LeoMendesEsEtml/2510_RegulationChauffage/doc/6.Graphique, Schéma/3.Doxygen/rtf/adc__ads124s08_8py.rtf

begin bodyRÃ©fÃ©rence du fichier C:/Users/thebi/Documents/2510_RegulationChauffage/doc/9.SoftWare/Doxygen/src/app/adc_ads124s08.py
AAAAAAAAAEAAAAAAAAAE
Driver pour l'ADC ADS124S08 avec communication SPI.
Classes
class app.adc_ads124s08.Ads124s08Driver pour l'ADC ADS124S08 avec interface SPI.
Espaces de nommage
namespace app
namespace app.adc_ads124s08
Fonctions
app.adc_ads124s08.encode_gain (pga_gain)
Encode le gain PGA en code binaire pour le registre.

app.adc_ads124s08.encode_idac_uA (idac_uA)
Encode la magnitude IDAC en code binaire pour le registre.

app.adc_ads124s08.sign_extend_24 (b0, b1, b2)
Ã‰tend le signe d'un code ADC 24 bits vers 32 bits.

Variables
int app.adc_ads124s08.REG_ID = 0x00
int app.adc_ads124s08.REG_STATUS = 0x01
int app.adc_ads124s08.REG_INPMUX = 0x02
int app.adc_ads124s08.REG_PGA = 0x03
int app.adc_ads124s08.REG_DATARATE = 0x04
int app.adc_ads124s08.REG_REF = 0x05
int app.adc_ads124s08.REG_IDACMUX = 0x07
int app.adc_ads124s08.REG_SYS = 0x09
int app.adc_ads124s08.REG_IDACMAG = 0x06
int app.adc_ads124s08.CMD_RESET = 0x06
int app.adc_ads124s08.CMD_START = 0x08
int app.adc_ads124s08.CMD_STOP = 0x0A
int app.adc_ads124s08.CMD_RDATA = 0x12
tuple app.adc_ads124s08.FS = (1 << 23) - 1
dict app.adc_ads124s08.CHANNELS

Description dÃ©taillÃ©e
Driver pour l'ADC ADS124S08 avec communication SPI.
Ce module fournit une interface complÃ¨te pour la communication avec l'ADC ADS124S08 via SPI en mode 1.0. Supporte la mesure de rÃ©sistance et tempÃ©rature avec configuration automatique des registres. SÃ Reset â†’ Configuration â†’ Mesure bloquante avec DRDY.
Auteur
LÃ©o Mendes @project 2510_RegulationsChauffage @Mandant Oblo_solution
Date
2025-09-18
Version
1.0.0
Copyright
Copyright (c) 2025
