LeoMendesEsEtml/2510_RegulationChauffage/doc/6.Graphique, Schéma/3.Doxygen/rtf/annotated.rtf

begin bodyListe des classes
Liste des classes, structures, unions et interfaces avec une brÃ¨ve description :
app.hw_mux_adg731.Adg731MuxSpi (Pilote SPI pour multiplexeurs ADG731 ) pagenum
app.adc_ads124s08.Ads124s08 (Driver pour l'ADC ADS124S08 avec interface SPI ) pagenum
app.api_client.ApiClient (Client pour interroger les APIs oblosolutions.ch ) pagenum
app.api_client.ApiError (Exception pour les erreurs d'API ) pagenum
app.front_led_management.LedErrorIndicator (Gestionnaire de LED avec patterns d'erreur ) pagenum
app.resistance_simulation.ResistanceSimulationError (Exception pour les erreurs de simulation de rÃ©sistance ) pagenum
app.resistance_simulation.ResistanceSimulator (ContrÃ´leur pour la simulation de rÃ©sistance via MUX ) pagenum
app.hw_tmux1204.Tmux1204 (Pilote pour le multiplexeur TMUX1204 ) pagenum
