LeoMendesEsEtml/2510_RegulationChauffage/doc/6.Graphique, Schéma/3.Doxygen/rtf/classapp_1_1adc__ads124s08_1_1_ads124s08.rtf

begin bodyRÃ©fÃ©rence de la classe app.adc_ads124s08.Ads124s08
AAAAAAAABSAAAAAAAABS
Driver pour l'ADC ADS124S08 avec interface SPI.
Graphe de collaboration de app.adc_ads124s08.Ads124s08:
IMAGE

Fonctions membres publiques
__init__ (self)
Constructeur de la classe Ads124s08.

read_id (self)
Lit le registre d'identification de l'ADC.

close (self)
Ferme les interfaces SPI et GPIO proprement.

wait_drdy_falling_edge (self, timeout_s)
Attend un front descendant sur DRDY (HIGH -> LOW) avec timeout.

set_single_shot_lowlatency (self, dr_nibble)
Configure le mode single-shot low-latency de l'ADC.

configure_channel (self, channel_index, pga_gain, idac_uA)
Configure un canal ADC avec ses paramÃ¨tres de mesure.

start (self)
DÃ©marre une conversion ADC.

stop (self)
ArrÃªte une conversion ADC en cours.

read_code24 (self)
Lit un code de donnÃ©es 24 bits depuis l'ADC.

measure_resistance (self, rref_ohm, pga_gain, timeout_s)
Mesure la rÃ©sistance d'une sonde via l'ADC.

measure_temperature (self, sensor_name, rref_ohm, pga_gain, timeout_s)
Mesure la tempÃ©rature d'un capteur via l'ADC.

read_gain (self)
Lit le registre de gain PGA pour diagnostic.

read_ref (self)
Lit le registre de configuration de la rÃ©fÃ©rence.

read_inpmux (self)
Lit le registre de configuration du multiplexeur d'entrÃ©e.

Attributs publics
spi = spidev.SpiDev()
gpio_drdy = GPIO(GPIO_CHIP_PATH, ADC_DRDY, "in")
Fonctions membres protÃ©gÃ©es
_rreg (self, addr, nbytes)
Lit un ou plusieurs registres de l'ADC via SPI.

_wreg (self, addr, data_bytes)
Ã‰crit dans un ou plusieurs registres de l'ADC via SPI.

_sclk_nudge (self)
Envoie un coup de pouce sur SCLK pour synchroniser DRDY.

_ensure_drdy_high (self, timeout_ms)
Assure que le signal DRDY est Ã l'Ã©tat HIGH.

Description dÃ©taillÃ©e
Driver pour l'ADC ADS124S08 avec interface SPI.
Cette classe encapsule toutes les fonctionnalitÃ©s nÃ©cessaires pour communiquer avec l'ADC ADS124S08 via SPI en mode 1.0. Supporte la configuration automatique, la mesure de rÃ©sistance et la conversion en tempÃ©rature.
Note
L'ADC doit Ãªtre connectÃ© via SPI1 et le signal DRDY sur GPIO.
Voir Ã©galement
configure_channel, measure_resistance, measure_temperature

AAAAAAAABTAAAAAAAABTDocumentation des constructeurs et destructeur
app.adc_ads124s08.Ads124s08.__init__ ( self)
AAAAAAAABUAAAAAAAABU
Constructeur de la classe Ads124s08.
Initialise la communication SPI, configure le GPIO DRDY, effectue un reset de l'ADC et vÃ©rifie la communication en lisant le registre d'identification.
Exceptions
Peut | lever des exceptions SPI ou GPIO en cas d'Ã©chec.
Postcondition L'ADC est prÃªt pour la configuration et les mesures.

AAAAAAAABVAAAAAAAABVDocumentation des fonctions membres
app.adc_ads124s08.Ads124s08._ensure_drdy_high ( self, timeout_ms)[protected]
AAAAAAAABWAAAAAAAABW
Assure que le signal DRDY est Ã l'Ã©tat HIGH.
Attend que DRDY passe Ã HIGH avec possibilitÃ© de coup de pouce sur SCLK si nÃ©cessaire. Timeout configurable.
ParamÃ¨tres
timeout_ms | Timeout en millisecondes pour l'attente.
Renvoie True si DRDY est HIGH, False en cas de timeout.
Note
MÃ©thode critique pour la synchronisation des conversions.
Voir Ã©galement
wait_drdy_falling_edge
Voici le graphe d'appel pour cette fonction :
IMAGE
app.adc_ads124s08.Ads124s08._rreg ( self, addr, nbytes)[protected]
AAAAAAAABXAAAAAAAABX
Lit un ou plusieurs registres de l'ADC via SPI.
Utilise la commande RREG de l'ADS124S08 pour lire des registres consÃ©cutifs starting Ã l'adresse donnÃ©e.
ParamÃ¨tres
addr | Adresse du premier registre Ã lire (0x00-0x1F).
nbytes | Nombre d'octets Ã lire.
Renvoie Liste des valeurs lues depuis les registres.
Note
MÃ©thode privÃ©e pour les opÃ©rations internes du driver.
Voir Ã©galement
_wreg
Voici le graphe des appelants de cette fonction :
IMAGE
app.adc_ads124s08.Ads124s08._sclk_nudge ( self)[protected]
AAAAAAAABYAAAAAAAABY
Envoie un coup de pouce sur SCLK pour synchroniser DRDY.
Effectue une lecture factice du registre STATUS pour gÃ©nÃ©rer des transitions sur SCLK et forcer DRDY Ã l'Ã©tat HIGH.
Renvoie
Rien.
Note
UtilisÃ© quand DRDY reste bloquÃ© Ã LOW de maniÃ¨re inattendue.
Voir Ã©galement
_ensure_drdy_high
Voici le graphe des appelants de cette fonction :
IMAGE
app.adc_ads124s08.Ads124s08._wreg ( self, addr, data_bytes)[protected]
AAAAAAAABZAAAAAAAABZ
Ã‰crit dans un ou plusieurs registres de l'ADC via SPI.
Utilise la commande WREG de l'ADS124S08 pour Ã©crire des donnÃ©es dans des registres consÃ©cutifs.
ParamÃ¨tres
addr | Adresse du premier registre Ã Ã©crire (0x00-0x1F).
data_bytes | Liste des octets Ã Ã©crire dans les registres.
Renvoie Rien.
Note
MÃ©thode privÃ©e pour les opÃ©rations internes du driver.
Voir Ã©galement
_rreg
Voici le graphe d'appel pour cette fonction :
IMAGE
Voici le graphe des appelants de cette fonction :
IMAGE
app.adc_ads124s08.Ads124s08.close ( self)
AAAAAAAACAAAAAAAAACA
Ferme les interfaces SPI et GPIO proprement.
LibÃ¨re les ressources systÃ¨me utilisÃ©es par le driver. MÃ©thode Ã appeler avant la destruction de l'objet.
Renvoie
Rien.
Note
Ignore les erreurs de fermeture pour Ã©viter les exceptions.
Voir Ã©galement
init
Voici le graphe d'appel pour cette fonction :
IMAGE
Voici le graphe des appelants de cette fonction :
IMAGE
app.adc_ads124s08.Ads124s08.configure_channel ( self, channel_index, pga_gain, idac_uA)
AAAAAAAACBAAAAAAAACB
Configure un canal ADC avec ses paramÃ¨tres de mesure.
Configure complÃ¨tement un canal ADC avec le gain PGA, le courant IDAC et le routage des entrÃ©es analogiques. Effectue une configuration sÃ©quentielle de tous les registres.
ParamÃ¨tres
channel_index | Index du canal physique (1-4).
pga_gain | Gain de l'amplificateur programmable (1-128).
idac_uA | Courant IDAC en microampÃ¨res (10-2000).
Renvoie Rien.
Exceptions
ValueError | si le canal ou les paramÃ¨tres sont invalides.
Voir Ã©galement encode_gain, encode_idac_uA
Voici le graphe d'appel pour cette fonction :
IMAGE
app.adc_ads124s08.Ads124s08.measure_resistance ( self, rref_ohm, pga_gain, timeout_s)
AAAAAAAACCAAAAAAAACC
Mesure la rÃ©sistance d'une sonde via l'ADC.
Effectue une mesure complÃ¨te: dÃ©marrage de conversion, attente DRDY, lecture du code et calcul de la rÃ©sistance selon la formule ratiomÃ©trique.
ParamÃ¨tres
rref_ohm | RÃ©sistance de rÃ©fÃ©rence en ohms.
pga_gain | Gain PGA utilisÃ© pour la mesure.
timeout_s | Timeout en secondes pour la conversion.
Renvoie RÃ©sistance mesurÃ©e en ohms ou None en cas d'erreur.
Note
Utilise la formule: R = |code|/FS * (Rref / gain).
Voir Ã©galement
measure_temperature, configure_channel
Voici le graphe d'appel pour cette fonction :
IMAGE
Voici le graphe des appelants de cette fonction :
IMAGE
app.adc_ads124s08.Ads124s08.measure_temperature ( self, sensor_name, rref_ohm, pga_gain, timeout_s)
AAAAAAAACDAAAAAAAACD
Mesure la tempÃ©rature d'un capteur via l'ADC.
Effectue une mesure de rÃ©sistance puis utilise les tables de conversion de capteurs pour obtenir la tempÃ©rature correspondante en degrÃ©s Celsius.
ParamÃ¨tres
sensor_name | Nom du capteur (doit exister dans SENSOR_TABLES).
rref_ohm | RÃ©sistance de rÃ©fÃ©rence en ohms.
pga_gain | Gain PGA utilisÃ© pour la mesure.
timeout_s | Timeout en secondes pour la conversion.
Renvoie TempÃ©rature mesurÃ©e en Â°C ou None si erreur.
Exceptions
Retourne | None si capteur inconnu ou hors plage.
Voir Ã©galement measure_resistance, resistance_to_temperature_dynamic
Voici le graphe d'appel pour cette fonction :
IMAGE
app.adc_ads124s08.Ads124s08.read_code24 ( self)
AAAAAAAACEAAAAAAAACE
Lit un code de donnÃ©es 24 bits depuis l'ADC.
Utilise la commande RDATA pour lire les 3 octets de donnÃ©es de conversion et les convertit en entier signÃ©.
Renvoie
Valeur signÃ©e 24 bits ou None en cas d'erreur SPI.
Note
Doit Ãªtre appelÃ© aprÃ¨s dÃ©tection du front descendant DRDY.
Voir Ã©galement
sign_extend_24, measure_resistance
Voici le graphe d'appel pour cette fonction :
IMAGE
Voici le graphe des appelants de cette fonction :
IMAGE
app.adc_ads124s08.Ads124s08.read_gain ( self)
AAAAAAAACFAAAAAAAACF
Lit le registre de gain PGA pour diagnostic.
Effectue une lecture du registre PGA et affiche sa valeur pour vÃ©rification de la configuration du gain.
Renvoie
Valeur brute du registre PGA (0x00-0xFF).
Note
UtilisÃ© principalement pour le debug et la vÃ©rification.
Voir Ã©galement
configure_channel
Voici le graphe d'appel pour cette fonction :
IMAGE
app.adc_ads124s08.Ads124s08.read_id ( self)
AAAAAAAACGAAAAAAAACG
Lit le registre d'identification de l'ADC.
Effectue une lecture du registre ID (0x00) pour vÃ©rifier la communication SPI et identifier le type d'ADC connectÃ©.
Renvoie
Valeur du registre ID (0x00-0xFF) ou None en cas d'erreur.
Note
UtilisÃ© principalement pour la vÃ©rification de communication.
Voir Ã©galement
init
app.adc_ads124s08.Ads124s08.read_inpmux ( self)
AAAAAAAACHAAAAAAAACH
Lit le registre de configuration du multiplexeur d'entrÃ©e.
Effectue une lecture du registre INPMUX et affiche sa valeur pour vÃ©rification du routage des entrÃ©es analogiques.
Renvoie
Valeur brute du registre INPMUX (0x00-0xFF).
Note
UtilisÃ© principalement pour le debug et la vÃ©rification.
Voir Ã©galement
configure_channel
app.adc_ads124s08.Ads124s08.read_ref ( self)
AAAAAAAACIAAAAAAAACI
Lit le registre de configuration de la rÃ©fÃ©rence.
Effectue une lecture du registre REF et affiche sa valeur pour vÃ©rification de la configuration de la rÃ©fÃ©rence.
Renvoie
Valeur brute du registre REF (0x00-0xFF).
Note
UtilisÃ© principalement pour le debug et la vÃ©rification.
Voir Ã©galement
configure_channel
Voici le graphe d'appel pour cette fonction :
IMAGE
app.adc_ads124s08.Ads124s08.set_single_shot_lowlatency ( self, dr_nibble)
AAAAAAAACJAAAAAAAACJ
Configure le mode single-shot low-latency de l'ADC.
Configure le registre DATARATE pour utiliser le mode single-shot avec filtre low-latency et data rate spÃ©cifiÃ©.
ParamÃ¨tres
dr_nibble | Code de data rate (4 bits, 0x00-0x0F).
Renvoie Rien.
Note
Mode optimisÃ© pour des mesures rapides et ponctuelles.
Voir Ã©galement
configure_channel
Voici le graphe des appelants de cette fonction :
IMAGE
app.adc_ads124s08.Ads124s08.start ( self)
AAAAAAAACKAAAAAAAACK
DÃ©marre une conversion ADC.
Assure que DRDY est Ã HIGH puis envoie la commande START pour initier une nouvelle conversion sur le canal configurÃ©.
Renvoie
Rien.
Note
DRDY doit Ãªtre HIGH avant le START pour une conversion valide.
Voir Ã©galement
stop, wait_drdy_falling_edge
Voici le graphe des appelants de cette fonction :
IMAGE
app.adc_ads124s08.Ads124s08.stop ( self)
AAAAAAAACLAAAAAAAACL
ArrÃªte une conversion ADC en cours.
Envoie la commande STOP pour interrompre toute conversion en cours et remettre l'ADC en Ã©tat idle.
Renvoie
Rien.
Note
UtilisÃ© aprÃ¨s lecture des donnÃ©es ou en cas d'erreur.
Voir Ã©galement
start, read_code24
Voici le graphe des appelants de cette fonction :
IMAGE
app.adc_ads124s08.Ads124s08.wait_drdy_falling_edge ( self, timeout_s)
AAAAAAAACMAAAAAAAACM
Attend un front descendant sur DRDY (HIGH -> LOW) avec timeout.
Surveille le signal DRDY pour dÃ©tecter une transition de HIGH vers LOW, indiquant qu'une nouvelle conversion est disponible.
ParamÃ¨tres
timeout_s | Timeout en secondes pour l'attente du front.
Renvoie True si front descendant dÃ©tectÃ©, False en cas de timeout.
Note
MÃ©thode cruciale pour la synchronisation des mesures.
Voir Ã©galement
measure_resistance
Voici le graphe d'appel pour cette fonction :
IMAGE
Voici le graphe des appelants de cette fonction :
IMAGE

AAAAAAAACNAAAAAAAACNDocumentation des donnÃ©es membres
app.adc_ads124s08.Ads124s08.gpio_drdy = GPIO(GPIO_CHIP_PATH, ADC_DRDY, "in")
AAAAAAAACOAAAAAAAACOapp.adc_ads124s08.Ads124s08.spi = spidev.SpiDev()
AAAAAAAACPAAAAAAAACP
La documentation de cette classe a Ã©tÃ© gÃ©nÃ©rÃ©e Ã partir du fichier suivant :
C:/Users/thebi/Documents/2510_RegulationChauffage/doc/9.SoftWare/Doxygen/src/app/adc_ads124s08.py
