LeoMendesEsEtml/2510_RegulationChauffage/doc/6.Graphique, Schéma/3.Doxygen/rtf/classapp_1_1front__led__management_1_1_led_error_indicator.rtf

begin bodyRÃ©fÃ©rence de la classe app.front_led_management.LedErrorIndicator
AAAAAAAADSAAAAAAAADS
Gestionnaire de LED avec patterns d'erreur.
Graphe de collaboration de app.front_led_management.LedErrorIndicator:
IMAGE

Attributs publics statiques
float BASE_BLINK_TIME = 0.2
float CYCLE_TIME = 10.0

Description dÃ©taillÃ©e
Gestionnaire de LED avec patterns d'erreur.
Classe pour contrÃ´ler une LED frontale avec diffÃ©rents patterns de clignotement selon les Ã©tats du systÃ¨me. Supporte les modes normal, standby, sÃ©quence en cours et divers patterns d'erreur avec clignotements codifiÃ©s.

AAAAAAAADTAAAAAAAADTDocumentation des donnÃ©es membres
float app.front_led_management.LedErrorIndicator.BASE_BLINK_TIME = 0.2[static]
AAAAAAAADUAAAAAAAADUfloat app.front_led_management.LedErrorIndicator.CYCLE_TIME = 10.0[static]
AAAAAAAADVAAAAAAAADV
La documentation de cette classe a Ã©tÃ© gÃ©nÃ©rÃ©e Ã partir du fichier suivant :
C:/Users/thebi/Documents/2510_RegulationChauffage/doc/9.SoftWare/Doxygen/src/app/front_led_management.py
