LeoMendesEsEtml/2510_RegulationChauffage/doc/6.Graphique, Schéma/3.Doxygen/rtf/classapp_1_1hw__mux__adg731_1_1_adg731_mux_spi.rtf

begin bodyRÃ©fÃ©rence de la classe app.hw_mux_adg731.Adg731MuxSpi
AAAAAAAADZAAAAAAAADZ
Pilote SPI pour multiplexeurs ADG731.
Graphe de collaboration de app.hw_mux_adg731.Adg731MuxSpi:
IMAGE

Fonctions membres publiques
__init__ (self, speed_hz=100000)
Initialise le pilote pour les multiplexeurs ADG731.

close (self)
Ferme toutes les interfaces SPI.

set_channel (self, board_index, address)
Active un canal spÃ©cifique sur une carte donnÃ©e.

set_output_channel (self, channel_index)
Utilitaire simple pour sÃ©lectionner un canal de sortie.

Attributs publics
speed = speed_hz
list handles = []
Attributs publics statiques
list DEV = ["/dev/spidev0.0", "/dev/spidev0.1", "/dev/spidev0.2", "/dev/spidev0.3"]

Description dÃ©taillÃ©e
Pilote SPI pour multiplexeurs ADG731.
Classe pour contrÃ´ler jusqu'Ã 4 multiplexeurs ADG731 via l'interface SPI0. Chaque multiplexeur peut gÃ©rer 32 canaux. Configure automatiquement les paramÃ¨tres SPI optimaux et gÃ¨re la communication avec les circuits.

AAAAAAAAEAAAAAAAAAEADocumentation des constructeurs et destructeur
app.hw_mux_adg731.Adg731MuxSpi.__init__ ( self, speed_hz = 100000)
AAAAAAAAEBAAAAAAAAEB
Initialise le pilote pour les multiplexeurs ADG731.
Configure l'interface SPI pour chaque canal disponible, dÃ©finit les paramÃ¨tres de communication et initialise les handles pour jusqu'Ã 4 cartes multiplexeurs.
ParamÃ¨tres
speed_hz | Vitesse SPI en Hz (par dÃ©faut 100kHz).

AAAAAAAAECAAAAAAAAECDocumentation des fonctions membres
app.hw_mux_adg731.Adg731MuxSpi.close ( self)
AAAAAAAAEDAAAAAAAAED
Ferme toutes les interfaces SPI.
Parcourt tous les handles SPI ouverts et les ferme proprement. GÃ¨re les erreurs de fermeture pour Ã©viter les exceptions lors du nettoyage.
app.hw_mux_adg731.Adg731MuxSpi.set_channel ( self, board_index, address)
AAAAAAAAEEAAAAAAAAEE
Active un canal spÃ©cifique sur une carte donnÃ©e.
Envoie la commande de sÃ©lection de canal vers la carte multiplexeur spÃ©cifiÃ©e. GÃ©nÃ¨re l'octet de contrÃ´le et l'envoie via SPI.
ParamÃ¨tres
board_index | Index de la carte (0-3).
address | Adresse du canal Ã activer (0-31).
Renvoie Octet de contrÃ´le envoyÃ©, ou None si erreur.
Exceptions
ValueError | Si l'index de carte est hors plage.
Voici le graphe d'appel pour cette fonction :
IMAGE
Voici le graphe des appelants de cette fonction :
IMAGE
app.hw_mux_adg731.Adg731MuxSpi.set_output_channel ( self, channel_index)
AAAAAAAAEFAAAAAAAAEF
Utilitaire simple pour sÃ©lectionner un canal de sortie.
Fonction de commoditÃ© qui utilise automatiquement la carte 0 et mappe directement l'index de canal sur l'adresse du multiplexeur.
ParamÃ¨tres
channel_index | Index du canal de sortie (0-31).
Renvoie Octet de contrÃ´le envoyÃ©, ou None si erreur.
Exceptions
ValueError | Si l'index de canal est hors plage.
Voici le graphe d'appel pour cette fonction :
IMAGE

AAAAAAAAEGAAAAAAAAEGDocumentation des donnÃ©es membres
list app.hw_mux_adg731.Adg731MuxSpi.DEV = ["/dev/spidev0.0", "/dev/spidev0.1", "/dev/spidev0.2", "/dev/spidev0.3"][static]
AAAAAAAAEHAAAAAAAAEHlist app.hw_mux_adg731.Adg731MuxSpi.handles = []
AAAAAAAAEIAAAAAAAAEIapp.hw_mux_adg731.Adg731MuxSpi.speed = speed_hz
AAAAAAAAEJAAAAAAAAEJ
La documentation de cette classe a Ã©tÃ© gÃ©nÃ©rÃ©e Ã partir du fichier suivant :
C:/Users/thebi/Documents/2510_RegulationChauffage/doc/9.SoftWare/Doxygen/src/app/hw_mux_adg731.py
