LeoMendesEsEtml/2510_RegulationChauffage/doc/6.Graphique, Schéma/3.Doxygen/rtf/classapp_1_1resistance__simulation_1_1_resistance_simulation_error.rtf

begin bodyRÃ©fÃ©rence de la classe app.resistance_simulation.ResistanceSimulationError
AAAAAAAAHOAAAAAAAAHO
Exception pour les erreurs de simulation de rÃ©sistance.
Graphe d'hÃ©ritage de app.resistance_simulation.ResistanceSimulationError:
IMAGE

Graphe de collaboration de app.resistance_simulation.ResistanceSimulationError:
IMAGE

Description dÃ©taillÃ©e
Exception pour les erreurs de simulation de rÃ©sistance.
Exception spÃ©cialisÃ©e levÃ©e lors d'erreurs dans le processus de simulation de rÃ©sistance via le multiplexeur.

La documentation de cette classe a Ã©tÃ© gÃ©nÃ©rÃ©e Ã partir du fichier suivant :
C:/Users/thebi/Documents/2510_RegulationChauffage/doc/9.SoftWare/Doxygen/src/app/resistance_simulation.py
