LeoMendesEsEtml/2510_RegulationChauffage/doc/6.Graphique, Schéma/3.Doxygen/rtf/classapp_1_1resistance__simulation_1_1_resistance_simulator.rtf

begin bodyRÃ©fÃ©rence de la classe app.resistance_simulation.ResistanceSimulator
AAAAAAAAHPAAAAAAAAHP
ContrÃ´leur pour la simulation de rÃ©sistance via MUX.
Graphe de collaboration de app.resistance_simulation.ResistanceSimulator:
IMAGE

Fonctions membres publiques
__init__ (self, int speed_hz=100000)
Initialise le simulateur de rÃ©sistance.

close (self)
Ferme les connexions du simulateur.

float calculate_parallel_resistance (self, List[float] resistances)
Calcule la rÃ©sistance Ã©quivalente de rÃ©sistances en parallÃ¨le.

bool apply_resistance_simulation (self, float target_resistance, int measurement_channel, str sensor_type="Ni1000 TK5000")
Applique une rÃ©sistance simulÃ©e via le MUX sur le canal de mesure.

Dict[str, any] get_current_simulation (self)
Retourne l'Ã©tat actuel de la simulation.

bool validate_resistance_applied (self, float expected_resistance, float tolerance=0.10)
Valide que la rÃ©sistance appliquÃ©e correspond Ã l'attendu.

reset_simulation (self)
Remet la simulation Ã zÃ©ro (dÃ©sactive tous les canaux).

Attributs publics
mux = None
speed_hz = speed_hz
current_resistance = None
list active_channels = []

Description dÃ©taillÃ©e
ContrÃ´leur pour la simulation de rÃ©sistance via MUX.
Classe principale qui encapsule toute la logique de simulation de rÃ©sistance en utilisant le multiplexeur ADG731 et les mappings de rÃ©sistances calibrÃ©es.

AAAAAAAAHQAAAAAAAAHQDocumentation des constructeurs et destructeur
app.resistance_simulation.ResistanceSimulator.__init__ ( self, int speed_hz = 100000)
AAAAAAAAHRAAAAAAAAHR
Initialise le simulateur de rÃ©sistance.
Constructeur qui configure le multiplexeur ADG731 avec la vitesse SPI spÃ©cifiÃ©e et initialise les variables d'Ã©tat du simulateur.
ParamÃ¨tres
speed_hz | Vitesse de communication SPI en Hz (dÃ©faut: 100kHz).
Exceptions ResistanceSimulationError | si l'initialisation du MUX Ã©choue.

AAAAAAAAHSAAAAAAAAHSDocumentation des fonctions membres
bool app.resistance_simulation.ResistanceSimulator.apply_resistance_simulation ( self, float target_resistance, int measurement_channel, str sensor_type = "Ni1000 TK5000")
AAAAAAAAHTAAAAAAAAHT
Applique une rÃ©sistance simulÃ©e via le MUX sur le canal de mesure.
Fonction principale qui recherche le canal MUX optimal pour simuler la rÃ©sistance cible, configure le multiplexeur et mÃ©morise l'Ã©tat de la simulation.
ParamÃ¨tres
target_resistance | RÃ©sistance Ã simuler [Ohms].
measurement_channel | Canal sur lequel la mesure a Ã©tÃ© faite (info).
sensor_type | Type de sonde pour sÃ©lectionner la carte MUX.
Renvoie True si succÃ¨s, False en cas d'erreur.
float app.resistance_simulation.ResistanceSimulator.calculate_parallel_resistance ( self, List[float] resistances)
AAAAAAAAHUAAAAAAAAHU
Calcule la rÃ©sistance Ã©quivalente de rÃ©sistances en parallÃ¨le.
Applique la formule 1/Req = 1/R1 + 1/R2 + ... + 1/Rn pour calculer la rÃ©sistance Ã©quivalente d'un ensemble de rÃ©sistances connectÃ©es en parallÃ¨le.
ParamÃ¨tres
resistances | Liste des valeurs de rÃ©sistance en parallÃ¨le [Ohms].
Renvoie RÃ©sistance Ã©quivalente calculÃ©e [Ohms]. Retourne l'infini si la liste est vide.
app.resistance_simulation.ResistanceSimulator.close ( self)
AAAAAAAAHVAAAAAAAAHV
Ferme les connexions du simulateur.
MÃ©thode de nettoyage qui ferme proprement la connexion SPI avec le multiplexeur et libÃ¨re les ressources.
Voici le graphe d'appel pour cette fonction :
IMAGE
Voici le graphe des appelants de cette fonction :
IMAGE
Dict[str, any] app.resistance_simulation.ResistanceSimulator.get_current_simulation ( self)
AAAAAAAAHWAAAAAAAAHW
Retourne l'Ã©tat actuel de la simulation.
Fonction d'interrogation qui fournit un dictionnaire contenant toutes les informations sur l'Ã©tat actuel de la simulation de rÃ©sistance.
Renvoie
Dictionnaire contenant les informations actuelles:
▪ esistance: valeur appliquÃ©e [Ohms] ou None
▪ ctive_channels: liste des canaux MUX actifs
▪ ux_available: disponibilitÃ© du multiplexeur
app.resistance_simulation.ResistanceSimulator.reset_simulation ( self)
AAAAAAAAHXAAAAAAAAHX
Remet la simulation Ã zÃ©ro (dÃ©sactive tous les canaux).
ProcÃ©dure de nettoyage qui dÃ©sactive tous les canaux de tous les multiplexeurs et remet l'Ã©tat de simulation Ã sa configuration initiale.
bool app.resistance_simulation.ResistanceSimulator.validate_resistance_applied ( self, float expected_resistance, float tolerance = 0.10)
AAAAAAAAHYAAAAAAAAHY
Valide que la rÃ©sistance appliquÃ©e correspond Ã l'attendu.
Fonction de validation qui compare la rÃ©sistance actuellement appliquÃ©e avec la valeur attendue en tenant compte d'une tolÃ©rance relative spÃ©cifiÃ©e.
ParamÃ¨tres
expected_resistance | RÃ©sistance attendue pour la validation [Ohms].
tolerance | TolÃ©rance relative acceptÃ©e (dÃ©faut: 10%).
Renvoie True si la rÃ©sistance est dans la tolÃ©rance.

AAAAAAAAHZAAAAAAAAHZDocumentation des donnÃ©es membres
list app.resistance_simulation.ResistanceSimulator.active_channels = []
AAAAAAAAIAAAAAAAAAIAapp.resistance_simulation.ResistanceSimulator.current_resistance = None
AAAAAAAAIBAAAAAAAAIBapp.resistance_simulation.ResistanceSimulator.mux = None
AAAAAAAAICAAAAAAAAICapp.resistance_simulation.ResistanceSimulator.speed_hz = speed_hz
AAAAAAAAIDAAAAAAAAID
La documentation de cette classe a Ã©tÃ© gÃ©nÃ©rÃ©e Ã partir du fichier suivant :
C:/Users/thebi/Documents/2510_RegulationChauffage/doc/9.SoftWare/Doxygen/src/app/resistance_simulation.py
