LeoMendesEsEtml/2510_RegulationChauffage/doc/6.Graphique, Schéma/3.Doxygen/rtf/cm5__config_8py.rtf

begin bodyRÃ©fÃ©rence du fichier C:/Users/thebi/Documents/2510_RegulationChauffage/doc/9.SoftWare/Doxygen/src/config_module/cm5_config.py
AAAAAAAAAUAAAAAAAAAU
Configuration matÃ©rielle pour plateforme CM5.
Espaces de nommage
namespace config_module
namespace config_module.cm5_config
Fonctions
config_module.cm5_config.build_hw ()
Initialise et configure tout le matÃ©riel CM5.

Variables
list config_module.cm5_config.ADC_CHANNELS = [1, 2, 3, 4]

Description dÃ©taillÃ©e
Configuration matÃ©rielle pour plateforme CM5.
Ce module fournit la configuration des canaux ADC et la fonction d'initialisation complÃ¨te du matÃ©riel (LED, TMUX, ADC). Centralise la crÃ©ation des instances matÃ©rielles avec cÃ¢blage fixe CM5.
Auteur
LÃ©o Mendes @project 2510_RegulationsChauffage @Mandant Oblo_solution
Date
2025-09-18
Version
1.0.0
Copyright
Copyright (c) 2025
