LeoMendesEsEtml/2510_RegulationChauffage/doc/6.Graphique, Schéma/3.Doxygen/rtf/config__loader_8py.rtf

begin bodyRÃ©fÃ©rence du fichier C:/Users/thebi/Documents/2510_RegulationChauffage/doc/9.SoftWare/Doxygen/src/app/config_loader.py
AAAAAAAAAGAAAAAAAAAG
Chargeur de configuration JSON pour le systÃ¨me de mesure.
Espaces de nommage
namespace app
namespace app.config_loader
Fonctions
app.config_loader.load_config (path)

Description dÃ©taillÃ©e
Chargeur de configuration JSON pour le systÃ¨me de mesure.
Ce module fournit une fonction simple pour charger et parser un fichier de configuration JSON contenant les paramÃ¨tres des capteurs, timeouts et autres paramÃ¨tres systÃ¨me.
Auteur
LÃ©o Mendes @project 2510_RegulationsChauffage @Mandant Oblo_solution
Date
2025-09-18
Version
1.0.0
Copyright
Copyright (c) 2025
