LeoMendesEsEtml/2510_RegulationChauffage/doc/6.Graphique, Schéma/3.Doxygen/rtf/dir_194a6b39714955f6d6b57228b865c8d6.rtf

begin bodyRÃ©pertoire de rÃ©fÃ©rence de C:/Users/thebi/Documents/2510_RegulationChauffage/doc/9.SoftWare/Doxygen/src/app
AAAAAAAAKPAAAAAAAAKPGraphe des dÃ©pendances de rÃ©pertoires pour app:
IMAGE
Fichiers
fichier __init__.py
fichier adc_ads124s08.py
Driver pour l'ADC ADS124S08 avec communication SPI.
fichier api_client.py
Client API pour les services oblosolutions.ch.
fichier config_loader.py
Chargeur de configuration JSON pour le systÃ¨me de mesure.
fichier front_led_management.py
Gestionnaire de LED frontale avec patterns d'erreur.
fichier hw_mux_adg731.py
Pilote pour multiplexeur ADG731 via interface SPI.
fichier hw_tmux1204.py
Pilote pour multiplexeur TMUX1204 de sÃ©lection de rÃ©sistance de rÃ©fÃ©rence.
fichier main.py
SystÃ¨me de mesure et simulation de tempÃ©rature.
fichier mesure_24v_dry_contact.py
Module de test des entrÃ©es/sorties 24V pour contacts secs.
fichier pins_cm5.py
Mapping GPIO et SPI fixÃ©s pour la plateforme CM5.
fichier resistance_mapping.py
Mapping des rÃ©sistances TMUX par type de sonde de tempÃ©rature.
fichier resistance_simulation.py
Module pour commander le MUX de simulation de rÃ©sistance.
fichier sensor_profiles.py
Profils capteurs extraits de 'Calcul ADC.xlsx' (Feuil1).
fichier temperature_conversion.py
Module de conversion rÃ©sistance/tempÃ©rature via interpolation linÃ©aire.
fichier temperature_simulation.py
Module de calcul de tempÃ©rature simulÃ©e selon formule prÃ©dictive.
fichier test_lm70_compatible.py
fichier test_spi_adc.py
