LeoMendesEsEtml/2510_RegulationChauffage/doc/6.Graphique, Schéma/3.Doxygen/rtf/dir_eeb81aa684f40f7b9c7a7aac642db388.rtf

begin bodyRÃ©pertoire de rÃ©fÃ©rence de C:/Users/thebi/Documents/2510_RegulationChauffage/doc/9.SoftWare/Doxygen/src/config_module
AAAAAAAAKQAAAAAAAAKQGraphe des dÃ©pendances de rÃ©pertoires pour config_module:
IMAGE
Fichiers
fichier __init__.py
fichier cm5_config.py
Configuration matÃ©rielle pour plateforme CM5.
