LeoMendesEsEtml/2510_RegulationChauffage/doc/6.Graphique, Schéma/3.Doxygen/rtf/files.rtf

begin bodyListe des fichiers
Liste de tous les fichiers avec une brÃ¨ve description :
C:/Users/thebi/Documents/2510_RegulationChauffage/doc/9.SoftWare/Doxygen/src/app/__init__.py pagenum
C:/Users/thebi/Documents/2510_RegulationChauffage/doc/9.SoftWare/Doxygen/src/app/adc_ads124s08.py (Driver pour l'ADC ADS124S08 avec communication SPI ) pagenum
C:/Users/thebi/Documents/2510_RegulationChauffage/doc/9.SoftWare/Doxygen/src/app/api_client.py (Client API pour les services oblosolutions.ch ) pagenum
C:/Users/thebi/Documents/2510_RegulationChauffage/doc/9.SoftWare/Doxygen/src/app/config_loader.py (Chargeur de configuration JSON pour le systÃ¨me de mesure ) pagenum
C:/Users/thebi/Documents/2510_RegulationChauffage/doc/9.SoftWare/Doxygen/src/app/front_led_management.py (Gestionnaire de LED frontale avec patterns d'erreur ) pagenum
C:/Users/thebi/Documents/2510_RegulationChauffage/doc/9.SoftWare/Doxygen/src/app/hw_mux_adg731.py (Pilote pour multiplexeur ADG731 via interface SPI ) pagenum
C:/Users/thebi/Documents/2510_RegulationChauffage/doc/9.SoftWare/Doxygen/src/app/hw_tmux1204.py (Pilote pour multiplexeur TMUX1204 de sÃ©lection de rÃ©sistance de rÃ©fÃ©rence ) pagenum
C:/Users/thebi/Documents/2510_RegulationChauffage/doc/9.SoftWare/Doxygen/src/app/main.py (SystÃ¨me de mesure et simulation de tempÃ©rature ) pagenum
C:/Users/thebi/Documents/2510_RegulationChauffage/doc/9.SoftWare/Doxygen/src/app/mesure_24v_dry_contact.py (Module de test des entrÃ©es/sorties 24V pour contacts secs ) pagenum
C:/Users/thebi/Documents/2510_RegulationChauffage/doc/9.SoftWare/Doxygen/src/app/pins_cm5.py (Mapping GPIO et SPI fixÃ©s pour la plateforme CM5 ) pagenum
C:/Users/thebi/Documents/2510_RegulationChauffage/doc/9.SoftWare/Doxygen/src/app/resistance_mapping.py (Mapping des rÃ©sistances TMUX par type de sonde de tempÃ©rature ) pagenum
C:/Users/thebi/Documents/2510_RegulationChauffage/doc/9.SoftWare/Doxygen/src/app/resistance_simulation.py (Module pour commander le MUX de simulation de rÃ©sistance ) pagenum
C:/Users/thebi/Documents/2510_RegulationChauffage/doc/9.SoftWare/Doxygen/src/app/sensor_profiles.py (Profils capteurs extraits de 'Calcul ADC.xlsx' (Feuil1) ) pagenum
C:/Users/thebi/Documents/2510_RegulationChauffage/doc/9.SoftWare/Doxygen/src/app/temperature_conversion.py (Module de conversion rÃ©sistance/tempÃ©rature via interpolation linÃ©aire ) pagenum
C:/Users/thebi/Documents/2510_RegulationChauffage/doc/9.SoftWare/Doxygen/src/app/temperature_simulation.py (Module de calcul de tempÃ©rature simulÃ©e selon formule prÃ©dictive ) pagenum
C:/Users/thebi/Documents/2510_RegulationChauffage/doc/9.SoftWare/Doxygen/src/app/test_lm70_compatible.py pagenum
C:/Users/thebi/Documents/2510_RegulationChauffage/doc/9.SoftWare/Doxygen/src/app/test_spi_adc.py pagenum
C:/Users/thebi/Documents/2510_RegulationChauffage/doc/9.SoftWare/Doxygen/src/config_module/__init__.py pagenum
C:/Users/thebi/Documents/2510_RegulationChauffage/doc/9.SoftWare/Doxygen/src/config_module/cm5_config.py (Configuration matÃ©rielle pour plateforme CM5 ) pagenum
C:/Users/thebi/Documents/2510_RegulationChauffage/doc/9.SoftWare/Doxygen/src/webui/__init__.py pagenum
C:/Users/thebi/Documents/2510_RegulationChauffage/doc/9.SoftWare/Doxygen/src/webui/webui_server.py (Serveur web pour interface utilisateur de configuration ) pagenum
