LeoMendesEsEtml/2510_RegulationChauffage/doc/6.Graphique, Schéma/3.Doxygen/rtf/front__led__management_8py.rtf

begin bodyRÃ©fÃ©rence du fichier C:/Users/thebi/Documents/2510_RegulationChauffage/doc/9.SoftWare/Doxygen/src/app/front_led_management.py
AAAAAAAAAHAAAAAAAAAH
Gestionnaire de LED frontale avec patterns d'erreur.
Classes
class app.front_led_management.LedErrorIndicatorGestionnaire de LED avec patterns d'erreur.
Espaces de nommage
namespace app
namespace app.front_led_management
Fonctions
app.front_led_management.create_led_indicator (gpio_chip_path, led_pin)
Factory function pour crÃ©er une instance LedErrorIndicator.

Description dÃ©taillÃ©e
Gestionnaire de LED frontale avec patterns d'erreur.
Ce module fournit une classe pour gÃ©rer les clignotements et Ã©tats de la LED frontale avec diffÃ©rents patterns d'erreur. Supporte les modes continus, les clignotements d'erreur et la gestion thread-safe des patterns LED.
Auteur
LÃ©o Mendes @project 2510_RegulationsChauffage @Mandant Oblo_solution
Date
2025-09-18
Version
1.0.0
Copyright
Copyright (c) 2025
