LeoMendesEsEtml/2510_RegulationChauffage/doc/6.Graphique, Schéma/3.Doxygen/rtf/hierarchy.rtf

begin bodyHiÃ©rarchie des classes
Cette liste d'hÃ©ritage est classÃ©e approximativement par ordre alphabÃ©tique :
app.hw_mux_adg731.Adg731MuxSpi pagenum
app.adc_ads124s08.Ads124s08 pagenum
app.api_client.ApiClient pagenum
Exception
app.api_client.ApiError pagenum
app.resistance_simulation.ResistanceSimulationError pagenum

app.front_led_management.LedErrorIndicator pagenum
app.resistance_simulation.ResistanceSimulator pagenum
app.hw_tmux1204.Tmux1204 pagenum
