LeoMendesEsEtml/2510_RegulationChauffage/doc/6.Graphique, Schéma/3.Doxygen/rtf/hw__mux__adg731_8py.rtf

begin bodyRÃ©fÃ©rence du fichier C:/Users/thebi/Documents/2510_RegulationChauffage/doc/9.SoftWare/Doxygen/src/app/hw_mux_adg731.py
AAAAAAAAAIAAAAAAAAAI
Pilote pour multiplexeur ADG731 via interface SPI.
Classes
class app.hw_mux_adg731.Adg731MuxSpiPilote SPI pour multiplexeurs ADG731.
Espaces de nommage
namespace app
namespace app.hw_mux_adg731
Fonctions
app.hw_mux_adg731.adg731_ctrl_byte (address, enable=True)
GÃ©nÃ¨re le byte de contrÃ´le pour l'ADG731.

Description dÃ©taillÃ©e
Pilote pour multiplexeur ADG731 via interface SPI.
Ce module fournit un pilote pour contrÃ´ler les multiplexeurs ADG731 via l'interface SPI0. Supporte jusqu'Ã 4 cartes avec 32 canaux chacune. GÃ¨re la configuration SPI et l'envoi des commandes de contrÃ´le pour la sÃ©lection des canaux.
Auteur
LÃ©o Mendes @project 2510_RegulationsChauffage @Mandant Oblo_solution
Date
2025-09-18
Version
1.0.0
Copyright
Copyright (c) 2025
