LeoMendesEsEtml/2510_RegulationChauffage/doc/6.Graphique, Schéma/3.Doxygen/rtf/main_8py.rtf

begin bodyRÃ©fÃ©rence du fichier C:/Users/thebi/Documents/2510_RegulationChauffage/doc/9.SoftWare/Doxygen/src/app/main.py
AAAAAAAAAKAAAAAAAAAK
SystÃ¨me de mesure et simulation de tempÃ©rature.
Espaces de nommage
namespace app
namespace app.main
Fonctions
app.main.start_webui_server ()
Lance le serveur web local dans un thread sÃ©parÃ©.

app.main.save_last_state (channel=None, resistance_ohm=None, temperature_c=None, temperature_sim_c=None, error=None)
Sauvegarde l'Ã©tat courant et historique par canal dans un fichier JSON.

app.main.signal_handler (sig, frame)
Gestionnaire POSIX pour les signaux (Ctrl+C).

app.main.input_monitor ()
Thread d'Ã©coute des commandes utilisateur depuis stdin.

app.main.show_error_and_continue (error_pattern, sleep_time=2)
Affiche un motif LED d'erreur pendant un temps donnÃ© puis remet l'indicateur en mode 'sequence_running'.

app.main.run_measurement_sequence (cfg, mac_address, adc, tmux)
ExÃ©cute une sÃ©quence complÃ¨te de mesures pour tous les canaux activÃ©s selon la configuration fournie.

app.main.reload_timing_config ()
Recharge les paramÃ¨tres de temporisation depuis le fichier de configuration.

app.main.main ()
Point d'entrÃ©e principal du programme.

Variables
app.main.CURRENT_DIR = os.path.dirname(os.path.abspath(__file__))
app.main.SRC_DIR = os.path.dirname(CURRENT_DIR)
bool app.main.sequencer_running = False
app.main.stop_event = threading.Event()
app.main.force_sequence = threading.Event()
app.main.led_indicator = None

Description dÃ©taillÃ©e
SystÃ¨me de mesure et simulation de tempÃ©rature.
Ce module exÃ©cute des cycles de mesure ADC, convertit les valeurs en rÃ©sistances puis en tempÃ©ratures, rÃ©cupÃ¨re des paramÃ¨tres via une API distante, calcule une tempÃ©rature simulÃ©e, convertit cette tempÃ©rature en rÃ©sistance cible et applique la simulation via un multiplexeur matÃ©riel. Le module gÃ¨re Ã©galement un petit serveur web optionnel et un indicateur LED.
Auteur
LÃ©o Mendes @project 2510_RegulationsChauffage @Mandant Oblo_solution
Date
2025-09-18
Version
1.0.0
Copyright
Copyright (c) 2025
