LeoMendesEsEtml/2510_RegulationChauffage/doc/6.Graphique, Schéma/3.Doxygen/rtf/mesure__24v__dry__contact_8py.rtf

begin bodyRÃ©fÃ©rence du fichier C:/Users/thebi/Documents/2510_RegulationChauffage/doc/9.SoftWare/Doxygen/src/app/mesure_24v_dry_contact.py
AAAAAAAAALAAAAAAAAAL
Module de test des entrÃ©es/sorties 24V pour contacts secs.
Espaces de nommage
namespace app
namespace app.mesure_24v_dry_contact
Fonctions
app.mesure_24v_dry_contact.test_24v_dry_contact ()
Test des contacts secs I/O 24V.

app.mesure_24v_dry_contact.get_dry_contact_status ()
Retourne l'Ã©tat actuel des contacts secs.

Variables
int app.mesure_24v_dry_contact.CM_24V_OUT_1 = 13
int app.mesure_24v_dry_contact.CM_24V_SENSE_1 = 14
int app.mesure_24v_dry_contact.CM_24V_OUT_2 = 15
int app.mesure_24v_dry_contact.CM_24V_SENSE_2 = 16
int app.mesure_24v_dry_contact.io_24v_ch1_ok = 0
int app.mesure_24v_dry_contact.io_24v_ch2_ok = 0

Description dÃ©taillÃ©e
Module de test des entrÃ©es/sorties 24V pour contacts secs.
Ce module fournit des fonctions pour tester et valider les contacts secs via les interfaces I/O 24V. Permet de dÃ©tecter l'Ã©tat des contacts (ouvert/fermÃ©) sur deux canaux indÃ©pendants avec gestion des GPIO et temporisations appropriÃ©es.
Auteur
LÃ©o Mendes @project 2510_RegulationsChauffage @Mandant Oblo_solution
Date
2025-09-18
Version
1.0.0
Copyright
Copyright (c) 2025
