LeoMendesEsEtml/2510_RegulationChauffage/doc/6.Graphique, Schéma/3.Doxygen/rtf/namespaceapp.rtf

begin bodyRÃ©fÃ©rence de l'espace de nommage app
AAAAAAAAAWAAAAAAAAAWEspaces de nommage
namespace adc_ads124s08
namespace api_client
namespace config_loader
namespace front_led_management
namespace hw_mux_adg731
namespace hw_tmux1204
namespace main
namespace mesure_24v_dry_contact
namespace pins_cm5
namespace resistance_mapping
namespace resistance_simulation
namespace sensor_profiles
namespace temperature_conversion
namespace temperature_simulation
namespace test_lm70_compatible
namespace test_spi_adc
