LeoMendesEsEtml/2510_RegulationChauffage/doc/6.Graphique, Schéma/3.Doxygen/rtf/namespaceapp_1_1front__led__management.rtf

begin bodyRÃ©fÃ©rence de l'espace de nommage app.front_led_management
AAAAAAAADPAAAAAAAADPClasses
class LedErrorIndicatorGestionnaire de LED avec patterns d'erreur.
Fonctions
create_led_indicator (gpio_chip_path, led_pin)
Factory function pour crÃ©er une instance LedErrorIndicator.

AAAAAAAADQAAAAAAAADQDocumentation des fonctions
app.front_led_management.create_led_indicator ( gpio_chip_path, led_pin)
AAAAAAAADRAAAAAAAADR
Factory function pour crÃ©er une instance LedErrorIndicator.
Fonction utilitaire qui encapsule la crÃ©ation et l'initialisation d'un gestionnaire LED. GÃ¨re les erreurs d'initialisation et configure automatiquement le pattern normal par dÃ©faut.
ParamÃ¨tres
gpio_chip_path | Chemin vers le pÃ©riphÃ©rique GPIO.
led_pin | NumÃ©ro de pin de la LED.
Renvoie Instance de LedErrorIndicator si succÃ¨s, None sinon.
