LeoMendesEsEtml/2510_RegulationChauffage/doc/6.Graphique, Schéma/3.Doxygen/rtf/namespaceapp_1_1main.rtf

begin bodyRÃ©fÃ©rence de l'espace de nommage app.main
AAAAAAAAEVAAAAAAAAEVFonctions
start_webui_server ()
Lance le serveur web local dans un thread sÃ©parÃ©.

save_last_state (channel=None, resistance_ohm=None, temperature_c=None, temperature_sim_c=None, error=None)
Sauvegarde l'Ã©tat courant et historique par canal dans un fichier JSON.

signal_handler (sig, frame)
Gestionnaire POSIX pour les signaux (Ctrl+C).

input_monitor ()
Thread d'Ã©coute des commandes utilisateur depuis stdin.

show_error_and_continue (error_pattern, sleep_time=2)
Affiche un motif LED d'erreur pendant un temps donnÃ© puis remet l'indicateur en mode 'sequence_running'.

run_measurement_sequence (cfg, mac_address, adc, tmux)
ExÃ©cute une sÃ©quence complÃ¨te de mesures pour tous les canaux activÃ©s selon la configuration fournie.

reload_timing_config ()
Recharge les paramÃ¨tres de temporisation depuis le fichier de configuration.

main ()
Point d'entrÃ©e principal du programme.

Variables
CURRENT_DIR = os.path.dirname(os.path.abspath(__file__))
SRC_DIR = os.path.dirname(CURRENT_DIR)
bool sequencer_running = False
stop_event = threading.Event()
force_sequence = threading.Event()
led_indicator = None

AAAAAAAAEWAAAAAAAAEWDocumentation des fonctions
app.main.input_monitor ()
AAAAAAAAEXAAAAAAAAEX
Thread d'Ã©coute des commandes utilisateur depuis stdin.
Permet de forcer une sÃ©quence (touche EntrÃ©e ou 's') ou de demander l'arrÃªt ('q'). Les exceptions d'E/S sont gÃ©rÃ©es pour permettre la terminaison propre du thread.
Renvoie
None
Voici le graphe d'appel pour cette fonction :
IMAGE
app.main.main ()
AAAAAAAAEYAAAAAAAAEY
Point d'entrÃ©e principal du programme.
Parse les arguments de la ligne de commande, initialise le matÃ©riel (GPIO, ADC, MUX), le gestionnaire LED, et exÃ©cute le sÃ©quenceur en mode automatique ou manuel selon la configuration.
Renvoie
None
Voici le graphe d'appel pour cette fonction :
IMAGE
Voici le graphe des appelants de cette fonction :
IMAGE
app.main.reload_timing_config ()
AAAAAAAAEZAAAAAAAAEZ
Recharge les paramÃ¨tres de temporisation depuis le fichier de configuration.
Lit uniquement les paramÃ¨tres de temporisation pour mise Ã jour dynamique sans perturber le reste du systÃ¨me. UtilisÃ© pour permettre la modification des intervalles de sÃ©quence et du mode automatique via l'interface web.
Renvoie
Tuple (auto_sequence, sequence_interval_minutes, success) oÃ¹ success indique si le rechargement a rÃ©ussi.
Voici le graphe des appelants de cette fonction :
IMAGE
app.main.run_measurement_sequence ( cfg, mac_address, adc, tmux)
AAAAAAAAFAAAAAAAAAFA
ExÃ©cute une sÃ©quence complÃ¨te de mesures pour tous les canaux activÃ©s selon la configuration fournie.
Pour chaque canal actif : sÃ©lection du rref, configuration ADC, lecture des valeurs, conversion en tempÃ©rature, envoi API, calcul de la tempÃ©rature simulÃ©e et application via le simulateur de rÃ©sistance. Les motifs LED sont ajustÃ©s en fonction des erreurs.
ParamÃ¨tres
cfg | Dictionnaire de configuration chargÃ© depuis JSON.
mac_address | Adresse MAC ou identifiant pour les appels API.
adc | Instance de l'ADC (Ads124s08).
tmux | Instance du multiplexeur (Tmux1204).
Renvoie bool True si la sÃ©quence est globalement considÃ©rÃ©e comme rÃ©ussie, False sinon.
Voici le graphe d'appel pour cette fonction :
IMAGE
Voici le graphe des appelants de cette fonction :
IMAGE
app.main.save_last_state ( channel = None, resistance_ohm = None, temperature_c = None, temperature_sim_c = None, error = None)
AAAAAAAAFBAAAAAAAAFB
Sauvegarde l'Ã©tat courant et historique par canal dans un fichier JSON.
CrÃ©e le dossier state si nÃ©cessaire, lit le fichier last_state.json existant, met Ã jour les informations du canal fourni et Ã©crit le document au format JSON. Les erreurs internes sont capturÃ©es et affichÃ©es sur la sortie standard.
ParamÃ¨tres
channel | NumÃ©ro du canal (ou None).
resistance_ohm | RÃ©sistance mesurÃ©e (ou None).
temperature_c | TempÃ©rature mesurÃ©e [Â°C] (ou None).
temperature_sim_c | TempÃ©rature simulÃ©e [Â°C] (ou None).
error | Message d'erreur s'il y en a un (ou None).
Renvoie None
Voici le graphe des appelants de cette fonction :
IMAGE
app.main.show_error_and_continue ( error_pattern, sleep_time = 2)
AAAAAAAAFCAAAAAAAAFC
Affiche un motif LED d'erreur pendant un temps donnÃ© puis remet l'indicateur en mode 'sequence_running'.

ParamÃ¨tres
error_pattern | Nom du motif LED Ã afficher.
sleep_time | DurÃ©e d'affichage en secondes (par dÃ©faut 2s).
Renvoie None
Voici le graphe des appelants de cette fonction :
IMAGE
app.main.signal_handler ( sig, frame)
AAAAAAAAFDAAAAAAAAFD
Gestionnaire POSIX pour les signaux (Ctrl+C).
Met le drapeau sequencer_running Ã False et dÃ©clenche l'Ã©vÃ©nement stop_event pour demander un arrÃªt propre.
ParamÃ¨tres
sig | Signal reÃ§u (int).
frame | Contexte d'exÃ©cution (non utilisÃ©).
Renvoie None
Voici le graphe des appelants de cette fonction :
IMAGE
app.main.start_webui_server ()
AAAAAAAAFEAAAAAAAAFE
Lance le serveur web local dans un thread sÃ©parÃ©.
Import dynamique du module webui.webui_server et dÃ©marrage de l'application Flask/WSGI. Les exceptions sont interceptÃ©es et converties en messages sur la sortie standard pour ne pas interrompre le thread principal.
Renvoie
None

AAAAAAAAFFAAAAAAAAFFDocumentation des variables
app.main.CURRENT_DIR = os.path.dirname(os.path.abspath(__file__))
AAAAAAAAFGAAAAAAAAFGapp.main.force_sequence = threading.Event()
AAAAAAAAFHAAAAAAAAFHapp.main.led_indicator = None
AAAAAAAAFIAAAAAAAAFIbool app.main.sequencer_running = False
AAAAAAAAFJAAAAAAAAFJapp.main.SRC_DIR = os.path.dirname(CURRENT_DIR)
AAAAAAAAFKAAAAAAAAFKapp.main.stop_event = threading.Event()
AAAAAAAAFLAAAAAAAAFL
