LeoMendesEsEtml/2510_RegulationChauffage/doc/6.Graphique, Schéma/3.Doxygen/rtf/namespaceapp_1_1resistance__mapping.rtf

begin bodyRÃ©fÃ©rence de l'espace de nommage app.resistance_mapping
AAAAAAAAHBAAAAAAAAHBFonctions
dict get_channel_mux_map (str sensor_type)
Retourne le mapping CHANNEL_MUX pour un type de sonde donnÃ©.

tuple find_closest_channel (float target_resistance, str sensor_type)
Trouve le canal MUX le plus proche pour une rÃ©sistance cible.

Variables
dict CHANNEL_MUX

AAAAAAAAHCAAAAAAAAHCDocumentation des fonctions
tuple app.resistance_mapping.find_closest_channel (float target_resistance, str sensor_type)
AAAAAAAAHDAAAAAAAAHD
Trouve le canal MUX le plus proche pour une rÃ©sistance cible.
Algorithme de recherche du canal TMUX offrant la rÃ©sistance la plus proche de la valeur cible. Calcule l'erreur absolue et relative pour le meilleur canal trouvÃ©.
ParamÃ¨tres
target_resistance | Valeur de rÃ©sistance cible recherchÃ©e [Ohms].
sensor_type | Type de sonde Ã utiliser pour la recherche.
Renvoie Tuple (canal, resistance_reelle, erreur_pourcent). Retourne (None, None, None) si aucun canal trouvÃ©.
Exceptions
KeyError | si le type de sonde n'existe pas.
Voici le graphe d'appel pour cette fonction :
IMAGE
dict app.resistance_mapping.get_channel_mux_map (str sensor_type)
AAAAAAAAHEAAAAAAAAHE
Retourne le mapping CHANNEL_MUX pour un type de sonde donnÃ©.
Fonction d'accÃ¨s qui extrait le dictionnaire de correspondance canal/rÃ©sistance pour un type de sonde spÃ©cifique. Valide l'existence du type avant de retourner les donnÃ©es.
ParamÃ¨tres
sensor_type | Type de sonde demandÃ© (doit exister dans CHANNEL_MUX).
Renvoie Dictionnaire {canal: resistance} pour le type de sonde.
Exceptions
KeyError | si le type de sonde n'est pas supportÃ©.
Voici le graphe des appelants de cette fonction :
IMAGE

AAAAAAAAHFAAAAAAAAHFDocumentation des variables
dict app.resistance_mapping.CHANNEL_MUX
AAAAAAAAHGAAAAAAAAHG
