LeoMendesEsEtml/2510_RegulationChauffage/doc/6.Graphique, Schéma/3.Doxygen/rtf/namespaceapp_1_1resistance__simulation.rtf

begin bodyRÃ©fÃ©rence de l'espace de nommage app.resistance_simulation
AAAAAAAAHHAAAAAAAAHHClasses
class ResistanceSimulationErrorException pour les erreurs de simulation de rÃ©sistance.
class ResistanceSimulatorContrÃ´leur pour la simulation de rÃ©sistance via MUX.
Fonctions
bool apply_resistance_simulation (float resistance_ohm)
Fonction utilitaire pour appliquer une rÃ©sistance simulÃ©e.

Variables
sim = ResistanceSimulator()
bool success = sim.apply_resistance_simulation(1000.0)
valid = sim.validate_resistance_applied(667.0, tolerance=0.15)

AAAAAAAAHIAAAAAAAAHIDocumentation des fonctions
bool app.resistance_simulation.apply_resistance_simulation (float resistance_ohm)
AAAAAAAAHJAAAAAAAAHJ
Fonction utilitaire pour appliquer une rÃ©sistance simulÃ©e.
Fonction de commoditÃ© qui encapsule la crÃ©ation d'un simulateur, l'application d'une rÃ©sistance et le nettoyage automatique. Utilise le pattern RAII pour la gestion des ressources.
ParamÃ¨tres
resistance_ohm | RÃ©sistance Ã appliquer [Ohms].
Renvoie True si l'application a rÃ©ussi, False sinon.

AAAAAAAAHKAAAAAAAAHKDocumentation des variables
app.resistance_simulation.sim = ResistanceSimulator()
AAAAAAAAHLAAAAAAAAHLbool app.resistance_simulation.success = sim.apply_resistance_simulation(1000.0)
AAAAAAAAHMAAAAAAAAHMapp.resistance_simulation.valid = sim.validate_resistance_applied(667.0, tolerance=0.15)
AAAAAAAAHNAAAAAAAAHN
