LeoMendesEsEtml/2510_RegulationChauffage/doc/6.Graphique, Schéma/3.Doxygen/rtf/namespaceapp_1_1sensor__profiles.rtf

begin bodyRÃ©fÃ©rence de l'espace de nommage app.sensor_profiles
AAAAAAAAIEAAAAAAAAIEFonctions
get_profile (sensor_name)
RÃ©cupÃ¨re le profil de configuration ADC pour un capteur donnÃ©.

Variables
dict SENSOR_PROFILES

AAAAAAAAIFAAAAAAAAIFDocumentation des fonctions
app.sensor_profiles.get_profile ( sensor_name)
AAAAAAAAIGAAAAAAAAIG
RÃ©cupÃ¨re le profil de configuration ADC pour un capteur donnÃ©.
Fonction d'accÃ¨s qui retourne le dictionnaire de configuration contenant les paramÃ¨tres optimisÃ©s (Rref, IDAC, PGA) pour un type de capteur spÃ©cifique.
ParamÃ¨tres
sensor_name | Nom du type de capteur recherchÃ©.
Renvoie Dictionnaire contenant les paramÃ¨tres de configuration:
▪ ref_ohm: rÃ©sistance de rÃ©fÃ©rence [Ohms]
▪ dac_uA: courant d'excitation [microampÃ¨res]
▪ ga_gain: gain programmable [1-128]
Exceptions
KeyError | si le type de capteur n'est pas reconnu.

AAAAAAAAIHAAAAAAAAIHDocumentation des variables
dict app.sensor_profiles.SENSOR_PROFILES
AAAAAAAAIIAAAAAAAAII
