LeoMendesEsEtml/2510_RegulationChauffage/doc/6.Graphique, Schéma/3.Doxygen/rtf/namespaceapp_1_1temperature__conversion.rtf

begin bodyRÃ©fÃ©rence de l'espace de nommage app.temperature_conversion
AAAAAAAAIJAAAAAAAAIJFonctions
resistance_to_temperature (resistance, table)
Convertit une rÃ©sistance mesurÃ©e en tempÃ©rature via interpolation linÃ©aire.

resistance_to_temperature_dynamic (resistance, sensor)
Convertit une rÃ©sistance mesurÃ©e en tempÃ©rature pour un capteur donnÃ©.

temperature_to_resistance_dynamic (temperature, sensor)
Convertit une tempÃ©rature en rÃ©sistance pour un capteur donnÃ© (conversion inverse).

convert_temperature_to_resistance (temperature, probe_type)
Fonction de conversion principale pour la simulation de rÃ©sistance.

get_supported_probe_types ()
Retourne la liste des types de sondes supportÃ©s.

validate_temperature_range (temperature, probe_type)
Valide si une tempÃ©rature est dans la plage supportÃ©e par une sonde.

AAAAAAAAIKAAAAAAAAIKDocumentation des fonctions
app.temperature_conversion.convert_temperature_to_resistance ( temperature, probe_type)
AAAAAAAAILAAAAAAAAIL
Fonction de conversion principale pour la simulation de rÃ©sistance.
Fonction de haut niveau qui supporte diffÃ©rents types de sondes avec leurs caractÃ©ristiques spÃ©cifiques. Inclut la normalisation des noms de sondes et la gestion des variantes de nomenclature.
ParamÃ¨tres
temperature | TempÃ©rature simulÃ©e [Â°C].
probe_type | Type de sonde (formats multiples supportÃ©s).
Renvoie RÃ©sistance simulÃ©e [Ohms] ou None si Ã©chec.
Voici le graphe d'appel pour cette fonction :
IMAGE
app.temperature_conversion.get_supported_probe_types ()
AAAAAAAAIMAAAAAAAAIM
Retourne la liste des types de sondes supportÃ©s.
Fonction utilitaire qui extrait la liste complÃ¨te des noms de capteurs disponibles dans les tables de conversion.
Renvoie
Liste des noms de capteurs disponibles pour conversion.
app.temperature_conversion.resistance_to_temperature ( resistance, table)
AAAAAAAAINAAAAAAAAIN
Convertit une rÃ©sistance mesurÃ©e en tempÃ©rature via interpolation linÃ©aire.
Algorithme d'interpolation linÃ©aire qui recherche l'intervalle contenant la rÃ©sistance mesurÃ©e et calcule la tempÃ©rature correspondante. GÃ¨re les cas limites hors plage de mesure.
ParamÃ¨tres
resistance | RÃ©sistance mesurÃ©e [Ohms].
table | Liste de tuples (rÃ©sistance, tempÃ©rature) pour interpolation.
Renvoie TempÃ©rature interpolÃ©e [Â°C], ou valeurs limites si hors plage.
app.temperature_conversion.resistance_to_temperature_dynamic ( resistance, sensor)
AAAAAAAAIOAAAAAAAAIO
Convertit une rÃ©sistance mesurÃ©e en tempÃ©rature pour un capteur donnÃ©.
Fonction dynamique qui sÃ©lectionne automatiquement la table de conversion appropriÃ©e selon le type de capteur spÃ©cifiÃ©. Effectue la validation du capteur avant conversion.
ParamÃ¨tres
resistance | RÃ©sistance mesurÃ©e [Ohms].
sensor | Nom du type de capteur Ã utiliser.
Renvoie TempÃ©rature interpolÃ©e [Â°C] ou None si hors limites.
Exceptions
ValueError | si le capteur n'est pas reconnu.
app.temperature_conversion.temperature_to_resistance_dynamic ( temperature, sensor)
AAAAAAAAIPAAAAAAAAIP
Convertit une tempÃ©rature en rÃ©sistance pour un capteur donnÃ© (conversion inverse).
Fonction de conversion inverse utilisÃ©e pour la simulation de rÃ©sistance. Effectue l'interpolation linÃ©aire sur l'axe tempÃ©rature pour obtenir la rÃ©sistance correspondante selon le type de capteur.
ParamÃ¨tres
temperature | TempÃ©rature d'entrÃ©e [Â°C].
sensor | Nom du type de capteur Ã utiliser.
Renvoie RÃ©sistance interpolÃ©e [Ohms] ou None si hors limites.
Exceptions
ValueError | si le capteur n'est pas reconnu.
Voici le graphe des appelants de cette fonction :
IMAGE
app.temperature_conversion.validate_temperature_range ( temperature, probe_type)
AAAAAAAAIQAAAAAAAAIQ
Valide si une tempÃ©rature est dans la plage supportÃ©e par une sonde.
Fonction de validation qui vÃ©rifie si une tempÃ©rature donnÃ©e est compatible avec la plage de fonctionnement d'un type de capteur spÃ©cifique selon sa table de calibration.
ParamÃ¨tres
temperature | TempÃ©rature Ã valider [Â°C].
probe_type | Type de sonde Ã vÃ©rifier.
Renvoie True si la tempÃ©rature est dans la plage supportÃ©e.
