LeoMendesEsEtml/2510_RegulationChauffage/doc/6.Graphique, Schéma/3.Doxygen/rtf/namespaceconfig__module_1_1cm5__config.rtf

begin bodyRÃ©fÃ©rence de l'espace de nommage config_module.cm5_config
AAAAAAAAJSAAAAAAAAJSFonctions
build_hw ()
Initialise et configure tout le matÃ©riel CM5.

Variables
list ADC_CHANNELS = [1, 2, 3, 4]

AAAAAAAAJTAAAAAAAAJTDocumentation des fonctions
config_module.cm5_config.build_hw ()
AAAAAAAAJUAAAAAAAAJU
Initialise et configure tout le matÃ©riel CM5.
CrÃ©e les instances des composants matÃ©riels avec configuration fixe LED frontale, multiplexeur TMUX et ADC. Configure la LED en sortie et l'allume immÃ©diatement pour indication systÃ¨me.
Renvoie
Dictionnaire contenant toutes les instances matÃ©rielles:
▪ led": Instance GPIO pour LED frontale
▪ tmux": Instance Tmux1204 pour sÃ©lection canaux
▪ adc": Instance Ads124s08 pour conversion analogique
Avertissement
LED allumÃ©e automatiquement pour indiquer systÃ¨me actif.

AAAAAAAAJVAAAAAAAAJVDocumentation des variables
list config_module.cm5_config.ADC_CHANNELS = [1, 2, 3, 4]
AAAAAAAAJWAAAAAAAAJW
