LeoMendesEsEtml/2510_RegulationChauffage/doc/6.Graphique, Schéma/3.Doxygen/rtf/namespaces.rtf

begin bodyListe des espaces de nommage
Liste de tous les espaces de nommage avec une brÃ¨ve description:
app pagenum
app.adc_ads124s08 pagenum
app.api_client pagenum
app.config_loader pagenum
app.front_led_management pagenum
app.hw_mux_adg731 pagenum
app.hw_tmux1204 pagenum
app.main pagenum
app.mesure_24v_dry_contact pagenum
app.pins_cm5 pagenum
app.resistance_mapping pagenum
app.resistance_simulation pagenum
app.sensor_profiles pagenum
app.temperature_conversion pagenum
app.temperature_simulation pagenum
app.test_lm70_compatible pagenum
app.test_spi_adc pagenum
config_module pagenum
config_module.cm5_config pagenum
webui pagenum
webui.webui_server pagenum
