LeoMendesEsEtml/2510_RegulationChauffage/doc/6.Graphique, Schéma/3.Doxygen/rtf/pins__cm5_8py.rtf

begin bodyRÃ©fÃ©rence du fichier C:/Users/thebi/Documents/2510_RegulationChauffage/doc/9.SoftWare/Doxygen/src/app/pins_cm5.py
AAAAAAAAAMAAAAAAAAAM
Mapping GPIO et SPI fixÃ©s pour la plateforme CM5.
Espaces de nommage
namespace app
namespace app.pins_cm5
Variables
str app.pins_cm5.GPIO_CHIP_PATH = "/dev/gpiochip0"
int app.pins_cm5.MUX_CS_4 = 2
int app.pins_cm5.MUX_CS_3 = 3
int app.pins_cm5.MUX_CS_2 = 7
int app.pins_cm5.MUX_CS_1 = 8
int app.pins_cm5.MUX_MOSI_DUMMY = 10
int app.pins_cm5.MUX_SCLK_DUMMY = 11
int app.pins_cm5.CM_24V_OUT_1 = 13
int app.pins_cm5.CM_24V_SENSE_1 = 14
int app.pins_cm5.CM_24V_OUT_2 = 15
int app.pins_cm5.CM_24V_SENSE_2 = 16
int app.pins_cm5.CMD_RELAY = 17
int app.pins_cm5.CS_ADC_DUMMY = 18
int app.pins_cm5.SPI_MISO_ADC_DMY = 19
int app.pins_cm5.SPI_MOSI_ADC_DMY = 20
int app.pins_cm5.SPI_SCLK_ADC_DMY = 21
int app.pins_cm5.ADC_DRDY = 22
int app.pins_cm5.ADC_START_SYNC = 23
int app.pins_cm5.ADC_A0 = 24
int app.pins_cm5.ADC_A1 = 25
int app.pins_cm5.FRONT_LED = 27
int app.pins_cm5.SPI0_BUS = 0
int app.pins_cm5.SPI1_BUS = 1
int app.pins_cm5.SPI0_DEV0 = 0
int app.pins_cm5.SPI0_DEV1 = 1
int app.pins_cm5.SPI1_DEV0 = 0
int app.pins_cm5.SPI_MUX_SPEED_HZ = 100000
int app.pins_cm5.SPI_ADC_SPEED_HZ = 100000

Description dÃ©taillÃ©e
Mapping GPIO et SPI fixÃ©s pour la plateforme CM5.
Ce module dÃ©finit tous les assignements de broches GPIO et les paramÃ¨tres SPI fixes pour la carte CM5. Ces constantes ne doivent pas Ãªtre modifiÃ©es via la configuration utilisateur car elles correspondent au routage matÃ©riel de la carte.
Auteur
LÃ©o Mendes @project 2510_RegulationsChauffage @Mandant Oblo_solution
Date
2025-09-18
Version
1.0.0
Copyright
Copyright (c) 2025
