LeoMendesEsEtml/2510_RegulationChauffage/doc/6.Graphique, Schéma/3.Doxygen/rtf/refman.rtf

2510_RegulationChauffage

AUTHOR
Version

Table des matières

Table of contents

Index des espaces de nommage
Liste des espaces de nommage
Liste de tous les espaces de nommage avec une brève description:
app pagenum
app.adc_ads124s08 pagenum
app.api_client pagenum
app.config_loader pagenum
app.front_led_management pagenum
app.hw_mux_adg731 pagenum
app.hw_tmux1204 pagenum
app.main pagenum
app.mesure_24v_dry_contact pagenum
app.pins_cm5 pagenum
app.resistance_mapping pagenum
app.resistance_simulation pagenum
app.sensor_profiles pagenum
app.temperature_conversion pagenum
app.temperature_simulation pagenum
app.test_lm70_compatible pagenum
app.test_spi_adc pagenum
config_module pagenum
config_module.cm5_config pagenum
webui pagenum
webui.webui_server pagenum

Index hiérarchique
Hiérarchie des classes
Cette liste d'héritage est classée approximativement par ordre alphabétique :
app.hw_mux_adg731.Adg731MuxSpi pagenum
app.adc_ads124s08.Ads124s08 pagenum
app.api_client.ApiClient pagenum
Exception
app.api_client.ApiError pagenum
app.resistance_simulation.ResistanceSimulationError pagenum

app.front_led_management.LedErrorIndicator pagenum
app.resistance_simulation.ResistanceSimulator pagenum
app.hw_tmux1204.Tmux1204 pagenum

Index des classes
Liste des classes
Liste des classes, structures, unions et interfaces avec une brève description :
app.hw_mux_adg731.Adg731MuxSpi (Pilote SPI pour multiplexeurs ADG731 ) pagenum
app.adc_ads124s08.Ads124s08 (Driver pour l'ADC ADS124S08 avec interface SPI ) pagenum
app.api_client.ApiClient (Client pour interroger les APIs oblosolutions.ch ) pagenum
app.api_client.ApiError (Exception pour les erreurs d'API ) pagenum
app.front_led_management.LedErrorIndicator (Gestionnaire de LED avec patterns d'erreur ) pagenum
app.resistance_simulation.ResistanceSimulationError (Exception pour les erreurs de simulation de résistance ) pagenum
app.resistance_simulation.ResistanceSimulator (Contrôleur pour la simulation de résistance via MUX ) pagenum
app.hw_tmux1204.Tmux1204 (Pilote pour le multiplexeur TMUX1204 ) pagenum

Index des fichiers
Liste des fichiers
Liste de tous les fichiers avec une brève description :
C:/Users/thebi/Documents/2510_RegulationChauffage/doc/9.SoftWare/Doxygen/src/app/__init__.py pagenum
C:/Users/thebi/Documents/2510_RegulationChauffage/doc/9.SoftWare/Doxygen/src/app/adc_ads124s08.py (Driver pour l'ADC ADS124S08 avec communication SPI ) pagenum
C:/Users/thebi/Documents/2510_RegulationChauffage/doc/9.SoftWare/Doxygen/src/app/api_client.py (Client API pour les services oblosolutions.ch ) pagenum
C:/Users/thebi/Documents/2510_RegulationChauffage/doc/9.SoftWare/Doxygen/src/app/config_loader.py (Chargeur de configuration JSON pour le système de mesure ) pagenum
C:/Users/thebi/Documents/2510_RegulationChauffage/doc/9.SoftWare/Doxygen/src/app/front_led_management.py (Gestionnaire de LED frontale avec patterns d'erreur ) pagenum
C:/Users/thebi/Documents/2510_RegulationChauffage/doc/9.SoftWare/Doxygen/src/app/hw_mux_adg731.py (Pilote pour multiplexeur ADG731 via interface SPI ) pagenum
C:/Users/thebi/Documents/2510_RegulationChauffage/doc/9.SoftWare/Doxygen/src/app/hw_tmux1204.py (Pilote pour multiplexeur TMUX1204 de sélection de résistance de référence ) pagenum
C:/Users/thebi/Documents/2510_RegulationChauffage/doc/9.SoftWare/Doxygen/src/app/main.py (Système de mesure et simulation de température ) pagenum
C:/Users/thebi/Documents/2510_RegulationChauffage/doc/9.SoftWare/Doxygen/src/app/mesure_24v_dry_contact.py (Module de test des entrées/sorties 24V pour contacts secs ) pagenum
C:/Users/thebi/Documents/2510_RegulationChauffage/doc/9.SoftWare/Doxygen/src/app/pins_cm5.py (Mapping GPIO et SPI fixés pour la plateforme CM5 ) pagenum
C:/Users/thebi/Documents/2510_RegulationChauffage/doc/9.SoftWare/Doxygen/src/app/resistance_mapping.py (Mapping des résistances TMUX par type de sonde de température ) pagenum
C:/Users/thebi/Documents/2510_RegulationChauffage/doc/9.SoftWare/Doxygen/src/app/resistance_simulation.py (Module pour commander le MUX de simulation de résistance ) pagenum
C:/Users/thebi/Documents/2510_RegulationChauffage/doc/9.SoftWare/Doxygen/src/app/sensor_profiles.py (Profils capteurs extraits de 'Calcul ADC.xlsx' (Feuil1) ) pagenum
C:/Users/thebi/Documents/2510_RegulationChauffage/doc/9.SoftWare/Doxygen/src/app/temperature_conversion.py (Module de conversion résistance/température via interpolation linéaire ) pagenum
C:/Users/thebi/Documents/2510_RegulationChauffage/doc/9.SoftWare/Doxygen/src/app/temperature_simulation.py (Module de calcul de température simulée selon formule prédictive ) pagenum
C:/Users/thebi/Documents/2510_RegulationChauffage/doc/9.SoftWare/Doxygen/src/app/test_lm70_compatible.py pagenum
C:/Users/thebi/Documents/2510_RegulationChauffage/doc/9.SoftWare/Doxygen/src/app/test_spi_adc.py pagenum
C:/Users/thebi/Documents/2510_RegulationChauffage/doc/9.SoftWare/Doxygen/src/config_module/__init__.py pagenum
C:/Users/thebi/Documents/2510_RegulationChauffage/doc/9.SoftWare/Doxygen/src/config_module/cm5_config.py (Configuration matérielle pour plateforme CM5 ) pagenum
C:/Users/thebi/Documents/2510_RegulationChauffage/doc/9.SoftWare/Doxygen/src/webui/__init__.py pagenum
C:/Users/thebi/Documents/2510_RegulationChauffage/doc/9.SoftWare/Doxygen/src/webui/webui_server.py (Serveur web pour interface utilisateur de configuration ) pagenum

Documentation des espaces de nommage
Référence de l'espace de nommage app
AAAAAAAAAWAAAAAAAAAWEspaces de nommage
namespace adc_ads124s08
namespace api_client
namespace config_loader
namespace front_led_management
namespace hw_mux_adg731
namespace hw_tmux1204
namespace main
namespace mesure_24v_dry_contact
namespace pins_cm5
namespace resistance_mapping
namespace resistance_simulation
namespace sensor_profiles
namespace temperature_conversion
namespace temperature_simulation
namespace test_lm70_compatible
namespace test_spi_adc

Référence de l'espace de nommage app.adc_ads124s08
AAAAAAAAAXAAAAAAAAAXClasses
class Ads124s08Driver pour l'ADC ADS124S08 avec interface SPI.
Fonctions
encode_gain (pga_gain)
Encode le gain PGA en code binaire pour le registre.

encode_idac_uA (idac_uA)
Encode la magnitude IDAC en code binaire pour le registre.

sign_extend_24 (b0, b1, b2)
Étend le signe d'un code ADC 24 bits vers 32 bits.

Variables
int REG_ID = 0x00
int REG_STATUS = 0x01
int REG_INPMUX = 0x02
int REG_PGA = 0x03
int REG_DATARATE = 0x04
int REG_REF = 0x05
int REG_IDACMUX = 0x07
int REG_SYS = 0x09
int REG_IDACMAG = 0x06
int CMD_RESET = 0x06
int CMD_START = 0x08
int CMD_STOP = 0x0A
int CMD_RDATA = 0x12
tuple FS = (1 << 23) - 1
dict CHANNELS

AAAAAAAAAYAAAAAAAAAYDocumentation des fonctions
app.adc_ads124s08.encode_gain ( pga_gain)
AAAAAAAAAZAAAAAAAAAZ
Encode le gain PGA en code binaire pour le registre.
Convertit une valeur de gain décimale en code binaire 3 bits pour la configuration du registre PGA de l'ADS124S08.
Paramètres
pga_gain | Valeur du gain PGA (1, 2, 4, 8, 16, 32, 64, 128).
Renvoie Code binaire 3 bits correspondant au gain.
Exceptions
ValueError | si le gain fourni n'est pas supporté.
Voir également configure_channel
Voici le graphe des appelants de cette fonction :
IMAGE
app.adc_ads124s08.encode_idac_uA ( idac_uA)
AAAAAAAABAAAAAAAAABA
Encode la magnitude IDAC en code binaire pour le registre.
Convertit une valeur de courant IDAC en microampères en code binaire 4 bits pour la configuration du registre IDACMAG.
Paramètres
idac_uA | Courant IDAC en microampères (10, 50, 100, 250, 500, 1000, 1500, 2000).
Renvoie Code binaire 4 bits correspondant au courant.
Exceptions
ValueError | si le courant fourni n'est pas supporté.
Voir également configure_channel
Voici le graphe des appelants de cette fonction :
IMAGE
app.adc_ads124s08.sign_extend_24 ( b0, b1, b2)
AAAAAAAABBAAAAAAAABB
Étend le signe d'un code ADC 24 bits vers 32 bits.
Convertit un code ADC 24 bits signé en entier Python 32 bits en préservant le signe selon la représentation en complément à 2.
Paramètres
b0 | Octet de poids fort (MSB) du code 24 bits.
b1 | Octet du milieu du code 24 bits.
b2 | Octet de poids faible (LSB) du code 24 bits.
Renvoie Valeur entière signée 32 bits correspondante.
Note
Nécessaire car Python gère automatiquement les entiers de taille variable.
Voir également
read_code24
Voici le graphe des appelants de cette fonction :
IMAGE

AAAAAAAABCAAAAAAAABCDocumentation des variables
dict app.adc_ads124s08.CHANNELS
AAAAAAAABDAAAAAAAABDValeur initiale :
1 = {
2 # Canal 1: entrée positive AIN1, négative AIN2
3 1: {"ainp_idx": 1, "ainn_idx": 2},
4 # Canal 2: entrée positive AIN4, négative AIN5
5 2: {"ainp_idx": 4, "ainn_idx": 5},
6 # Canal 3: entrée positive AIN7, négative AIN8
7 3: {"ainp_idx": 7, "ainn_idx": 8},
8 # Canal 4: entrée positive AIN10, négative AIN11
9 4: {"ainp_idx": 10, "ainn_idx": 11}
10 }
int app.adc_ads124s08.CMD_RDATA = 0x12
AAAAAAAABEAAAAAAAABEint app.adc_ads124s08.CMD_RESET = 0x06
AAAAAAAABFAAAAAAAABFint app.adc_ads124s08.CMD_START = 0x08
AAAAAAAABGAAAAAAAABGint app.adc_ads124s08.CMD_STOP = 0x0A
AAAAAAAABHAAAAAAAABHtuple app.adc_ads124s08.FS = (1 << 23) - 1
AAAAAAAABIAAAAAAAABIint app.adc_ads124s08.REG_DATARATE = 0x04
AAAAAAAABJAAAAAAAABJint app.adc_ads124s08.REG_ID = 0x00
AAAAAAAABKAAAAAAAABKint app.adc_ads124s08.REG_IDACMAG = 0x06
AAAAAAAABLAAAAAAAABLint app.adc_ads124s08.REG_IDACMUX = 0x07
AAAAAAAABMAAAAAAAABMint app.adc_ads124s08.REG_INPMUX = 0x02
AAAAAAAABNAAAAAAAABNint app.adc_ads124s08.REG_PGA = 0x03
AAAAAAAABOAAAAAAAABOint app.adc_ads124s08.REG_REF = 0x05
AAAAAAAABPAAAAAAAABPint app.adc_ads124s08.REG_STATUS = 0x01
AAAAAAAABQAAAAAAAABQint app.adc_ads124s08.REG_SYS = 0x09
AAAAAAAABRAAAAAAAABR

Référence de l'espace de nommage app.api_client
AAAAAAAACQAAAAAAAACQClasses
class ApiClientClient pour interroger les APIs oblosolutions.ch.
class ApiErrorException pour les erreurs d'API.
Fonctions
Dict[str, Any] get_simulation_data (str mac_address)
Récupère les données de simulation depuis les APIs.

bool send_temperature_measurement (str mac_address, float temperature, int channel=None)
Envoie une mesure de température vers l'API.

Variables
int REQUEST_TIMEOUT = 10
int MAX_RETRIES = 3
int RETRY_DELAY = 1
str test_mac = "0030DEABCDEF"
Dict[str, Any] data = get_simulation_data(test_mac)

AAAAAAAACRAAAAAAAACRDocumentation des fonctions
Dict[str, Any] app.api_client.get_simulation_data (str mac_address)
AAAAAAAACSAAAAAAAACS
Récupère les données de simulation depuis les APIs.
Combine les appels vers td25_param et td25_forecast pour récupérer tous les paramètres nécessaires à la simulation de température. Utilise le client ApiClient pour gérer les retries et les erreurs automatiquement.
Paramètres
mac_address | Adresse MAC du dispositif.
Renvoie Dictionnaire avec toutes les données nécessaires pour la simulation.
Exceptions
ApiError | Si aucune donnée valide n'est obtenue.
bool app.api_client.send_temperature_measurement (str mac_address, float temperature, int channel = None)
AAAAAAAACTAAAAAAAACT
Envoie une mesure de température vers l'API.
Fonction utilitaire qui crée un client ApiClient et utilise la méthode post_measured_temperature pour envoyer la température mesurée. Gère les exceptions et retourne un booléen simple.
Paramètres
mac_address | Adresse MAC du dispositif.
temperature | Température mesurée en °C.
channel | Canal de mesure (optionnel).
Renvoie True si succès, False sinon.

AAAAAAAACUAAAAAAAACUDocumentation des variables
Dict[str, Any] app.api_client.data = get_simulation_data(test_mac)
AAAAAAAACVAAAAAAAACVint app.api_client.MAX_RETRIES = 3
AAAAAAAACWAAAAAAAACWint app.api_client.REQUEST_TIMEOUT = 10
AAAAAAAACXAAAAAAAACXint app.api_client.RETRY_DELAY = 1
AAAAAAAACYAAAAAAAACYstr app.api_client.test_mac = "0030DEABCDEF"
AAAAAAAACZAAAAAAAACZ

Référence de l'espace de nommage app.config_loader
AAAAAAAADMAAAAAAAADMFonctions
load_config (path)

AAAAAAAADNAAAAAAAADNDocumentation des fonctions
app.config_loader.load_config ( path)
AAAAAAAADOAAAAAAAADO

Référence de l'espace de nommage app.front_led_management
AAAAAAAADPAAAAAAAADPClasses
class LedErrorIndicatorGestionnaire de LED avec patterns d'erreur.
Fonctions
create_led_indicator (gpio_chip_path, led_pin)
Factory function pour créer une instance LedErrorIndicator.

AAAAAAAADQAAAAAAAADQDocumentation des fonctions
app.front_led_management.create_led_indicator ( gpio_chip_path, led_pin)
AAAAAAAADRAAAAAAAADR
Factory function pour créer une instance LedErrorIndicator.
Fonction utilitaire qui encapsule la création et l'initialisation d'un gestionnaire LED. Gère les erreurs d'initialisation et configure automatiquement le pattern normal par défaut.
Paramètres
gpio_chip_path | Chemin vers le périphérique GPIO.
led_pin | Numéro de pin de la LED.
Renvoie Instance de LedErrorIndicator si succès, None sinon.

Référence de l'espace de nommage app.hw_mux_adg731
AAAAAAAADWAAAAAAAADWClasses
class Adg731MuxSpiPilote SPI pour multiplexeurs ADG731.
Fonctions
adg731_ctrl_byte (address, enable=True)
Génère le byte de contrôle pour l'ADG731.

AAAAAAAADXAAAAAAAADXDocumentation des fonctions
app.hw_mux_adg731.adg731_ctrl_byte ( address, enable = True)
AAAAAAAADYAAAAAAAADY
Génère le byte de contrôle pour l'ADG731.
Construit l'octet de commande selon le protocole ADG731 avec le bit d'activation (EN) en MSB et l'adresse sur 5 bits. L'activation se fait avec EN=0 (logique inversée).
Paramètres
address | Adresse du canal (0-31).
enable | État d'activation du canal (True=activé).
Renvoie Octet de contrôle formaté selon le protocole ADG731.
Exceptions
ValueError | Si l'adresse est hors de la plage valide.
Voici le graphe des appelants de cette fonction :
IMAGE

Référence de l'espace de nommage app.hw_tmux1204
AAAAAAAAEKAAAAAAAAEKClasses
class Tmux1204Pilote pour le multiplexeur TMUX1204.

Référence de l'espace de nommage app.main
AAAAAAAAEVAAAAAAAAEVFonctions
start_webui_server ()
Lance le serveur web local dans un thread séparé.

save_last_state (channel=None, resistance_ohm=None, temperature_c=None, temperature_sim_c=None, error=None)
Sauvegarde l'état courant et historique par canal dans un fichier JSON.

signal_handler (sig, frame)
Gestionnaire POSIX pour les signaux (Ctrl+C).

input_monitor ()
Thread d'écoute des commandes utilisateur depuis stdin.

show_error_and_continue (error_pattern, sleep_time=2)
Affiche un motif LED d'erreur pendant un temps donné puis remet l'indicateur en mode 'sequence_running'.

run_measurement_sequence (cfg, mac_address, adc, tmux)
Exécute une séquence complète de mesures pour tous les canaux activés selon la configuration fournie.

reload_timing_config ()
Recharge les paramètres de temporisation depuis le fichier de configuration.

main ()
Point d'entrée principal du programme.

Variables
CURRENT_DIR = os.path.dirname(os.path.abspath(__file__))
SRC_DIR = os.path.dirname(CURRENT_DIR)
bool sequencer_running = False
stop_event = threading.Event()
force_sequence = threading.Event()
led_indicator = None

AAAAAAAAEWAAAAAAAAEWDocumentation des fonctions
app.main.input_monitor ()
AAAAAAAAEXAAAAAAAAEX
Thread d'écoute des commandes utilisateur depuis stdin.
Permet de forcer une séquence (touche Entrée ou 's') ou de demander l'arrêt ('q'). Les exceptions d'E/S sont gérées pour permettre la terminaison propre du thread.
Renvoie
None
Voici le graphe d'appel pour cette fonction :
IMAGE
app.main.main ()
AAAAAAAAEYAAAAAAAAEY
Point d'entrée principal du programme.
Parse les arguments de la ligne de commande, initialise le matériel (GPIO, ADC, MUX), le gestionnaire LED, et exécute le séquenceur en mode automatique ou manuel selon la configuration.
Renvoie
None
Voici le graphe d'appel pour cette fonction :
IMAGE
Voici le graphe des appelants de cette fonction :
IMAGE
app.main.reload_timing_config ()
AAAAAAAAEZAAAAAAAAEZ
Recharge les paramètres de temporisation depuis le fichier de configuration.
Lit uniquement les paramètres de temporisation pour mise à jour dynamique sans perturber le reste du système. Utilisé pour permettre la modification des intervalles de séquence et du mode automatique via l'interface web.
Renvoie
Tuple (auto_sequence, sequence_interval_minutes, success) où success indique si le rechargement a réussi.
Voici le graphe des appelants de cette fonction :
IMAGE
app.main.run_measurement_sequence ( cfg, mac_address, adc, tmux)
AAAAAAAAFAAAAAAAAAFA
Exécute une séquence complète de mesures pour tous les canaux activés selon la configuration fournie.
Pour chaque canal actif : sélection du rref, configuration ADC, lecture des valeurs, conversion en température, envoi API, calcul de la température simulée et application via le simulateur de résistance. Les motifs LED sont ajustés en fonction des erreurs.
Paramètres
cfg | Dictionnaire de configuration chargé depuis JSON.
mac_address | Adresse MAC ou identifiant pour les appels API.
adc | Instance de l'ADC (Ads124s08).
tmux | Instance du multiplexeur (Tmux1204).
Renvoie bool True si la séquence est globalement considérée comme réussie, False sinon.
Voici le graphe d'appel pour cette fonction :
IMAGE
Voici le graphe des appelants de cette fonction :
IMAGE
app.main.save_last_state ( channel = None, resistance_ohm = None, temperature_c = None, temperature_sim_c = None, error = None)
AAAAAAAAFBAAAAAAAAFB
Sauvegarde l'état courant et historique par canal dans un fichier JSON.
Crée le dossier state si nécessaire, lit le fichier last_state.json existant, met à jour les informations du canal fourni et écrit le document au format JSON. Les erreurs internes sont capturées et affichées sur la sortie standard.
Paramètres
channel | Numéro du canal (ou None).
resistance_ohm | Résistance mesurée (ou None).
temperature_c | Température mesurée [°C] (ou None).
temperature_sim_c | Température simulée [°C] (ou None).
error | Message d'erreur s'il y en a un (ou None).
Renvoie None
Voici le graphe des appelants de cette fonction :
IMAGE
app.main.show_error_and_continue ( error_pattern, sleep_time = 2)
AAAAAAAAFCAAAAAAAAFC
Affiche un motif LED d'erreur pendant un temps donné puis remet l'indicateur en mode 'sequence_running'.

Paramètres
error_pattern | Nom du motif LED à afficher.
sleep_time | Durée d'affichage en secondes (par défaut 2s).
Renvoie None
Voici le graphe des appelants de cette fonction :
IMAGE
app.main.signal_handler ( sig, frame)
AAAAAAAAFDAAAAAAAAFD
Gestionnaire POSIX pour les signaux (Ctrl+C).
Met le drapeau sequencer_running à False et déclenche l'événement stop_event pour demander un arrêt propre.
Paramètres
sig | Signal reçu (int).
frame | Contexte d'exécution (non utilisé).
Renvoie None
Voici le graphe des appelants de cette fonction :
IMAGE
app.main.start_webui_server ()
AAAAAAAAFEAAAAAAAAFE
Lance le serveur web local dans un thread séparé.
Import dynamique du module webui.webui_server et démarrage de l'application Flask/WSGI. Les exceptions sont interceptées et converties en messages sur la sortie standard pour ne pas interrompre le thread principal.
Renvoie
None

AAAAAAAAFFAAAAAAAAFFDocumentation des variables
app.main.CURRENT_DIR = os.path.dirname(os.path.abspath(__file__))
AAAAAAAAFGAAAAAAAAFGapp.main.force_sequence = threading.Event()
AAAAAAAAFHAAAAAAAAFHapp.main.led_indicator = None
AAAAAAAAFIAAAAAAAAFIbool app.main.sequencer_running = False
AAAAAAAAFJAAAAAAAAFJapp.main.SRC_DIR = os.path.dirname(CURRENT_DIR)
AAAAAAAAFKAAAAAAAAFKapp.main.stop_event = threading.Event()
AAAAAAAAFLAAAAAAAAFL

Référence de l'espace de nommage app.mesure_24v_dry_contact
AAAAAAAAFMAAAAAAAAFMFonctions
test_24v_dry_contact ()
Test des contacts secs I/O 24V.

get_dry_contact_status ()
Retourne l'état actuel des contacts secs.

Variables
int CM_24V_OUT_1 = 13
int CM_24V_SENSE_1 = 14
int CM_24V_OUT_2 = 15
int CM_24V_SENSE_2 = 16
int io_24v_ch1_ok = 0
int io_24v_ch2_ok = 0

AAAAAAAAFNAAAAAAAAFNDocumentation des fonctions
app.mesure_24v_dry_contact.get_dry_contact_status ()
AAAAAAAAFOAAAAAAAAFO
Retourne l'état actuel des contacts secs.
Fonction utilitaire qui retourne les derniers états mesurés des contacts secs sans effectuer de nouveau test. Utilise les variables globales mises à jour par test_24v_dry_contact().
Renvoie
Dictionnaire contenant l'état des deux canaux. Format {"ch1": 0|1, "ch2": 0|1} Valeurs 0=ouvert, 1=fermé.
app.mesure_24v_dry_contact.test_24v_dry_contact ()
AAAAAAAAFPAAAAAAAAFP
Test des contacts secs I/O 24V.
Effectue un test complet des deux canaux de contacts secs 24V. Active séquentiellement chaque sortie et lit l'état du capteur correspondant pour déterminer si le contact est fermé ou ouvert. Met à jour les variables globales d'état et affiche les résultats.
Renvoie
Tuple contenant l'état des deux canaux (ch1_state, ch2_state). Valeurs 0=ouvert, 1=fermé.
Note
Utilise des temporisations pour la stabilisation des signaux.

AAAAAAAAFQAAAAAAAAFQDocumentation des variables
int app.mesure_24v_dry_contact.CM_24V_OUT_1 = 13
AAAAAAAAFRAAAAAAAAFRint app.mesure_24v_dry_contact.CM_24V_OUT_2 = 15
AAAAAAAAFSAAAAAAAAFSint app.mesure_24v_dry_contact.CM_24V_SENSE_1 = 14
AAAAAAAAFTAAAAAAAAFTint app.mesure_24v_dry_contact.CM_24V_SENSE_2 = 16
AAAAAAAAFUAAAAAAAAFUint app.mesure_24v_dry_contact.io_24v_ch1_ok = 0
AAAAAAAAFVAAAAAAAAFVint app.mesure_24v_dry_contact.io_24v_ch2_ok = 0
AAAAAAAAFWAAAAAAAAFW

Référence de l'espace de nommage app.pins_cm5
AAAAAAAAFXAAAAAAAAFXVariables
str GPIO_CHIP_PATH = "/dev/gpiochip0"
int MUX_CS_4 = 2
int MUX_CS_3 = 3
int MUX_CS_2 = 7
int MUX_CS_1 = 8
int MUX_MOSI_DUMMY = 10
int MUX_SCLK_DUMMY = 11
int CM_24V_OUT_1 = 13
int CM_24V_SENSE_1 = 14
int CM_24V_OUT_2 = 15
int CM_24V_SENSE_2 = 16
int CMD_RELAY = 17
int CS_ADC_DUMMY = 18
int SPI_MISO_ADC_DMY = 19
int SPI_MOSI_ADC_DMY = 20
int SPI_SCLK_ADC_DMY = 21
int ADC_DRDY = 22
int ADC_START_SYNC = 23
int ADC_A0 = 24
int ADC_A1 = 25
int FRONT_LED = 27
int SPI0_BUS = 0
int SPI1_BUS = 1
int SPI0_DEV0 = 0
int SPI0_DEV1 = 1
int SPI1_DEV0 = 0
int SPI_MUX_SPEED_HZ = 100000
int SPI_ADC_SPEED_HZ = 100000

AAAAAAAAFYAAAAAAAAFYDocumentation des variables
int app.pins_cm5.ADC_A0 = 24
AAAAAAAAFZAAAAAAAAFZint app.pins_cm5.ADC_A1 = 25
AAAAAAAAGAAAAAAAAAGAint app.pins_cm5.ADC_DRDY = 22
AAAAAAAAGBAAAAAAAAGBint app.pins_cm5.ADC_START_SYNC = 23
AAAAAAAAGCAAAAAAAAGCint app.pins_cm5.CM_24V_OUT_1 = 13
AAAAAAAAGDAAAAAAAAGDint app.pins_cm5.CM_24V_OUT_2 = 15
AAAAAAAAGEAAAAAAAAGEint app.pins_cm5.CM_24V_SENSE_1 = 14
AAAAAAAAGFAAAAAAAAGFint app.pins_cm5.CM_24V_SENSE_2 = 16
AAAAAAAAGGAAAAAAAAGGint app.pins_cm5.CMD_RELAY = 17
AAAAAAAAGHAAAAAAAAGHint app.pins_cm5.CS_ADC_DUMMY = 18
AAAAAAAAGIAAAAAAAAGIint app.pins_cm5.FRONT_LED = 27
AAAAAAAAGJAAAAAAAAGJstr app.pins_cm5.GPIO_CHIP_PATH = "/dev/gpiochip0"
AAAAAAAAGKAAAAAAAAGKint app.pins_cm5.MUX_CS_1 = 8
AAAAAAAAGLAAAAAAAAGLint app.pins_cm5.MUX_CS_2 = 7
AAAAAAAAGMAAAAAAAAGMint app.pins_cm5.MUX_CS_3 = 3
AAAAAAAAGNAAAAAAAAGNint app.pins_cm5.MUX_CS_4 = 2
AAAAAAAAGOAAAAAAAAGOint app.pins_cm5.MUX_MOSI_DUMMY = 10
AAAAAAAAGPAAAAAAAAGPint app.pins_cm5.MUX_SCLK_DUMMY = 11
AAAAAAAAGQAAAAAAAAGQint app.pins_cm5.SPI0_BUS = 0
AAAAAAAAGRAAAAAAAAGRint app.pins_cm5.SPI0_DEV0 = 0
AAAAAAAAGSAAAAAAAAGSint app.pins_cm5.SPI0_DEV1 = 1
AAAAAAAAGTAAAAAAAAGTint app.pins_cm5.SPI1_BUS = 1
AAAAAAAAGUAAAAAAAAGUint app.pins_cm5.SPI1_DEV0 = 0
AAAAAAAAGVAAAAAAAAGVint app.pins_cm5.SPI_ADC_SPEED_HZ = 100000
AAAAAAAAGWAAAAAAAAGWint app.pins_cm5.SPI_MISO_ADC_DMY = 19
AAAAAAAAGXAAAAAAAAGXint app.pins_cm5.SPI_MOSI_ADC_DMY = 20
AAAAAAAAGYAAAAAAAAGYint app.pins_cm5.SPI_MUX_SPEED_HZ = 100000
AAAAAAAAGZAAAAAAAAGZint app.pins_cm5.SPI_SCLK_ADC_DMY = 21
AAAAAAAAHAAAAAAAAAHA

Référence de l'espace de nommage app.resistance_mapping
AAAAAAAAHBAAAAAAAAHBFonctions
dict get_channel_mux_map (str sensor_type)
Retourne le mapping CHANNEL_MUX pour un type de sonde donné.

tuple find_closest_channel (float target_resistance, str sensor_type)
Trouve le canal MUX le plus proche pour une résistance cible.

Variables
dict CHANNEL_MUX

AAAAAAAAHCAAAAAAAAHCDocumentation des fonctions
tuple app.resistance_mapping.find_closest_channel (float target_resistance, str sensor_type)
AAAAAAAAHDAAAAAAAAHD
Trouve le canal MUX le plus proche pour une résistance cible.
Algorithme de recherche du canal TMUX offrant la résistance la plus proche de la valeur cible. Calcule l'erreur absolue et relative pour le meilleur canal trouvé.
Paramètres
target_resistance | Valeur de résistance cible recherchée [Ohms].
sensor_type | Type de sonde à utiliser pour la recherche.
Renvoie Tuple (canal, resistance_reelle, erreur_pourcent). Retourne (None, None, None) si aucun canal trouvé.
Exceptions
KeyError | si le type de sonde n'existe pas.
Voici le graphe d'appel pour cette fonction :
IMAGE
dict app.resistance_mapping.get_channel_mux_map (str sensor_type)
AAAAAAAAHEAAAAAAAAHE
Retourne le mapping CHANNEL_MUX pour un type de sonde donné.
Fonction d'accès qui extrait le dictionnaire de correspondance canal/résistance pour un type de sonde spécifique. Valide l'existence du type avant de retourner les données.
Paramètres
sensor_type | Type de sonde demandé (doit exister dans CHANNEL_MUX).
Renvoie Dictionnaire {canal: resistance} pour le type de sonde.
Exceptions
KeyError | si le type de sonde n'est pas supporté.
Voici le graphe des appelants de cette fonction :
IMAGE

AAAAAAAAHFAAAAAAAAHFDocumentation des variables
dict app.resistance_mapping.CHANNEL_MUX
AAAAAAAAHGAAAAAAAAHG

Référence de l'espace de nommage app.resistance_simulation
AAAAAAAAHHAAAAAAAAHHClasses
class ResistanceSimulationErrorException pour les erreurs de simulation de résistance.
class ResistanceSimulatorContrôleur pour la simulation de résistance via MUX.
Fonctions
bool apply_resistance_simulation (float resistance_ohm)
Fonction utilitaire pour appliquer une résistance simulée.

Variables
sim = ResistanceSimulator()
bool success = sim.apply_resistance_simulation(1000.0)
valid = sim.validate_resistance_applied(667.0, tolerance=0.15)

AAAAAAAAHIAAAAAAAAHIDocumentation des fonctions
bool app.resistance_simulation.apply_resistance_simulation (float resistance_ohm)
AAAAAAAAHJAAAAAAAAHJ
Fonction utilitaire pour appliquer une résistance simulée.
Fonction de commodité qui encapsule la création d'un simulateur, l'application d'une résistance et le nettoyage automatique. Utilise le pattern RAII pour la gestion des ressources.
Paramètres
resistance_ohm | Résistance à appliquer [Ohms].
Renvoie True si l'application a réussi, False sinon.

AAAAAAAAHKAAAAAAAAHKDocumentation des variables
app.resistance_simulation.sim = ResistanceSimulator()
AAAAAAAAHLAAAAAAAAHLbool app.resistance_simulation.success = sim.apply_resistance_simulation(1000.0)
AAAAAAAAHMAAAAAAAAHMapp.resistance_simulation.valid = sim.validate_resistance_applied(667.0, tolerance=0.15)
AAAAAAAAHNAAAAAAAAHN

Référence de l'espace de nommage app.sensor_profiles
AAAAAAAAIEAAAAAAAAIEFonctions
get_profile (sensor_name)
Récupère le profil de configuration ADC pour un capteur donné.

Variables
dict SENSOR_PROFILES

AAAAAAAAIFAAAAAAAAIFDocumentation des fonctions
app.sensor_profiles.get_profile ( sensor_name)
AAAAAAAAIGAAAAAAAAIG
Récupère le profil de configuration ADC pour un capteur donné.
Fonction d'accès qui retourne le dictionnaire de configuration contenant les paramètres optimisés (Rref, IDAC, PGA) pour un type de capteur spécifique.
Paramètres
sensor_name | Nom du type de capteur recherché.
Renvoie Dictionnaire contenant les paramètres de configuration:
▪ ref_ohm: résistance de référence [Ohms]
▪ dac_uA: courant d'excitation [microampères]
▪ ga_gain: gain programmable [1-128]
Exceptions
KeyError | si le type de capteur n'est pas reconnu.

AAAAAAAAIHAAAAAAAAIHDocumentation des variables
dict app.sensor_profiles.SENSOR_PROFILES
AAAAAAAAIIAAAAAAAAII

Référence de l'espace de nommage app.temperature_conversion
AAAAAAAAIJAAAAAAAAIJFonctions
resistance_to_temperature (resistance, table)
Convertit une résistance mesurée en température via interpolation linéaire.

resistance_to_temperature_dynamic (resistance, sensor)
Convertit une résistance mesurée en température pour un capteur donné.

temperature_to_resistance_dynamic (temperature, sensor)
Convertit une température en résistance pour un capteur donné (conversion inverse).

convert_temperature_to_resistance (temperature, probe_type)
Fonction de conversion principale pour la simulation de résistance.

get_supported_probe_types ()
Retourne la liste des types de sondes supportés.

validate_temperature_range (temperature, probe_type)
Valide si une température est dans la plage supportée par une sonde.

AAAAAAAAIKAAAAAAAAIKDocumentation des fonctions
app.temperature_conversion.convert_temperature_to_resistance ( temperature, probe_type)
AAAAAAAAILAAAAAAAAIL
Fonction de conversion principale pour la simulation de résistance.
Fonction de haut niveau qui supporte différents types de sondes avec leurs caractéristiques spécifiques. Inclut la normalisation des noms de sondes et la gestion des variantes de nomenclature.
Paramètres
temperature | Température simulée [°C].
probe_type | Type de sonde (formats multiples supportés).
Renvoie Résistance simulée [Ohms] ou None si échec.
Voici le graphe d'appel pour cette fonction :
IMAGE
app.temperature_conversion.get_supported_probe_types ()
AAAAAAAAIMAAAAAAAAIM
Retourne la liste des types de sondes supportés.
Fonction utilitaire qui extrait la liste complète des noms de capteurs disponibles dans les tables de conversion.
Renvoie
Liste des noms de capteurs disponibles pour conversion.
app.temperature_conversion.resistance_to_temperature ( resistance, table)
AAAAAAAAINAAAAAAAAIN
Convertit une résistance mesurée en température via interpolation linéaire.
Algorithme d'interpolation linéaire qui recherche l'intervalle contenant la résistance mesurée et calcule la température correspondante. Gère les cas limites hors plage de mesure.
Paramètres
resistance | Résistance mesurée [Ohms].
table | Liste de tuples (résistance, température) pour interpolation.
Renvoie Température interpolée [°C], ou valeurs limites si hors plage.
app.temperature_conversion.resistance_to_temperature_dynamic ( resistance, sensor)
AAAAAAAAIOAAAAAAAAIO
Convertit une résistance mesurée en température pour un capteur donné.
Fonction dynamique qui sélectionne automatiquement la table de conversion appropriée selon le type de capteur spécifié. Effectue la validation du capteur avant conversion.
Paramètres
resistance | Résistance mesurée [Ohms].
sensor | Nom du type de capteur à utiliser.
Renvoie Température interpolée [°C] ou None si hors limites.
Exceptions
ValueError | si le capteur n'est pas reconnu.
app.temperature_conversion.temperature_to_resistance_dynamic ( temperature, sensor)
AAAAAAAAIPAAAAAAAAIP
Convertit une température en résistance pour un capteur donné (conversion inverse).
Fonction de conversion inverse utilisée pour la simulation de résistance. Effectue l'interpolation linéaire sur l'axe température pour obtenir la résistance correspondante selon le type de capteur.
Paramètres
temperature | Température d'entrée [°C].
sensor | Nom du type de capteur à utiliser.
Renvoie Résistance interpolée [Ohms] ou None si hors limites.
Exceptions
ValueError | si le capteur n'est pas reconnu.
Voici le graphe des appelants de cette fonction :
IMAGE
app.temperature_conversion.validate_temperature_range ( temperature, probe_type)
AAAAAAAAIQAAAAAAAAIQ
Valide si une température est dans la plage supportée par une sonde.
Fonction de validation qui vérifie si une température donnée est compatible avec la plage de fonctionnement d'un type de capteur spécifique selon sa table de calibration.
Paramètres
temperature | Température à valider [°C].
probe_type | Type de sonde à vérifier.
Renvoie True si la température est dans la plage supportée.

Référence de l'espace de nommage app.temperature_simulation
AAAAAAAAIRAAAAAAAAIRFonctions
Optional[float] calculate_simulated_temperature (float t_mes, float t_prev, float n, float k_m)
Calcule la température simulée selon la formule prédictive.

bool validate_simulation_parameters (str probe_type, float n, float k_m, float t_mes, float t_prev)
Valide tous les paramètres de simulation avant exécution.

Optional[float] run_temperature_simulation (dict simulation_data)
Exécute une simulation complète de température avec dictionnaire.

AAAAAAAAISAAAAAAAAISDocumentation des fonctions
Optional[float] app.temperature_simulation.calculate_simulated_temperature (float t_mes, float t_prev, float n, float k_m)
AAAAAAAAITAAAAAAAAIT
Calcule la température simulée selon la formule prédictive.
Implémente la formule T_sim = T_mes + ((T_prev - T_mes) * n * exp(k_m)) avec validation complète des paramètres et gestion des erreurs numériques (overflow, underflow, valeurs infinies).
Paramètres
t_mes | Température mesurée [°C].
t_prev | Température prévue [°C].
n | ParamÃ¨tre de pondÃ©ration [-âˆž, +âˆž].
k_m | ParamÃ¨tre exposant pour fonction exponentielle [-âˆž, +âˆž].
Renvoie Température simulée [°C] ou None en cas d'erreur.
Exceptions
OverflowError | si exp(k_m) dépasse les limites numériques.
Avertissement Limitation automatique des paramètres extrêmes.
Voici le graphe des appelants de cette fonction :
IMAGE
Optional[float] app.temperature_simulation.run_temperature_simulation (dict simulation_data)
AAAAAAAAIUAAAAAAAAIU
Exécute une simulation complète de température avec dictionnaire.
Fonction principale d'orchestration qui extrait les paramètres d'un dictionnaire, valide tous les paramètres et execute la simulation complète avec gestion d'erreur robuste.
Paramètres
Dictionnaire contenant tous les paramètres requis: ◦ robe_type: Type de sonde (str)
◦ : Paramètre de pondération (float)
◦ _m: Paramètre exposant (float)
◦ emperature: Température mesurée (float)
◦ orecast_temperature: Température prévue (float)
simulation_data
Renvoie
Température simulée [°C] ou None si erreur.
Avertissement
Retourne None pour toute erreur de validation ou calcul.
Voici le graphe d'appel pour cette fonction :
IMAGE
bool app.temperature_simulation.validate_simulation_parameters (str probe_type, float n, float k_m, float t_mes, float t_prev)
AAAAAAAAIVAAAAAAAAIV
Valide tous les paramètres de simulation avant exécution.
Fonction de validation complète qui vérifie la cohérence et les plages de tous les paramètres d'entrée. Inclut la vérification interactive pour les écarts importants.
Paramètres
probe_type | Type de sonde à utiliser pour la simulation.
n | Paramètre de pondération de la simulation.
k_m | Paramètre exposant de la fonction exponentielle.
t_mes | Température mesurée à valider [°C].
t_prev | Température prévue à valider [°C].
Renvoie True si tous les paramètres sont valides.
Avertissement
Demande confirmation utilisateur pour écarts importants.
Voici le graphe des appelants de cette fonction :
IMAGE

Référence de l'espace de nommage app.test_lm70_compatible
AAAAAAAAIWAAAAAAAAIWFonctions
test_lm70 ()
Test de communication SPI avec le capteur LM70.

Variables
levelformat
handlers
logger = logging.getLogger("LM70-Test")
int LM70_CS_GPIO = 18
int SPI_MOSI_ADC_GPIO = 20
int SPI_MISO_ADC_GPIO = 19
int SPI_SCLK_ADC_GPIO = 21
current_dir = os.path.dirname(os.path.abspath(__file__))
str src_dir = os.path.dirname(current_dir) if "src" in current_dir else current_dir
spi = spidev.SpiDev()
max_speed_hz
mode
bits_per_word

AAAAAAAAIXAAAAAAAAIXDocumentation des fonctions
app.test_lm70_compatible.test_lm70 ()
AAAAAAAAIYAAAAAAAAIY
Test de communication SPI avec le capteur LM70.
Voici le graphe d'appel pour cette fonction :
IMAGE
Voici le graphe des appelants de cette fonction :
IMAGE

AAAAAAAAIZAAAAAAAAIZDocumentation des variables
app.test_lm70_compatible.bits_per_word
AAAAAAAAJAAAAAAAAAJAapp.test_lm70_compatible.current_dir = os.path.dirname(os.path.abspath(__file__))
AAAAAAAAJBAAAAAAAAJBapp.test_lm70_compatible.format
AAAAAAAAJCAAAAAAAAJCapp.test_lm70_compatible.handlers
AAAAAAAAJDAAAAAAAAJDapp.test_lm70_compatible.level
AAAAAAAAJEAAAAAAAAJEint app.test_lm70_compatible.LM70_CS_GPIO = 18
AAAAAAAAJFAAAAAAAAJFapp.test_lm70_compatible.logger = logging.getLogger("LM70-Test")
AAAAAAAAJGAAAAAAAAJGapp.test_lm70_compatible.max_speed_hz
AAAAAAAAJHAAAAAAAAJHapp.test_lm70_compatible.mode
AAAAAAAAJIAAAAAAAAJIapp.test_lm70_compatible.spi = spidev.SpiDev()
AAAAAAAAJJAAAAAAAAJJint app.test_lm70_compatible.SPI_MISO_ADC_GPIO = 19
AAAAAAAAJKAAAAAAAAJKint app.test_lm70_compatible.SPI_MOSI_ADC_GPIO = 20
AAAAAAAAJLAAAAAAAAJLint app.test_lm70_compatible.SPI_SCLK_ADC_GPIO = 21
AAAAAAAAJMAAAAAAAAJMstr app.test_lm70_compatible.src_dir = os.path.dirname(current_dir) if "src" in current_dir else current_dir
AAAAAAAAJNAAAAAAAAJN

Référence de l'espace de nommage app.test_spi_adc
AAAAAAAAJOAAAAAAAAJOFonctions
test_spi_adc ()

AAAAAAAAJPAAAAAAAAJPDocumentation des fonctions
app.test_spi_adc.test_spi_adc ()
AAAAAAAAJQAAAAAAAAJQ

Référence de l'espace de nommage config_module
AAAAAAAAJRAAAAAAAAJREspaces de nommage
namespace cm5_config

Référence de l'espace de nommage config_module.cm5_config
AAAAAAAAJSAAAAAAAAJSFonctions
build_hw ()
Initialise et configure tout le matériel CM5.

Variables
list ADC_CHANNELS = [1, 2, 3, 4]

AAAAAAAAJTAAAAAAAAJTDocumentation des fonctions
config_module.cm5_config.build_hw ()
AAAAAAAAJUAAAAAAAAJU
Initialise et configure tout le matériel CM5.
Crée les instances des composants matériels avec configuration fixe LED frontale, multiplexeur TMUX et ADC. Configure la LED en sortie et l'allume immédiatement pour indication système.
Renvoie
Dictionnaire contenant toutes les instances matérielles:
▪ led": Instance GPIO pour LED frontale
▪ tmux": Instance Tmux1204 pour sélection canaux
▪ adc": Instance Ads124s08 pour conversion analogique
Avertissement
LED allumée automatiquement pour indiquer système actif.

AAAAAAAAJVAAAAAAAAJVDocumentation des variables
list config_module.cm5_config.ADC_CHANNELS = [1, 2, 3, 4]
AAAAAAAAJWAAAAAAAAJW

Référence de l'espace de nommage webui
AAAAAAAAJXAAAAAAAAJXEspaces de nommage
namespace webui_server

Référence de l'espace de nommage webui.webui_server
AAAAAAAAJYAAAAAAAAJYFonctions
serve_index ()
Sert la page principale de l'interface web.

get_config ()
Récupère la configuration actuelle des capteurs.

put_config ()
Sauvegarde une nouvelle configuration des capteurs.

get_last ()
Récupère le dernier état du système de mesure.

force_reload ()
Force le rechargement de la configuration au prochain cycle.

Variables
BASE_DIR = os.path.abspath(os.path.join(os.path.dirname(__file__), ".."))
CONFIG_PATH = os.path.join(BASE_DIR, "config_module", "sensors.json")
STATE_PATH = os.path.join(BASE_DIR, "state", "last_state.json")
WEBUI_DIR = os.path.dirname(__file__)
app = Flask(__name__, static_folder=WEBUI_DIR, static_url_path='/static')
host
port

AAAAAAAAJZAAAAAAAAJZDocumentation des fonctions
webui.webui_server.force_reload ()
AAAAAAAAKAAAAAAAAAKA
Force le rechargement de la configuration au prochain cycle.
Crée un fichier flag force_reload.flag avec horodatage pour déclencher le rechargement de configuration par le processus principal lors du prochain cycle de mesure.
Renvoie
Confirmation de demande ou message d'erreur avec code HTTP.
webui.webui_server.get_config ()
AAAAAAAAKBAAAAAAAAKB
Récupère la configuration actuelle des capteurs.
Lecture du fichier sensors.json et retour des données de configuration en format JSON. Gère les erreurs de lecture et affiche des informations de débogage.
Renvoie
Configuration JSON ou message d'erreur avec code HTTP.
webui.webui_server.get_last ()
AAAAAAAAKCAAAAAAAAKC
Récupère le dernier état du système de mesure.
Lecture du fichier last_state.json contenant les dernières mesures, températures et statuts. Gère le cas où le fichier n'existe pas encore et retourne un état par défaut.
Renvoie
État JSON du système ou structure par défaut si fichier absent.
webui.webui_server.put_config ()
AAAAAAAAKDAAAAAAAAKD
Sauvegarde une nouvelle configuration des capteurs.
Reçoit des données JSON, valide le contenu et sauvegarde dans sensors.json avec sauvegarde atomique via fichier temporaire. Affiche un résumé des changements principaux.
Renvoie
Statut de sauvegarde ou message d'erreur avec code HTTP.
webui.webui_server.serve_index ()
AAAAAAAAKEAAAAAAAAKE
Sert la page principale de l'interface web.
Route racine qui retourne le fichier index.html depuis le répertoire webui pour affichage de l'interface utilisateur.
Renvoie
Fichier HTML de l'interface principale.

AAAAAAAAKFAAAAAAAAKFDocumentation des variables
webui.webui_server.app = Flask(__name__, static_folder=WEBUI_DIR, static_url_path='/static')
AAAAAAAAKGAAAAAAAAKGwebui.webui_server.BASE_DIR = os.path.abspath(os.path.join(os.path.dirname(__file__), ".."))
AAAAAAAAKHAAAAAAAAKHwebui.webui_server.CONFIG_PATH = os.path.join(BASE_DIR, "config_module", "sensors.json")
AAAAAAAAKIAAAAAAAAKIwebui.webui_server.host
AAAAAAAAKJAAAAAAAAKJwebui.webui_server.port
AAAAAAAAKKAAAAAAAAKKwebui.webui_server.STATE_PATH = os.path.join(BASE_DIR, "state", "last_state.json")
AAAAAAAAKLAAAAAAAAKLwebui.webui_server.WEBUI_DIR = os.path.dirname(__file__)
AAAAAAAAKMAAAAAAAAKM
Documentation des classes
Référence de la classe app.hw_mux_adg731.Adg731MuxSpi
AAAAAAAADZAAAAAAAADZ
Pilote SPI pour multiplexeurs ADG731.
Graphe de collaboration de app.hw_mux_adg731.Adg731MuxSpi:
IMAGE

Fonctions membres publiques
__init__ (self, speed_hz=100000)
Initialise le pilote pour les multiplexeurs ADG731.

close (self)
Ferme toutes les interfaces SPI.

set_channel (self, board_index, address)
Active un canal spécifique sur une carte donnée.

set_output_channel (self, channel_index)
Utilitaire simple pour sélectionner un canal de sortie.

Attributs publics
speed = speed_hz
list handles = []
Attributs publics statiques
list DEV = ["/dev/spidev0.0", "/dev/spidev0.1", "/dev/spidev0.2", "/dev/spidev0.3"]

Description détaillée
Pilote SPI pour multiplexeurs ADG731.
Classe pour contrôler jusqu'à 4 multiplexeurs ADG731 via l'interface SPI0. Chaque multiplexeur peut gérer 32 canaux. Configure automatiquement les paramètres SPI optimaux et gère la communication avec les circuits.

AAAAAAAAEAAAAAAAAAEADocumentation des constructeurs et destructeur
app.hw_mux_adg731.Adg731MuxSpi.__init__ ( self, speed_hz = 100000)
AAAAAAAAEBAAAAAAAAEB
Initialise le pilote pour les multiplexeurs ADG731.
Configure l'interface SPI pour chaque canal disponible, définit les paramètres de communication et initialise les handles pour jusqu'à 4 cartes multiplexeurs.
Paramètres
speed_hz | Vitesse SPI en Hz (par défaut 100kHz).

AAAAAAAAECAAAAAAAAECDocumentation des fonctions membres
app.hw_mux_adg731.Adg731MuxSpi.close ( self)
AAAAAAAAEDAAAAAAAAED
Ferme toutes les interfaces SPI.
Parcourt tous les handles SPI ouverts et les ferme proprement. Gère les erreurs de fermeture pour éviter les exceptions lors du nettoyage.
app.hw_mux_adg731.Adg731MuxSpi.set_channel ( self, board_index, address)
AAAAAAAAEEAAAAAAAAEE
Active un canal spécifique sur une carte donnée.
Envoie la commande de sélection de canal vers la carte multiplexeur spécifiée. Génère l'octet de contrôle et l'envoie via SPI.
Paramètres
board_index | Index de la carte (0-3).
address | Adresse du canal à activer (0-31).
Renvoie Octet de contrôle envoyé, ou None si erreur.
Exceptions
ValueError | Si l'index de carte est hors plage.
Voici le graphe d'appel pour cette fonction :
IMAGE
Voici le graphe des appelants de cette fonction :
IMAGE
app.hw_mux_adg731.Adg731MuxSpi.set_output_channel ( self, channel_index)
AAAAAAAAEFAAAAAAAAEF
Utilitaire simple pour sélectionner un canal de sortie.
Fonction de commodité qui utilise automatiquement la carte 0 et mappe directement l'index de canal sur l'adresse du multiplexeur.
Paramètres
channel_index | Index du canal de sortie (0-31).
Renvoie Octet de contrôle envoyé, ou None si erreur.
Exceptions
ValueError | Si l'index de canal est hors plage.
Voici le graphe d'appel pour cette fonction :
IMAGE

AAAAAAAAEGAAAAAAAAEGDocumentation des données membres
list app.hw_mux_adg731.Adg731MuxSpi.DEV = ["/dev/spidev0.0", "/dev/spidev0.1", "/dev/spidev0.2", "/dev/spidev0.3"][static]
AAAAAAAAEHAAAAAAAAEHlist app.hw_mux_adg731.Adg731MuxSpi.handles = []
AAAAAAAAEIAAAAAAAAEIapp.hw_mux_adg731.Adg731MuxSpi.speed = speed_hz
AAAAAAAAEJAAAAAAAAEJ
La documentation de cette classe a été générée à partir du fichier suivant :
C:/Users/thebi/Documents/2510_RegulationChauffage/doc/9.SoftWare/Doxygen/src/app/hw_mux_adg731.py

Référence de la classe app.adc_ads124s08.Ads124s08
AAAAAAAABSAAAAAAAABS
Driver pour l'ADC ADS124S08 avec interface SPI.
Graphe de collaboration de app.adc_ads124s08.Ads124s08:
IMAGE

Fonctions membres publiques
__init__ (self)
Constructeur de la classe Ads124s08.

read_id (self)
Lit le registre d'identification de l'ADC.

close (self)
Ferme les interfaces SPI et GPIO proprement.

wait_drdy_falling_edge (self, timeout_s)
Attend un front descendant sur DRDY (HIGH -> LOW) avec timeout.

set_single_shot_lowlatency (self, dr_nibble)
Configure le mode single-shot low-latency de l'ADC.

configure_channel (self, channel_index, pga_gain, idac_uA)
Configure un canal ADC avec ses paramètres de mesure.

start (self)
Démarre une conversion ADC.

stop (self)
Arrête une conversion ADC en cours.

read_code24 (self)
Lit un code de données 24 bits depuis l'ADC.

measure_resistance (self, rref_ohm, pga_gain, timeout_s)
Mesure la résistance d'une sonde via l'ADC.

measure_temperature (self, sensor_name, rref_ohm, pga_gain, timeout_s)
Mesure la température d'un capteur via l'ADC.

read_gain (self)
Lit le registre de gain PGA pour diagnostic.

read_ref (self)
Lit le registre de configuration de la référence.

read_inpmux (self)
Lit le registre de configuration du multiplexeur d'entrée.

Attributs publics
spi = spidev.SpiDev()
gpio_drdy = GPIO(GPIO_CHIP_PATH, ADC_DRDY, "in")
Fonctions membres protégées
_rreg (self, addr, nbytes)
Lit un ou plusieurs registres de l'ADC via SPI.

_wreg (self, addr, data_bytes)
Écrit dans un ou plusieurs registres de l'ADC via SPI.

_sclk_nudge (self)
Envoie un coup de pouce sur SCLK pour synchroniser DRDY.

_ensure_drdy_high (self, timeout_ms)
Assure que le signal DRDY est à l'état HIGH.

Description détaillée
Driver pour l'ADC ADS124S08 avec interface SPI.
Cette classe encapsule toutes les fonctionnalités nécessaires pour communiquer avec l'ADC ADS124S08 via SPI en mode 1.0. Supporte la configuration automatique, la mesure de résistance et la conversion en température.
Note
L'ADC doit être connecté via SPI1 et le signal DRDY sur GPIO.
Voir également
configure_channel, measure_resistance, measure_temperature

AAAAAAAABTAAAAAAAABTDocumentation des constructeurs et destructeur
app.adc_ads124s08.Ads124s08.__init__ ( self)
AAAAAAAABUAAAAAAAABU
Constructeur de la classe Ads124s08.
Initialise la communication SPI, configure le GPIO DRDY, effectue un reset de l'ADC et vérifie la communication en lisant le registre d'identification.
Exceptions
Peut | lever des exceptions SPI ou GPIO en cas d'échec.
Postcondition L'ADC est prêt pour la configuration et les mesures.

AAAAAAAABVAAAAAAAABVDocumentation des fonctions membres
app.adc_ads124s08.Ads124s08._ensure_drdy_high ( self, timeout_ms)[protected]
AAAAAAAABWAAAAAAAABW
Assure que le signal DRDY est à l'état HIGH.
Attend que DRDY passe à HIGH avec possibilité de coup de pouce sur SCLK si nécessaire. Timeout configurable.
Paramètres
timeout_ms | Timeout en millisecondes pour l'attente.
Renvoie True si DRDY est HIGH, False en cas de timeout.
Note
Méthode critique pour la synchronisation des conversions.
Voir également
wait_drdy_falling_edge
Voici le graphe d'appel pour cette fonction :
IMAGE
app.adc_ads124s08.Ads124s08._rreg ( self, addr, nbytes)[protected]
AAAAAAAABXAAAAAAAABX
Lit un ou plusieurs registres de l'ADC via SPI.
Utilise la commande RREG de l'ADS124S08 pour lire des registres consécutifs starting à l'adresse donnée.
Paramètres
addr | Adresse du premier registre à lire (0x00-0x1F).
nbytes | Nombre d'octets à lire.
Renvoie Liste des valeurs lues depuis les registres.
Note
Méthode privée pour les opérations internes du driver.
Voir également
_wreg
Voici le graphe des appelants de cette fonction :
IMAGE
app.adc_ads124s08.Ads124s08._sclk_nudge ( self)[protected]
AAAAAAAABYAAAAAAAABY
Envoie un coup de pouce sur SCLK pour synchroniser DRDY.
Effectue une lecture factice du registre STATUS pour générer des transitions sur SCLK et forcer DRDY à l'état HIGH.
Renvoie
Rien.
Note
Utilisé quand DRDY reste bloqué à LOW de manière inattendue.
Voir également
_ensure_drdy_high
Voici le graphe des appelants de cette fonction :
IMAGE
app.adc_ads124s08.Ads124s08._wreg ( self, addr, data_bytes)[protected]
AAAAAAAABZAAAAAAAABZ
Écrit dans un ou plusieurs registres de l'ADC via SPI.
Utilise la commande WREG de l'ADS124S08 pour écrire des données dans des registres consécutifs.
Paramètres
addr | Adresse du premier registre à écrire (0x00-0x1F).
data_bytes | Liste des octets à écrire dans les registres.
Renvoie Rien.
Note
Méthode privée pour les opérations internes du driver.
Voir également
_rreg
Voici le graphe d'appel pour cette fonction :
IMAGE
Voici le graphe des appelants de cette fonction :
IMAGE
app.adc_ads124s08.Ads124s08.close ( self)
AAAAAAAACAAAAAAAAACA
Ferme les interfaces SPI et GPIO proprement.
Libère les ressources système utilisées par le driver. Méthode à appeler avant la destruction de l'objet.
Renvoie
Rien.
Note
Ignore les erreurs de fermeture pour éviter les exceptions.
Voir également
init
Voici le graphe d'appel pour cette fonction :
IMAGE
Voici le graphe des appelants de cette fonction :
IMAGE
app.adc_ads124s08.Ads124s08.configure_channel ( self, channel_index, pga_gain, idac_uA)
AAAAAAAACBAAAAAAAACB
Configure un canal ADC avec ses paramètres de mesure.
Configure complètement un canal ADC avec le gain PGA, le courant IDAC et le routage des entrées analogiques. Effectue une configuration séquentielle de tous les registres.
Paramètres
channel_index | Index du canal physique (1-4).
pga_gain | Gain de l'amplificateur programmable (1-128).
idac_uA | Courant IDAC en microampères (10-2000).
Renvoie Rien.
Exceptions
ValueError | si le canal ou les paramètres sont invalides.
Voir également encode_gain, encode_idac_uA
Voici le graphe d'appel pour cette fonction :
IMAGE
app.adc_ads124s08.Ads124s08.measure_resistance ( self, rref_ohm, pga_gain, timeout_s)
AAAAAAAACCAAAAAAAACC
Mesure la résistance d'une sonde via l'ADC.
Effectue une mesure complète: démarrage de conversion, attente DRDY, lecture du code et calcul de la résistance selon la formule ratiométrique.
Paramètres
rref_ohm | Résistance de référence en ohms.
pga_gain | Gain PGA utilisé pour la mesure.
timeout_s | Timeout en secondes pour la conversion.
Renvoie Résistance mesurée en ohms ou None en cas d'erreur.
Note
Utilise la formule: R = |code|/FS * (Rref / gain).
Voir également
measure_temperature, configure_channel
Voici le graphe d'appel pour cette fonction :
IMAGE
Voici le graphe des appelants de cette fonction :
IMAGE
app.adc_ads124s08.Ads124s08.measure_temperature ( self, sensor_name, rref_ohm, pga_gain, timeout_s)
AAAAAAAACDAAAAAAAACD
Mesure la température d'un capteur via l'ADC.
Effectue une mesure de résistance puis utilise les tables de conversion de capteurs pour obtenir la température correspondante en degrés Celsius.
Paramètres
sensor_name | Nom du capteur (doit exister dans SENSOR_TABLES).
rref_ohm | Résistance de référence en ohms.
pga_gain | Gain PGA utilisé pour la mesure.
timeout_s | Timeout en secondes pour la conversion.
Renvoie Température mesurée en °C ou None si erreur.
Exceptions
Retourne | None si capteur inconnu ou hors plage.
Voir également measure_resistance, resistance_to_temperature_dynamic
Voici le graphe d'appel pour cette fonction :
IMAGE
app.adc_ads124s08.Ads124s08.read_code24 ( self)
AAAAAAAACEAAAAAAAACE
Lit un code de données 24 bits depuis l'ADC.
Utilise la commande RDATA pour lire les 3 octets de données de conversion et les convertit en entier signé.
Renvoie
Valeur signée 24 bits ou None en cas d'erreur SPI.
Note
Doit être appelé après détection du front descendant DRDY.
Voir également
sign_extend_24, measure_resistance
Voici le graphe d'appel pour cette fonction :
IMAGE
Voici le graphe des appelants de cette fonction :
IMAGE
app.adc_ads124s08.Ads124s08.read_gain ( self)
AAAAAAAACFAAAAAAAACF
Lit le registre de gain PGA pour diagnostic.
Effectue une lecture du registre PGA et affiche sa valeur pour vérification de la configuration du gain.
Renvoie
Valeur brute du registre PGA (0x00-0xFF).
Note
Utilisé principalement pour le debug et la vérification.
Voir également
configure_channel
Voici le graphe d'appel pour cette fonction :
IMAGE
app.adc_ads124s08.Ads124s08.read_id ( self)
AAAAAAAACGAAAAAAAACG
Lit le registre d'identification de l'ADC.
Effectue une lecture du registre ID (0x00) pour vérifier la communication SPI et identifier le type d'ADC connecté.
Renvoie
Valeur du registre ID (0x00-0xFF) ou None en cas d'erreur.
Note
Utilisé principalement pour la vérification de communication.
Voir également
init
app.adc_ads124s08.Ads124s08.read_inpmux ( self)
AAAAAAAACHAAAAAAAACH
Lit le registre de configuration du multiplexeur d'entrée.
Effectue une lecture du registre INPMUX et affiche sa valeur pour vérification du routage des entrées analogiques.
Renvoie
Valeur brute du registre INPMUX (0x00-0xFF).
Note
Utilisé principalement pour le debug et la vérification.
Voir également
configure_channel
app.adc_ads124s08.Ads124s08.read_ref ( self)
AAAAAAAACIAAAAAAAACI
Lit le registre de configuration de la référence.
Effectue une lecture du registre REF et affiche sa valeur pour vérification de la configuration de la référence.
Renvoie
Valeur brute du registre REF (0x00-0xFF).
Note
Utilisé principalement pour le debug et la vérification.
Voir également
configure_channel
Voici le graphe d'appel pour cette fonction :
IMAGE
app.adc_ads124s08.Ads124s08.set_single_shot_lowlatency ( self, dr_nibble)
AAAAAAAACJAAAAAAAACJ
Configure le mode single-shot low-latency de l'ADC.
Configure le registre DATARATE pour utiliser le mode single-shot avec filtre low-latency et data rate spécifié.
Paramètres
dr_nibble | Code de data rate (4 bits, 0x00-0x0F).
Renvoie Rien.
Note
Mode optimisé pour des mesures rapides et ponctuelles.
Voir également
configure_channel
Voici le graphe des appelants de cette fonction :
IMAGE
app.adc_ads124s08.Ads124s08.start ( self)
AAAAAAAACKAAAAAAAACK
Démarre une conversion ADC.
Assure que DRDY est à HIGH puis envoie la commande START pour initier une nouvelle conversion sur le canal configuré.
Renvoie
Rien.
Note
DRDY doit être HIGH avant le START pour une conversion valide.
Voir également
stop, wait_drdy_falling_edge
Voici le graphe des appelants de cette fonction :
IMAGE
app.adc_ads124s08.Ads124s08.stop ( self)
AAAAAAAACLAAAAAAAACL
Arrête une conversion ADC en cours.
Envoie la commande STOP pour interrompre toute conversion en cours et remettre l'ADC en état idle.
Renvoie
Rien.
Note
Utilisé après lecture des données ou en cas d'erreur.
Voir également
start, read_code24
Voici le graphe des appelants de cette fonction :
IMAGE
app.adc_ads124s08.Ads124s08.wait_drdy_falling_edge ( self, timeout_s)
AAAAAAAACMAAAAAAAACM
Attend un front descendant sur DRDY (HIGH -> LOW) avec timeout.
Surveille le signal DRDY pour détecter une transition de HIGH vers LOW, indiquant qu'une nouvelle conversion est disponible.
Paramètres
timeout_s | Timeout en secondes pour l'attente du front.
Renvoie True si front descendant détecté, False en cas de timeout.
Note
Méthode cruciale pour la synchronisation des mesures.
Voir également
measure_resistance
Voici le graphe d'appel pour cette fonction :
IMAGE
Voici le graphe des appelants de cette fonction :
IMAGE

AAAAAAAACNAAAAAAAACNDocumentation des données membres
app.adc_ads124s08.Ads124s08.gpio_drdy = GPIO(GPIO_CHIP_PATH, ADC_DRDY, "in")
AAAAAAAACOAAAAAAAACOapp.adc_ads124s08.Ads124s08.spi = spidev.SpiDev()
AAAAAAAACPAAAAAAAACP
La documentation de cette classe a été générée à partir du fichier suivant :
C:/Users/thebi/Documents/2510_RegulationChauffage/doc/9.SoftWare/Doxygen/src/app/adc_ads124s08.py

Référence de la classe app.api_client.ApiClient
AAAAAAAADAAAAAAAAADA
Client pour interroger les APIs oblosolutions.ch.
Graphe de collaboration de app.api_client.ApiClient:
IMAGE

Fonctions membres publiques
__init__ (self, str mac_address)
Initialise le client API.

Dict[str, Any] get_parameters (self)
Récupère les paramètres depuis l'API td25_param.

Dict[str, Any] get_forecast (self)
Récupère la température prévue depuis l'API td25_forecast.

bool post_measured_temperature (self, float temperature, int channel=None)
Envoie la température mesurée vers l'API td25_param.

Attributs publics
mac_address = mac_address
str base_url = "https://dev.oblosolutions.ch"
Attributs publics statiques
str API_PATH_PREFIX = ""

Description détaillée
Client pour interroger les APIs oblosolutions.ch.
Fournit des méthodes pour récupérer les paramètres de simulation, les prévisions météo et envoyer les mesures de température. Gère automatiquement les retries et les timeouts.

AAAAAAAADBAAAAAAAADBDocumentation des constructeurs et destructeur
app.api_client.ApiClient.__init__ ( self, str mac_address)
AAAAAAAADCAAAAAAAADC
Initialise le client API.
Configure l'adresse MAC du dispositif et l'URL de base pour les communications avec les services oblosolutions.ch.
Paramètres
mac_address | Adresse MAC du dispositif (ex: "0030DEABCDEF").

AAAAAAAADDAAAAAAAADDDocumentation des fonctions membres
Dict[str, Any] app.api_client.ApiClient.get_forecast ( self)
AAAAAAAADEAAAAAAAADE
Récupère la température prévue depuis l'API td25_forecast.
Effectue une requête GET vers l'endpoint td25_forecast avec l'adresse MAC comme paramètre. Parse la réponse JSON et extrait la température de prévision météorologique. Inclut un système de retry automatique en cas d'échec.
Renvoie
Dictionnaire contenant la temperature prévue.
Exceptions
ApiError | En cas d'erreur de récupération des données.
Dict[str, Any] app.api_client.ApiClient.get_parameters ( self)
AAAAAAAADFAAAAAAAADF
Récupère les paramètres depuis l'API td25_param.
Effectue une requête GET vers l'endpoint td25_param avec l'adresse MAC comme paramètre. Parse la réponse JSON et extrait les champs probe_type, n, k_m et temperature. Inclut un système de retry automatique en cas d'échec.
Renvoie
Dictionnaire contenant probe_type, n, k_m, temperature.
Exceptions
ApiError | En cas d'erreur de récupération des données.
bool app.api_client.ApiClient.post_measured_temperature ( self, float temperature, int channel = None)
AAAAAAAADGAAAAAAAADG
Envoie la température mesurée vers l'API td25_param.
Effectue une requête POST vers l'endpoint td25_param avec la température mesurée et optionnellement le numéro de canal. Tous les paramètres sont envoyés dans l'URL comme paramètres de requête. Inclut un système de retry automatique.
Paramètres
temperature | Température mesurée en °C.
channel | Canal de mesure (optionnel).
Renvoie True si succès, False sinon.

AAAAAAAADHAAAAAAAADHDocumentation des données membres
str app.api_client.ApiClient.API_PATH_PREFIX = ""[static]
AAAAAAAADIAAAAAAAADIstr app.api_client.ApiClient.base_url = "https://dev.oblosolutions.ch"
AAAAAAAADJAAAAAAAADJapp.api_client.ApiClient.mac_address = mac_address
AAAAAAAADKAAAAAAAADK
La documentation de cette classe a été générée à partir du fichier suivant :
C:/Users/thebi/Documents/2510_RegulationChauffage/doc/9.SoftWare/Doxygen/src/app/api_client.py

Référence de la classe app.api_client.ApiError
AAAAAAAADLAAAAAAAADL
Exception pour les erreurs d'API.
Graphe d'héritage de app.api_client.ApiError:
IMAGE

Graphe de collaboration de app.api_client.ApiError:
IMAGE

Description détaillée
Exception pour les erreurs d'API.
Exception personnalisée levée en cas d'erreur lors des communications avec les APIs oblosolutions.ch.

La documentation de cette classe a été générée à partir du fichier suivant :
C:/Users/thebi/Documents/2510_RegulationChauffage/doc/9.SoftWare/Doxygen/src/app/api_client.py

Référence de la classe app.front_led_management.LedErrorIndicator
AAAAAAAADSAAAAAAAADS
Gestionnaire de LED avec patterns d'erreur.
Graphe de collaboration de app.front_led_management.LedErrorIndicator:
IMAGE

Attributs publics statiques
float BASE_BLINK_TIME = 0.2
float CYCLE_TIME = 10.0

Description détaillée
Gestionnaire de LED avec patterns d'erreur.
Classe pour contrôler une LED frontale avec différents patterns de clignotement selon les états du système. Supporte les modes normal, standby, séquence en cours et divers patterns d'erreur avec clignotements codifiés.

AAAAAAAADTAAAAAAAADTDocumentation des données membres
float app.front_led_management.LedErrorIndicator.BASE_BLINK_TIME = 0.2[static]
AAAAAAAADUAAAAAAAADUfloat app.front_led_management.LedErrorIndicator.CYCLE_TIME = 10.0[static]
AAAAAAAADVAAAAAAAADV
La documentation de cette classe a été générée à partir du fichier suivant :
C:/Users/thebi/Documents/2510_RegulationChauffage/doc/9.SoftWare/Doxygen/src/app/front_led_management.py

Référence de la classe app.resistance_simulation.ResistanceSimulationError
AAAAAAAAHOAAAAAAAAHO
Exception pour les erreurs de simulation de résistance.
Graphe d'héritage de app.resistance_simulation.ResistanceSimulationError:
IMAGE

Graphe de collaboration de app.resistance_simulation.ResistanceSimulationError:
IMAGE

Description détaillée
Exception pour les erreurs de simulation de résistance.
Exception spécialisée levée lors d'erreurs dans le processus de simulation de résistance via le multiplexeur.

La documentation de cette classe a été générée à partir du fichier suivant :
C:/Users/thebi/Documents/2510_RegulationChauffage/doc/9.SoftWare/Doxygen/src/app/resistance_simulation.py

Référence de la classe app.resistance_simulation.ResistanceSimulator
AAAAAAAAHPAAAAAAAAHP
Contrôleur pour la simulation de résistance via MUX.
Graphe de collaboration de app.resistance_simulation.ResistanceSimulator:
IMAGE

Fonctions membres publiques
__init__ (self, int speed_hz=100000)
Initialise le simulateur de résistance.

close (self)
Ferme les connexions du simulateur.

float calculate_parallel_resistance (self, List[float] resistances)
Calcule la résistance équivalente de résistances en parallèle.

bool apply_resistance_simulation (self, float target_resistance, int measurement_channel, str sensor_type="Ni1000 TK5000")
Applique une résistance simulée via le MUX sur le canal de mesure.

Dict[str, any] get_current_simulation (self)
Retourne l'état actuel de la simulation.

bool validate_resistance_applied (self, float expected_resistance, float tolerance=0.10)
Valide que la résistance appliquée correspond à l'attendu.

reset_simulation (self)
Remet la simulation à zéro (désactive tous les canaux).

Attributs publics
mux = None
speed_hz = speed_hz
current_resistance = None
list active_channels = []

Description détaillée
Contrôleur pour la simulation de résistance via MUX.
Classe principale qui encapsule toute la logique de simulation de résistance en utilisant le multiplexeur ADG731 et les mappings de résistances calibrées.

AAAAAAAAHQAAAAAAAAHQDocumentation des constructeurs et destructeur
app.resistance_simulation.ResistanceSimulator.__init__ ( self, int speed_hz = 100000)
AAAAAAAAHRAAAAAAAAHR
Initialise le simulateur de résistance.
Constructeur qui configure le multiplexeur ADG731 avec la vitesse SPI spécifiée et initialise les variables d'état du simulateur.
Paramètres
speed_hz | Vitesse de communication SPI en Hz (défaut: 100kHz).
Exceptions ResistanceSimulationError | si l'initialisation du MUX échoue.

AAAAAAAAHSAAAAAAAAHSDocumentation des fonctions membres
bool app.resistance_simulation.ResistanceSimulator.apply_resistance_simulation ( self, float target_resistance, int measurement_channel, str sensor_type = "Ni1000 TK5000")
AAAAAAAAHTAAAAAAAAHT
Applique une résistance simulée via le MUX sur le canal de mesure.
Fonction principale qui recherche le canal MUX optimal pour simuler la résistance cible, configure le multiplexeur et mémorise l'état de la simulation.
Paramètres
target_resistance | Résistance à simuler [Ohms].
measurement_channel | Canal sur lequel la mesure a été faite (info).
sensor_type | Type de sonde pour sélectionner la carte MUX.
Renvoie True si succès, False en cas d'erreur.
float app.resistance_simulation.ResistanceSimulator.calculate_parallel_resistance ( self, List[float] resistances)
AAAAAAAAHUAAAAAAAAHU
Calcule la résistance équivalente de résistances en parallèle.
Applique la formule 1/Req = 1/R1 + 1/R2 + ... + 1/Rn pour calculer la résistance équivalente d'un ensemble de résistances connectées en parallèle.
Paramètres
resistances | Liste des valeurs de résistance en parallèle [Ohms].
Renvoie Résistance équivalente calculée [Ohms]. Retourne l'infini si la liste est vide.
app.resistance_simulation.ResistanceSimulator.close ( self)
AAAAAAAAHVAAAAAAAAHV
Ferme les connexions du simulateur.
Méthode de nettoyage qui ferme proprement la connexion SPI avec le multiplexeur et libère les ressources.
Voici le graphe d'appel pour cette fonction :
IMAGE
Voici le graphe des appelants de cette fonction :
IMAGE
Dict[str, any] app.resistance_simulation.ResistanceSimulator.get_current_simulation ( self)
AAAAAAAAHWAAAAAAAAHW
Retourne l'état actuel de la simulation.
Fonction d'interrogation qui fournit un dictionnaire contenant toutes les informations sur l'état actuel de la simulation de résistance.
Renvoie
Dictionnaire contenant les informations actuelles:
▪ esistance: valeur appliquée [Ohms] ou None
▪ ctive_channels: liste des canaux MUX actifs
▪ ux_available: disponibilité du multiplexeur
app.resistance_simulation.ResistanceSimulator.reset_simulation ( self)
AAAAAAAAHXAAAAAAAAHX
Remet la simulation à zéro (désactive tous les canaux).
Procédure de nettoyage qui désactive tous les canaux de tous les multiplexeurs et remet l'état de simulation à sa configuration initiale.
bool app.resistance_simulation.ResistanceSimulator.validate_resistance_applied ( self, float expected_resistance, float tolerance = 0.10)
AAAAAAAAHYAAAAAAAAHY
Valide que la résistance appliquée correspond à l'attendu.
Fonction de validation qui compare la résistance actuellement appliquée avec la valeur attendue en tenant compte d'une tolérance relative spécifiée.
Paramètres
expected_resistance | Résistance attendue pour la validation [Ohms].
tolerance | Tolérance relative acceptée (défaut: 10%).
Renvoie True si la résistance est dans la tolérance.

AAAAAAAAHZAAAAAAAAHZDocumentation des données membres
list app.resistance_simulation.ResistanceSimulator.active_channels = []
AAAAAAAAIAAAAAAAAAIAapp.resistance_simulation.ResistanceSimulator.current_resistance = None
AAAAAAAAIBAAAAAAAAIBapp.resistance_simulation.ResistanceSimulator.mux = None
AAAAAAAAICAAAAAAAAICapp.resistance_simulation.ResistanceSimulator.speed_hz = speed_hz
AAAAAAAAIDAAAAAAAAID
La documentation de cette classe a été générée à partir du fichier suivant :
C:/Users/thebi/Documents/2510_RegulationChauffage/doc/9.SoftWare/Doxygen/src/app/resistance_simulation.py

Référence de la classe app.hw_tmux1204.Tmux1204
AAAAAAAAELAAAAAAAAEL
Pilote pour le multiplexeur TMUX1204.
Graphe de collaboration de app.hw_tmux1204.Tmux1204:
IMAGE

Fonctions membres publiques
__init__ (self)
Initialise le pilote TMUX1204.

close (self)
Ferme les interfaces GPIO.

set_bits (self, bit_a1, bit_a0)
Définit les bits de contrôle A1 et A0.

select_rref_ohm (self, rref_ohm)
Sélectionne la résistance de référence Rref.

Attributs publics
gpio_a1 = GPIO(GPIO_CHIP_PATH, ADC_A1, "out")
gpio_a0 = GPIO(GPIO_CHIP_PATH, ADC_A0, "out")

Description détaillée
Pilote pour le multiplexeur TMUX1204.
Classe pour gérer la sélection de résistance de référence via le multiplexeur TMUX1204. Utilise deux signaux de contrôle (A1, A0) pour sélectionner parmi quatre valeurs de Rref selon la table de vérité :
• 1=0, A0=0 : 2.2k ohms
• 1=0, A0=1 : 2.7k ohms
• 1=1, A0=0 : 10k ohms
• 1=1, A0=1 : 100k ohms

AAAAAAAAEMAAAAAAAAEMDocumentation des constructeurs et destructeur
app.hw_tmux1204.Tmux1204.__init__ ( self)
AAAAAAAAENAAAAAAAAEN
Initialise le pilote TMUX1204.
Configure les GPIO pour les signaux de contrôle A1 et A0 en mode sortie. Utilise les constantes matérielles définies dans le module pins_cm5.

AAAAAAAAEOAAAAAAAAEODocumentation des fonctions membres
app.hw_tmux1204.Tmux1204.close ( self)
AAAAAAAAEPAAAAAAAAEP
Ferme les interfaces GPIO.
Ferme proprement les GPIO A1 et A0 pour libérer les ressources système. Gère les erreurs de fermeture pour éviter les exceptions lors du nettoyage.
Voici le graphe d'appel pour cette fonction :
IMAGE
Voici le graphe des appelants de cette fonction :
IMAGE
app.hw_tmux1204.Tmux1204.select_rref_ohm ( self, rref_ohm)
AAAAAAAAEQAAAAAAAAEQ
Sélectionne la résistance de référence Rref.
Configure les signaux de contrôle selon la table de vérité pour sélectionner la résistance de référence demandée. Supporte quatre valeurs fixes : 2200, 2700, 10000, 100000 ohms.
Paramètres
rref_ohm | Valeur de résistance de référence en ohms.
Exceptions ValueError | Si la valeur de Rref n'est pas supportée.
Note Table de vérité TMUX1204 :
▪ 200 ohms : A1=0, A0=0
▪ 700 ohms : A1=0, A0=1
▪ 0000 ohms : A1=1, A0=0
▪ 00000 ohms: A1=1, A0=1
Voici le graphe d'appel pour cette fonction :
IMAGE
app.hw_tmux1204.Tmux1204.set_bits ( self, bit_a1, bit_a0)
AAAAAAAAERAAAAAAAAER
Définit les bits de contrôle A1 et A0.
Applique les niveaux logiques sur les signaux de contrôle du multiplexeur. Convertit les valeurs numériques (0/1) en niveaux logiques GPIO (False/True).
Paramètres
bit_a1 | Valeur du bit A1 (0 ou 1).
bit_a0 | Valeur du bit A0 (0 ou 1).
Voici le graphe des appelants de cette fonction :
IMAGE

AAAAAAAAESAAAAAAAAESDocumentation des données membres
app.hw_tmux1204.Tmux1204.gpio_a0 = GPIO(GPIO_CHIP_PATH, ADC_A0, "out")
AAAAAAAAETAAAAAAAAETapp.hw_tmux1204.Tmux1204.gpio_a1 = GPIO(GPIO_CHIP_PATH, ADC_A1, "out")
AAAAAAAAEUAAAAAAAAEU
La documentation de cette classe a été générée à partir du fichier suivant :
C:/Users/thebi/Documents/2510_RegulationChauffage/doc/9.SoftWare/Doxygen/src/app/hw_tmux1204.py

Documentation des fichiers
Référence du fichier C:/Users/thebi/Documents/2510_RegulationChauffage/doc/9.SoftWare/Doxygen/src/app/__init__.py
AAAAAAAAABAAAAAAAAABEspaces de nommage
namespace app

Référence du fichier C:/Users/thebi/Documents/2510_RegulationChauffage/doc/9.SoftWare/Doxygen/src/config_module/__init__.py
AAAAAAAAACAAAAAAAAACEspaces de nommage
namespace config_module

Référence du fichier C:/Users/thebi/Documents/2510_RegulationChauffage/doc/9.SoftWare/Doxygen/src/webui/__init__.py
AAAAAAAAADAAAAAAAAADEspaces de nommage
namespace webui

Référence du fichier C:/Users/thebi/Documents/2510_RegulationChauffage/doc/9.SoftWare/Doxygen/src/app/adc_ads124s08.py
AAAAAAAAAEAAAAAAAAAE
Driver pour l'ADC ADS124S08 avec communication SPI.
Classes
class app.adc_ads124s08.Ads124s08Driver pour l'ADC ADS124S08 avec interface SPI.
Espaces de nommage
namespace app
namespace app.adc_ads124s08
Fonctions
app.adc_ads124s08.encode_gain (pga_gain)
Encode le gain PGA en code binaire pour le registre.

app.adc_ads124s08.encode_idac_uA (idac_uA)
Encode la magnitude IDAC en code binaire pour le registre.

app.adc_ads124s08.sign_extend_24 (b0, b1, b2)
Étend le signe d'un code ADC 24 bits vers 32 bits.

Variables
int app.adc_ads124s08.REG_ID = 0x00
int app.adc_ads124s08.REG_STATUS = 0x01
int app.adc_ads124s08.REG_INPMUX = 0x02
int app.adc_ads124s08.REG_PGA = 0x03
int app.adc_ads124s08.REG_DATARATE = 0x04
int app.adc_ads124s08.REG_REF = 0x05
int app.adc_ads124s08.REG_IDACMUX = 0x07
int app.adc_ads124s08.REG_SYS = 0x09
int app.adc_ads124s08.REG_IDACMAG = 0x06
int app.adc_ads124s08.CMD_RESET = 0x06
int app.adc_ads124s08.CMD_START = 0x08
int app.adc_ads124s08.CMD_STOP = 0x0A
int app.adc_ads124s08.CMD_RDATA = 0x12
tuple app.adc_ads124s08.FS = (1 << 23) - 1
dict app.adc_ads124s08.CHANNELS

Description détaillée
Driver pour l'ADC ADS124S08 avec communication SPI.
Ce module fournit une interface complÃ¨te pour la communication avec l'ADC ADS124S08 via SPI en mode 1.0. Supporte la mesure de rÃ©sistance et tempÃ©rature avec configuration automatique des registres. SÃ Reset â†’ Configuration â†’ Mesure bloquante avec DRDY.
Auteur
Léo Mendes @project 2510_RegulationsChauffage @Mandant Oblo_solution
Date
2025-09-18
Version
1.0.0
Copyright
Copyright (c) 2025

Référence du fichier C:/Users/thebi/Documents/2510_RegulationChauffage/doc/9.SoftWare/Doxygen/src/app/api_client.py
AAAAAAAAAFAAAAAAAAAF
Client API pour les services oblosolutions.ch.
Classes
class app.api_client.ApiErrorException pour les erreurs d'API.
class app.api_client.ApiClientClient pour interroger les APIs oblosolutions.ch.
Espaces de nommage
namespace app
namespace app.api_client
Fonctions
Dict[str, Any] app.api_client.get_simulation_data (str mac_address)
Récupère les données de simulation depuis les APIs.

bool app.api_client.send_temperature_measurement (str mac_address, float temperature, int channel=None)
Envoie une mesure de température vers l'API.

Variables
int app.api_client.REQUEST_TIMEOUT = 10
int app.api_client.MAX_RETRIES = 3
int app.api_client.RETRY_DELAY = 1
str app.api_client.test_mac = "0030DEABCDEF"
Dict[str, Any] app.api_client.data = get_simulation_data(test_mac)

Description détaillée
Client API pour les services oblosolutions.ch.
Ce module fournit un client HTTP pour interroger les APIs td25_param et td25_forecast. Il gère les timeouts, les retries automatiques et les erreurs de réseau. Inclut des fonctions utilitaires pour récupérer les données de simulation et envoyer les mesures de température.
Auteur
Léo Mendes @project 2510_RegulationsChauffage @Mandant Oblo_solution
Date
2025-09-18
Version
1.0.0
Copyright
Copyright (c) 2025

Référence du fichier C:/Users/thebi/Documents/2510_RegulationChauffage/doc/9.SoftWare/Doxygen/src/app/config_loader.py
AAAAAAAAAGAAAAAAAAAG
Chargeur de configuration JSON pour le système de mesure.
Espaces de nommage
namespace app
namespace app.config_loader
Fonctions
app.config_loader.load_config (path)

Description détaillée
Chargeur de configuration JSON pour le système de mesure.
Ce module fournit une fonction simple pour charger et parser un fichier de configuration JSON contenant les paramètres des capteurs, timeouts et autres paramètres système.
Auteur
Léo Mendes @project 2510_RegulationsChauffage @Mandant Oblo_solution
Date
2025-09-18
Version
1.0.0
Copyright
Copyright (c) 2025

Référence du fichier C:/Users/thebi/Documents/2510_RegulationChauffage/doc/9.SoftWare/Doxygen/src/app/front_led_management.py
AAAAAAAAAHAAAAAAAAAH
Gestionnaire de LED frontale avec patterns d'erreur.
Classes
class app.front_led_management.LedErrorIndicatorGestionnaire de LED avec patterns d'erreur.
Espaces de nommage
namespace app
namespace app.front_led_management
Fonctions
app.front_led_management.create_led_indicator (gpio_chip_path, led_pin)
Factory function pour créer une instance LedErrorIndicator.

Description détaillée
Gestionnaire de LED frontale avec patterns d'erreur.
Ce module fournit une classe pour gérer les clignotements et états de la LED frontale avec différents patterns d'erreur. Supporte les modes continus, les clignotements d'erreur et la gestion thread-safe des patterns LED.
Auteur
Léo Mendes @project 2510_RegulationsChauffage @Mandant Oblo_solution
Date
2025-09-18
Version
1.0.0
Copyright
Copyright (c) 2025

Référence du fichier C:/Users/thebi/Documents/2510_RegulationChauffage/doc/9.SoftWare/Doxygen/src/app/hw_mux_adg731.py
AAAAAAAAAIAAAAAAAAAI
Pilote pour multiplexeur ADG731 via interface SPI.
Classes
class app.hw_mux_adg731.Adg731MuxSpiPilote SPI pour multiplexeurs ADG731.
Espaces de nommage
namespace app
namespace app.hw_mux_adg731
Fonctions
app.hw_mux_adg731.adg731_ctrl_byte (address, enable=True)
Génère le byte de contrôle pour l'ADG731.

Description détaillée
Pilote pour multiplexeur ADG731 via interface SPI.
Ce module fournit un pilote pour contrôler les multiplexeurs ADG731 via l'interface SPI0. Supporte jusqu'à 4 cartes avec 32 canaux chacune. Gère la configuration SPI et l'envoi des commandes de contrôle pour la sélection des canaux.
Auteur
Léo Mendes @project 2510_RegulationsChauffage @Mandant Oblo_solution
Date
2025-09-18
Version
1.0.0
Copyright
Copyright (c) 2025

Référence du fichier C:/Users/thebi/Documents/2510_RegulationChauffage/doc/9.SoftWare/Doxygen/src/app/hw_tmux1204.py
AAAAAAAAAJAAAAAAAAAJ
Pilote pour multiplexeur TMUX1204 de sélection de résistance de référence.
Classes
class app.hw_tmux1204.Tmux1204Pilote pour le multiplexeur TMUX1204.
Espaces de nommage
namespace app
namespace app.hw_tmux1204

Description détaillée
Pilote pour multiplexeur TMUX1204 de sélection de résistance de référence.
Ce module fournit un pilote pour contrôler le multiplexeur TMUX1204 via les signaux de contrôle ADC_A1 et ADC_A0. Permet la sélection de quatre valeurs de résistance de référence (2.2k, 2.7k, 10k, 100k) selon une table de vérité définie.
Auteur
Léo Mendes @project 2510_RegulationsChauffage @Mandant Oblo_solution
Date
2025-09-18
Version
1.0.0
Copyright
Copyright (c) 2025

Référence du fichier C:/Users/thebi/Documents/2510_RegulationChauffage/doc/9.SoftWare/Doxygen/src/app/main.py
AAAAAAAAAKAAAAAAAAAK
Système de mesure et simulation de température.
Espaces de nommage
namespace app
namespace app.main
Fonctions
app.main.start_webui_server ()
Lance le serveur web local dans un thread séparé.

app.main.save_last_state (channel=None, resistance_ohm=None, temperature_c=None, temperature_sim_c=None, error=None)
Sauvegarde l'état courant et historique par canal dans un fichier JSON.

app.main.signal_handler (sig, frame)
Gestionnaire POSIX pour les signaux (Ctrl+C).

app.main.input_monitor ()
Thread d'écoute des commandes utilisateur depuis stdin.

app.main.show_error_and_continue (error_pattern, sleep_time=2)
Affiche un motif LED d'erreur pendant un temps donné puis remet l'indicateur en mode 'sequence_running'.

app.main.run_measurement_sequence (cfg, mac_address, adc, tmux)
Exécute une séquence complète de mesures pour tous les canaux activés selon la configuration fournie.

app.main.reload_timing_config ()
Recharge les paramètres de temporisation depuis le fichier de configuration.

app.main.main ()
Point d'entrée principal du programme.

Variables
app.main.CURRENT_DIR = os.path.dirname(os.path.abspath(__file__))
app.main.SRC_DIR = os.path.dirname(CURRENT_DIR)
bool app.main.sequencer_running = False
app.main.stop_event = threading.Event()
app.main.force_sequence = threading.Event()
app.main.led_indicator = None

Description détaillée
Système de mesure et simulation de température.
Ce module exécute des cycles de mesure ADC, convertit les valeurs en résistances puis en températures, récupère des paramètres via une API distante, calcule une température simulée, convertit cette température en résistance cible et applique la simulation via un multiplexeur matériel. Le module gère également un petit serveur web optionnel et un indicateur LED.
Auteur
Léo Mendes @project 2510_RegulationsChauffage @Mandant Oblo_solution
Date
2025-09-18
Version
1.0.0
Copyright
Copyright (c) 2025

Référence du fichier C:/Users/thebi/Documents/2510_RegulationChauffage/doc/9.SoftWare/Doxygen/src/app/mesure_24v_dry_contact.py
AAAAAAAAALAAAAAAAAAL
Module de test des entrées/sorties 24V pour contacts secs.
Espaces de nommage
namespace app
namespace app.mesure_24v_dry_contact
Fonctions
app.mesure_24v_dry_contact.test_24v_dry_contact ()
Test des contacts secs I/O 24V.

app.mesure_24v_dry_contact.get_dry_contact_status ()
Retourne l'état actuel des contacts secs.

Variables
int app.mesure_24v_dry_contact.CM_24V_OUT_1 = 13
int app.mesure_24v_dry_contact.CM_24V_SENSE_1 = 14
int app.mesure_24v_dry_contact.CM_24V_OUT_2 = 15
int app.mesure_24v_dry_contact.CM_24V_SENSE_2 = 16
int app.mesure_24v_dry_contact.io_24v_ch1_ok = 0
int app.mesure_24v_dry_contact.io_24v_ch2_ok = 0

Description détaillée
Module de test des entrées/sorties 24V pour contacts secs.
Ce module fournit des fonctions pour tester et valider les contacts secs via les interfaces I/O 24V. Permet de détecter l'état des contacts (ouvert/fermé) sur deux canaux indépendants avec gestion des GPIO et temporisations appropriées.
Auteur
Léo Mendes @project 2510_RegulationsChauffage @Mandant Oblo_solution
Date
2025-09-18
Version
1.0.0
Copyright
Copyright (c) 2025

Référence du fichier C:/Users/thebi/Documents/2510_RegulationChauffage/doc/9.SoftWare/Doxygen/src/app/pins_cm5.py
AAAAAAAAAMAAAAAAAAAM
Mapping GPIO et SPI fixés pour la plateforme CM5.
Espaces de nommage
namespace app
namespace app.pins_cm5
Variables
str app.pins_cm5.GPIO_CHIP_PATH = "/dev/gpiochip0"
int app.pins_cm5.MUX_CS_4 = 2
int app.pins_cm5.MUX_CS_3 = 3
int app.pins_cm5.MUX_CS_2 = 7
int app.pins_cm5.MUX_CS_1 = 8
int app.pins_cm5.MUX_MOSI_DUMMY = 10
int app.pins_cm5.MUX_SCLK_DUMMY = 11
int app.pins_cm5.CM_24V_OUT_1 = 13
int app.pins_cm5.CM_24V_SENSE_1 = 14
int app.pins_cm5.CM_24V_OUT_2 = 15
int app.pins_cm5.CM_24V_SENSE_2 = 16
int app.pins_cm5.CMD_RELAY = 17
int app.pins_cm5.CS_ADC_DUMMY = 18
int app.pins_cm5.SPI_MISO_ADC_DMY = 19
int app.pins_cm5.SPI_MOSI_ADC_DMY = 20
int app.pins_cm5.SPI_SCLK_ADC_DMY = 21
int app.pins_cm5.ADC_DRDY = 22
int app.pins_cm5.ADC_START_SYNC = 23
int app.pins_cm5.ADC_A0 = 24
int app.pins_cm5.ADC_A1 = 25
int app.pins_cm5.FRONT_LED = 27
int app.pins_cm5.SPI0_BUS = 0
int app.pins_cm5.SPI1_BUS = 1
int app.pins_cm5.SPI0_DEV0 = 0
int app.pins_cm5.SPI0_DEV1 = 1
int app.pins_cm5.SPI1_DEV0 = 0
int app.pins_cm5.SPI_MUX_SPEED_HZ = 100000
int app.pins_cm5.SPI_ADC_SPEED_HZ = 100000

Description détaillée
Mapping GPIO et SPI fixés pour la plateforme CM5.
Ce module définit tous les assignements de broches GPIO et les paramètres SPI fixes pour la carte CM5. Ces constantes ne doivent pas être modifiées via la configuration utilisateur car elles correspondent au routage matériel de la carte.
Auteur
Léo Mendes @project 2510_RegulationsChauffage @Mandant Oblo_solution
Date
2025-09-18
Version
1.0.0
Copyright
Copyright (c) 2025

Référence du fichier C:/Users/thebi/Documents/2510_RegulationChauffage/doc/9.SoftWare/Doxygen/src/app/resistance_mapping.py
AAAAAAAAANAAAAAAAAAN
Mapping des résistances TMUX par type de sonde de température.
Espaces de nommage
namespace app
namespace app.resistance_mapping
Fonctions
dict app.resistance_mapping.get_channel_mux_map (str sensor_type)
Retourne le mapping CHANNEL_MUX pour un type de sonde donné.

tuple app.resistance_mapping.find_closest_channel (float target_resistance, str sensor_type)
Trouve le canal MUX le plus proche pour une résistance cible.

Variables
dict app.resistance_mapping.CHANNEL_MUX

Description détaillée
Mapping des résistances TMUX par type de sonde de température.
Ce module fournit les tables de correspondance entre les canaux 0-31 du multiplexeur TMUX et les valeurs de résistance réelles pour différents types de sondes de température. Chaque type de sonde dispose d'un mapping spécifique avec 32 valeurs calibrées.
Auteur
Léo Mendes @project 2510_RegulationsChauffage @Mandant Oblo_solution
Date
2025-09-18
Version
1.0.0
Copyright
Copyright (c) 2025

Référence du fichier C:/Users/thebi/Documents/2510_RegulationChauffage/doc/9.SoftWare/Doxygen/src/app/resistance_simulation.py
AAAAAAAAAOAAAAAAAAAO
Module pour commander le MUX de simulation de résistance.
Classes
class app.resistance_simulation.ResistanceSimulationErrorException pour les erreurs de simulation de résistance.
class app.resistance_simulation.ResistanceSimulatorContrôleur pour la simulation de résistance via MUX.
Espaces de nommage
namespace app
namespace app.resistance_simulation
Fonctions
bool app.resistance_simulation.apply_resistance_simulation (float resistance_ohm)
Fonction utilitaire pour appliquer une résistance simulée.

Variables
app.resistance_simulation.sim = ResistanceSimulator()
bool app.resistance_simulation.success = sim.apply_resistance_simulation(1000.0)
app.resistance_simulation.valid = sim.validate_resistance_applied(667.0, tolerance=0.15)

Description détaillée
Module pour commander le MUX de simulation de résistance.
Ce module permet d'appliquer une résistance simulée R_sim via le réseau de résistances contrôlé par multiplexeur ADG731. Il gère le calcul des commutateurs à activer, la commande du multiplexeur, et la validation des valeurs appliquées.
Auteur
Léo Mendes @project 2510_RegulationsChauffage @Mandant Oblo_solution
Date
2025-09-18
Version
1.0.0
Copyright
Copyright (c) 2025

Référence du fichier C:/Users/thebi/Documents/2510_RegulationChauffage/doc/9.SoftWare/Doxygen/src/app/sensor_profiles.py
AAAAAAAAAPAAAAAAAAAP
Profils capteurs extraits de 'Calcul ADC.xlsx' (Feuil1).
Espaces de nommage
namespace app
namespace app.sensor_profiles
Fonctions
app.sensor_profiles.get_profile (sensor_name)
Récupère le profil de configuration ADC pour un capteur donné.

Variables
dict app.sensor_profiles.SENSOR_PROFILES

Description détaillée
Profils capteurs extraits de 'Calcul ADC.xlsx' (Feuil1).
Ce module contient les profils de configuration pour différents types de capteurs de température avec leurs paramètres ADC optimisés (Rref, IDAC, PGA) et leurs tables de conversion température/résistance. Les données proviennent des calculs d'optimisation du fichier Excel de référence.
Auteur
Léo Mendes @project 2510_RegulationsChauffage @Mandant Oblo_solution
Date
2025-09-18
Version
1.0.0
Copyright
Copyright (c) 2025

Référence du fichier C:/Users/thebi/Documents/2510_RegulationChauffage/doc/9.SoftWare/Doxygen/src/app/temperature_conversion.py
AAAAAAAAAQAAAAAAAAAQ
Module de conversion résistance/température via interpolation linéaire.
Espaces de nommage
namespace app
namespace app.temperature_conversion
Fonctions
app.temperature_conversion.resistance_to_temperature (resistance, table)
Convertit une résistance mesurée en température via interpolation linéaire.

app.temperature_conversion.resistance_to_temperature_dynamic (resistance, sensor)
Convertit une résistance mesurée en température pour un capteur donné.

app.temperature_conversion.temperature_to_resistance_dynamic (temperature, sensor)
Convertit une température en résistance pour un capteur donné (conversion inverse).

app.temperature_conversion.convert_temperature_to_resistance (temperature, probe_type)
Fonction de conversion principale pour la simulation de résistance.

app.temperature_conversion.get_supported_probe_types ()
Retourne la liste des types de sondes supportés.

app.temperature_conversion.validate_temperature_range (temperature, probe_type)
Valide si une température est dans la plage supportée par une sonde.

Description détaillée
Module de conversion résistance/température via interpolation linéaire.
Ce module fournit les fonctions de conversion bidirectionnelle entre résistance mesurée et température pour différents types de capteurs. Utilise l'interpolation linéaire sur les tables de calibration et supporte la conversion inverse pour la simulation de résistance.
Auteur
Léo Mendes @project 2510_RegulationsChauffage @Mandant Oblo_solution
Date
2025-09-18
Version
1.0.0
Copyright
Copyright (c) 2025

Référence du fichier C:/Users/thebi/Documents/2510_RegulationChauffage/doc/9.SoftWare/Doxygen/src/app/temperature_simulation.py
AAAAAAAAARAAAAAAAAAR
Module de calcul de température simulée selon formule prédictive.
Espaces de nommage
namespace app
namespace app.temperature_simulation
Fonctions
Optional[float] app.temperature_simulation.calculate_simulated_temperature (float t_mes, float t_prev, float n, float k_m)
Calcule la température simulée selon la formule prédictive.

bool app.temperature_simulation.validate_simulation_parameters (str probe_type, float n, float k_m, float t_mes, float t_prev)
Valide tous les paramètres de simulation avant exécution.

Optional[float] app.temperature_simulation.run_temperature_simulation (dict simulation_data)
Exécute une simulation complète de température avec dictionnaire.

Description détaillée
Module de calcul de température simulée selon formule prédictive.
Ce module implémente la formule de simulation de température:
T_sim = T_mes + ((T_prev - T_mes) * n * exp(k_m))
Inclut la validation complète des paramètres, la gestion des erreurs numériques et l'exécution de simulations complètes.
Auteur
Léo Mendes @project 2510_RegulationsChauffage @Mandant Oblo_solution
Date
2025-09-18
Version
1.0.0
Copyright
Copyright (c) 2025

Référence du fichier C:/Users/thebi/Documents/2510_RegulationChauffage/doc/9.SoftWare/Doxygen/src/app/test_lm70_compatible.py
AAAAAAAAASAAAAAAAAASEspaces de nommage
namespace app
namespace app.test_lm70_compatible
Fonctions
app.test_lm70_compatible.test_lm70 ()
Test de communication SPI avec le capteur LM70.

Variables
app.test_lm70_compatible.levelapp.test_lm70_compatible.format
app.test_lm70_compatible.handlers
app.test_lm70_compatible.logger = logging.getLogger("LM70-Test")
int app.test_lm70_compatible.LM70_CS_GPIO = 18
int app.test_lm70_compatible.SPI_MOSI_ADC_GPIO = 20
int app.test_lm70_compatible.SPI_MISO_ADC_GPIO = 19
int app.test_lm70_compatible.SPI_SCLK_ADC_GPIO = 21
app.test_lm70_compatible.current_dir = os.path.dirname(os.path.abspath(__file__))
str app.test_lm70_compatible.src_dir = os.path.dirname(current_dir) if "src" in current_dir else current_dir
app.test_lm70_compatible.spi = spidev.SpiDev()
app.test_lm70_compatible.max_speed_hz
app.test_lm70_compatible.mode
app.test_lm70_compatible.bits_per_word

Référence du fichier C:/Users/thebi/Documents/2510_RegulationChauffage/doc/9.SoftWare/Doxygen/src/app/test_spi_adc.py
AAAAAAAAATAAAAAAAAATEspaces de nommage
namespace app
namespace app.test_spi_adc
Fonctions
app.test_spi_adc.test_spi_adc ()

Référence du fichier C:/Users/thebi/Documents/2510_RegulationChauffage/doc/9.SoftWare/Doxygen/src/config_module/cm5_config.py
AAAAAAAAAUAAAAAAAAAU
Configuration matérielle pour plateforme CM5.
Espaces de nommage
namespace config_module
namespace config_module.cm5_config
Fonctions
config_module.cm5_config.build_hw ()
Initialise et configure tout le matériel CM5.

Variables
list config_module.cm5_config.ADC_CHANNELS = [1, 2, 3, 4]

Description détaillée
Configuration matérielle pour plateforme CM5.
Ce module fournit la configuration des canaux ADC et la fonction d'initialisation complète du matériel (LED, TMUX, ADC). Centralise la création des instances matérielles avec câblage fixe CM5.
Auteur
Léo Mendes @project 2510_RegulationsChauffage @Mandant Oblo_solution
Date
2025-09-18
Version
1.0.0
Copyright
Copyright (c) 2025

Référence du fichier C:/Users/thebi/Documents/2510_RegulationChauffage/doc/9.SoftWare/Doxygen/src/webui/webui_server.py
AAAAAAAAAVAAAAAAAAAV
Serveur web pour interface utilisateur de configuration.
Espaces de nommage
namespace webui
namespace webui.webui_server
Fonctions
webui.webui_server.serve_index ()
Sert la page principale de l'interface web.

webui.webui_server.get_config ()
Récupère la configuration actuelle des capteurs.

webui.webui_server.put_config ()
Sauvegarde une nouvelle configuration des capteurs.

webui.webui_server.get_last ()
Récupère le dernier état du système de mesure.

webui.webui_server.force_reload ()
Force le rechargement de la configuration au prochain cycle.

Variables
webui.webui_server.BASE_DIR = os.path.abspath(os.path.join(os.path.dirname(__file__), ".."))
webui.webui_server.CONFIG_PATH = os.path.join(BASE_DIR, "config_module", "sensors.json")
webui.webui_server.STATE_PATH = os.path.join(BASE_DIR, "state", "last_state.json")
webui.webui_server.WEBUI_DIR = os.path.dirname(__file__)
webui.webui_server.app = Flask(__name__, static_folder=WEBUI_DIR, static_url_path='/static')
webui.webui_server.host
webui.webui_server.port

Description détaillée
Serveur web pour interface utilisateur de configuration.
Interface web Flask monopage pour lecture/écriture de la configuration sensors.json et affichage de l'état last_state.json. Fournit API REST complète pour gestion configuration canaux et monitoring système.
Auteur
Léo Mendes @project 2510_RegulationsChauffage @Mandant Oblo_solution
Date
2025-09-18
Version
1.0.0
Copyright
Copyright (c) 2025

Exemples
C:/Users/thebi/Documents/2510_RegulationChauffage/doc/9.SoftWare/Doxygen/src/app/config_loader.py
AAAAAAAAAAAAAAAAAAAACharge un fichier de configuration JSON.
Charge un fichier de configuration JSON. Vérifie l'existence du fichier, l'ouvre en UTF-8 et parse le contenu JSON. Le format attendu inclut les timeouts, délais entre mesures et configuration des canaux de capteurs.
Paramètres
path | Chemin vers le fichier de configuration JSON.
Renvoie Dictionnaire Python contenant les données de configuration.
Exceptions
FileNotFoundError | Si le fichier n'existe pas.
json.JSONDecodeError | Si le fichier n'est pas un JSON valide.
Format JSON attendu: 1 {
2 "timeout_s": 180,
3 "inter_measure_sleep_s": 0.1,
4 "loop_sleep_s": 1.0,
5 "channels": [
6 { "channel": 1, "sensor": "Ni1000 TK5000" }
7 ]
8 }

1 # -*- coding: utf-8 -*-
2 """
3 @file config_loader.py
4 @brief Chargeur de configuration JSON pour le système de mesure.
5 @details Ce module fournit une fonction simple pour charger et parser
6 un fichier de configuration JSON contenant les paramètres
7 des capteurs, timeouts et autres paramètres système.
8 @author Léo Mendes
9 @project 2510_RegulationsChauffage
10 @Mandant Oblo_solution
11 @date 2025-09-18
12 @version 1.0.0
13 @copyright Copyright (c) 2025
14 """
15
16 from __future__ import annotations
17
18 # Sérialisation/désérialisation JSON
19 import json
20 # Opérations sur les chemins et fichiers
21 import os
22
23 # ---------------------------------------------------------------------------
24 # Fonctions utilitaires
25 # ---------------------------------------------------------------------------
26
27 def load_config(path):
28 """
29 @brief Charge un fichier de configuration JSON.
30 @details Vérifie l'existence du fichier, l'ouvre en UTF-8 et parse
31 le contenu JSON. Le format attendu inclut les timeouts,
32 délais entre mesures et configuration des canaux de capteurs.
33
34 @param path Chemin vers le fichier de configuration JSON.
35
36 @return Dictionnaire Python contenant les données de configuration.
37
38 @exception FileNotFoundError Si le fichier n'existe pas.
39 @exception json.JSONDecodeError Si le fichier n'est pas un JSON valide.
40
41 @example
42 Format JSON attendu:
43 {
44 "timeout_s": 180,
45 "inter_measure_sleep_s": 0.1,
46 "loop_sleep_s": 1.0,
47 "channels": [
48 { "channel": 1, "sensor": "Ni1000 TK5000" }
49 ]
50 }
51 """
52 # Vérification de l'existence du fichier
53 if os.path.exists(path) is False:
54 # Lever une exception si le fichier n'existe pas
55 raise FileNotFoundError("Config introuvable: " + str(path))
56 # Ouverture et lecture du fichier JSON
57 with open(path, "r", encoding="utf-8") as f:
58 # Parsing du contenu JSON
59 data = json.load(f)
60 # Retour des données parsées
61 return data

Index
INDEX
