LeoMendesEsEtml/2510_RegulationChauffage/doc/6.Graphique, Schéma/3.Doxygen/rtf/resistance__mapping_8py.rtf

begin bodyRÃ©fÃ©rence du fichier C:/Users/thebi/Documents/2510_RegulationChauffage/doc/9.SoftWare/Doxygen/src/app/resistance_mapping.py
AAAAAAAAANAAAAAAAAAN
Mapping des rÃ©sistances TMUX par type de sonde de tempÃ©rature.
Espaces de nommage
namespace app
namespace app.resistance_mapping
Fonctions
dict app.resistance_mapping.get_channel_mux_map (str sensor_type)
Retourne le mapping CHANNEL_MUX pour un type de sonde donnÃ©.

tuple app.resistance_mapping.find_closest_channel (float target_resistance, str sensor_type)
Trouve le canal MUX le plus proche pour une rÃ©sistance cible.

Variables
dict app.resistance_mapping.CHANNEL_MUX

Description dÃ©taillÃ©e
Mapping des rÃ©sistances TMUX par type de sonde de tempÃ©rature.
Ce module fournit les tables de correspondance entre les canaux 0-31 du multiplexeur TMUX et les valeurs de rÃ©sistance rÃ©elles pour diffÃ©rents types de sondes de tempÃ©rature. Chaque type de sonde dispose d'un mapping spÃ©cifique avec 32 valeurs calibrÃ©es.
Auteur
LÃ©o Mendes @project 2510_RegulationsChauffage @Mandant Oblo_solution
Date
2025-09-18
Version
1.0.0
Copyright
Copyright (c) 2025
