LeoMendesEsEtml/2510_RegulationChauffage/doc/6.Graphique, Schéma/3.Doxygen/rtf/resistance__simulation_8py.rtf

begin bodyRÃ©fÃ©rence du fichier C:/Users/thebi/Documents/2510_RegulationChauffage/doc/9.SoftWare/Doxygen/src/app/resistance_simulation.py
AAAAAAAAAOAAAAAAAAAO
Module pour commander le MUX de simulation de rÃ©sistance.
Classes
class app.resistance_simulation.ResistanceSimulationErrorException pour les erreurs de simulation de rÃ©sistance.
class app.resistance_simulation.ResistanceSimulatorContrÃ´leur pour la simulation de rÃ©sistance via MUX.
Espaces de nommage
namespace app
namespace app.resistance_simulation
Fonctions
bool app.resistance_simulation.apply_resistance_simulation (float resistance_ohm)
Fonction utilitaire pour appliquer une rÃ©sistance simulÃ©e.

Variables
app.resistance_simulation.sim = ResistanceSimulator()
bool app.resistance_simulation.success = sim.apply_resistance_simulation(1000.0)
app.resistance_simulation.valid = sim.validate_resistance_applied(667.0, tolerance=0.15)

Description dÃ©taillÃ©e
Module pour commander le MUX de simulation de rÃ©sistance.
Ce module permet d'appliquer une rÃ©sistance simulÃ©e R_sim via le rÃ©seau de rÃ©sistances contrÃ´lÃ© par multiplexeur ADG731. Il gÃ¨re le calcul des commutateurs Ã activer, la commande du multiplexeur, et la validation des valeurs appliquÃ©es.
Auteur
LÃ©o Mendes @project 2510_RegulationsChauffage @Mandant Oblo_solution
Date
2025-09-18
Version
1.0.0
Copyright
Copyright (c) 2025
