LeoMendesEsEtml/2510_RegulationChauffage/doc/6.Graphique, Schéma/3.Doxygen/rtf/sensor__profiles_8py.rtf

begin bodyRÃ©fÃ©rence du fichier C:/Users/thebi/Documents/2510_RegulationChauffage/doc/9.SoftWare/Doxygen/src/app/sensor_profiles.py
AAAAAAAAAPAAAAAAAAAP
Profils capteurs extraits de 'Calcul ADC.xlsx' (Feuil1).
Espaces de nommage
namespace app
namespace app.sensor_profiles
Fonctions
app.sensor_profiles.get_profile (sensor_name)
RÃ©cupÃ¨re le profil de configuration ADC pour un capteur donnÃ©.

Variables
dict app.sensor_profiles.SENSOR_PROFILES

Description dÃ©taillÃ©e
Profils capteurs extraits de 'Calcul ADC.xlsx' (Feuil1).
Ce module contient les profils de configuration pour diffÃ©rents types de capteurs de tempÃ©rature avec leurs paramÃ¨tres ADC optimisÃ©s (Rref, IDAC, PGA) et leurs tables de conversion tempÃ©rature/rÃ©sistance. Les donnÃ©es proviennent des calculs d'optimisation du fichier Excel de rÃ©fÃ©rence.
Auteur
LÃ©o Mendes @project 2510_RegulationsChauffage @Mandant Oblo_solution
Date
2025-09-18
Version
1.0.0
Copyright
Copyright (c) 2025
