LeoMendesEsEtml/2510_RegulationChauffage/doc/6.Graphique, Schéma/3.Doxygen/rtf/temperature__conversion_8py.rtf

begin bodyRÃ©fÃ©rence du fichier C:/Users/thebi/Documents/2510_RegulationChauffage/doc/9.SoftWare/Doxygen/src/app/temperature_conversion.py
AAAAAAAAAQAAAAAAAAAQ
Module de conversion rÃ©sistance/tempÃ©rature via interpolation linÃ©aire.
Espaces de nommage
namespace app
namespace app.temperature_conversion
Fonctions
app.temperature_conversion.resistance_to_temperature (resistance, table)
Convertit une rÃ©sistance mesurÃ©e en tempÃ©rature via interpolation linÃ©aire.

app.temperature_conversion.resistance_to_temperature_dynamic (resistance, sensor)
Convertit une rÃ©sistance mesurÃ©e en tempÃ©rature pour un capteur donnÃ©.

app.temperature_conversion.temperature_to_resistance_dynamic (temperature, sensor)
Convertit une tempÃ©rature en rÃ©sistance pour un capteur donnÃ© (conversion inverse).

app.temperature_conversion.convert_temperature_to_resistance (temperature, probe_type)
Fonction de conversion principale pour la simulation de rÃ©sistance.

app.temperature_conversion.get_supported_probe_types ()
Retourne la liste des types de sondes supportÃ©s.

app.temperature_conversion.validate_temperature_range (temperature, probe_type)
Valide si une tempÃ©rature est dans la plage supportÃ©e par une sonde.

Description dÃ©taillÃ©e
Module de conversion rÃ©sistance/tempÃ©rature via interpolation linÃ©aire.
Ce module fournit les fonctions de conversion bidirectionnelle entre rÃ©sistance mesurÃ©e et tempÃ©rature pour diffÃ©rents types de capteurs. Utilise l'interpolation linÃ©aire sur les tables de calibration et supporte la conversion inverse pour la simulation de rÃ©sistance.
Auteur
LÃ©o Mendes @project 2510_RegulationsChauffage @Mandant Oblo_solution
Date
2025-09-18
Version
1.0.0
Copyright
Copyright (c) 2025
