LeoMendesEsEtml/2510_RegulationChauffage/doc/6.Graphique, Schéma/3.Doxygen/rtf/temperature__simulation_8py.rtf

begin bodyRÃ©fÃ©rence du fichier C:/Users/thebi/Documents/2510_RegulationChauffage/doc/9.SoftWare/Doxygen/src/app/temperature_simulation.py
AAAAAAAAARAAAAAAAAAR
Module de calcul de tempÃ©rature simulÃ©e selon formule prÃ©dictive.
Espaces de nommage
namespace app
namespace app.temperature_simulation
Fonctions
Optional[float] app.temperature_simulation.calculate_simulated_temperature (float t_mes, float t_prev, float n, float k_m)
Calcule la tempÃ©rature simulÃ©e selon la formule prÃ©dictive.

bool app.temperature_simulation.validate_simulation_parameters (str probe_type, float n, float k_m, float t_mes, float t_prev)
Valide tous les paramÃ¨tres de simulation avant exÃ©cution.

Optional[float] app.temperature_simulation.run_temperature_simulation (dict simulation_data)
ExÃ©cute une simulation complÃ¨te de tempÃ©rature avec dictionnaire.

Description dÃ©taillÃ©e
Module de calcul de tempÃ©rature simulÃ©e selon formule prÃ©dictive.
Ce module implÃ©mente la formule de simulation de tempÃ©rature:
T_sim = T_mes + ((T_prev - T_mes) * n * exp(k_m))
Inclut la validation complÃ¨te des paramÃ¨tres, la gestion des erreurs numÃ©riques et l'exÃ©cution de simulations complÃ¨tes.
Auteur
LÃ©o Mendes @project 2510_RegulationsChauffage @Mandant Oblo_solution
Date
2025-09-18
Version
1.0.0
Copyright
Copyright (c) 2025
