LeoMendesEsEtml/2510_RegulationChauffage/doc/8.Calcul/Explications Fiches calculs ADC.pdf

ETML⁻ES | 2510 Régulation Chauffage
LMS | Page 33 Diplômes

### 3.3.4.12 Résultat :

La conversion fournie par l’ADC est un code numérique 24 bits signé.
Comme la mesure est ratiométrique, le résultat correspond directement au rapport entre la résistance de la sonde et la résistance de référence sélectionnée.

Formule :
Rsonde = (CodeADC / FullScale) × Rref

avec FullScale = 2^23 (valeur maximale pour 24 bits signé).

La présence du courant IDAC s’annule dans le rapport, car il traverse à la fois la sonde et la résistance de référence.

### 3.3.5 Fiche de calcul ADC

Pour valider le dimensionnement de l’ADC, j’ai établi une fiche de calcul permettant de vérifier les plages de mesure en fonction des paramètres configurables.

Les points de contrôle de la mesure sont les suivants :
- R à -15[°C]
o Description : résistance de la sonde à -15°C.
o Formule : valeur issue du CdC (non calculée).
o Limites : utiliser la valeur extrême avec tolérance si fournie.
- R à +40[°C]
o Description : résistance de la sonde à +40°C.
o Formule : valeur issue du CdC (non calculée).
o Limites : utiliser la valeur extrême avec tolérance si fournie.
- Rref [Ω]
o Description : résistance de référence connectée via le MUX au bloc REFP0/REFN0 de l’ADC.
o Formule : valeur matérielle (2.2k, 2.7k, 10k, 100k).
o Limites : Vref = IDAC × Rref doit rester entre 0.3 V et 2.5 V.
- IDAC [µA]
o Description : courant d’excitation fourni par l’ADC pour traverser la sonde et Rref. o Formule : valeur discrète parmi {10, 50, 100, 250, 750, 1000, 1500, 2000}.
o Limites : vérifier Vinj_max < AVDD − 0.4 V et limiter l’auto-échauffement (Psonde = I² × Rsonde).
- Gain
o Description : gain du PGA interne appliqué à la tension différentielle sonde.
o Formule : valeur programmée parmi {1, 2, 4, 8, 16, 32, 64, 128}.
o Limites : condition Vsonde_max < Vref / Gain.
- V @ Tmin mesurée [V]

LMS | Page 34

o Description : tension aux bornes de la sonde à -15°C. o Formule : Vsonde_min = IDAC × R(-15°C).
o Limites : doit être au-dessus du bruit ADC.
- V @ Tmax mesurée [V]
o Description : tension aux bornes de la sonde à +40°C. o Formule : Vsonde_max = IDAC × R(+40°C).
o Limites : doit rester < Vref / Gain.
- Vref [V]
o Description : tension de référence ratiométrique appliquée à l’ADC. o Formule : Vref = IDAC × Rref.
o Limites : 0.3 V ≤ Vref ≤ 2.5 V.
- Vnode max [V]
o Description : tension maximale au nœud d’injection IDAC (somme Vsonde_max + Vref).
o Formule : Vnode_max = Vsonde_max + Vref.
o Limites : doit être < AVDD − 0.4 V.
- FS_ADC
o Description : demi-pleine échelle effective du convertisseur après PGA. o Formule : FS_ADC = Vref / Gain.
o Limites : borne supérieure de la tension différentielle de la sonde.
- DV [V]
o Description : amplitude de variation de la tension sonde entre -15°C et +40°C. o Formule : DV = Vsonde_max − Vsonde_min.
o Limites : doit exploiter une part significative de FS_ADC.
- Dvout [V]
o Description : amplitude en sortie du PGA sur la plage de température. o Formule : Dvout = Gain × DV.
o Limites : doit rester < Vref pour ne pas saturer.
- Amplitude numérique [V]
o Description : amplitude équivalente en pleine échelle numérique après conversion. o Formule : Amplitude = (DV / FS_ADC) × Vref.
o Limites : cohérente avec l’échelle 2^23 codes.
- Utilisation de la plage ADC [%]
o Description : pourcentage de la pleine échelle utilisé par DV. o Formule : Utilisation = 100 × DV / FS_ADC.
o Limites : viser entre 60 % et 95 %.
- Résolution réelle en [°C]
o Description : variation de température correspondant à un code ADC. o Formule : Résolution = ΔT / Codes_DV avec ΔT = 46.5 °C.
o Limites : plus petit = meilleure résolution ; éviter > 0.001 °C/code.

LMS | Page 35
- Taux de variation numérique par [°C]
o Description : nombre de codes ADC par degré Celsius.
o Formule : Codes_par_°C = Codes_DV / ΔT avec ΔT = 46.5 °C.
o Limites : viser > 80 000 codes/°C pour assurer une bonne précision.
- P @ Tmin mesurée
o Description : puissance dissipée dans la sonde à -15°C.
o Formule : P = IDAC^2 × R(-15°C).
o Limites : doit rester faible pour éviter l’auto-échauffement.
- P @ Tmax mesurée
o Description : puissance dissipée dans la sonde à +40°C.
o Formule : P = IDAC^2 × R(+40°C).
o Limites : doit rester faible pour éviter l’auto-échauffement.
- Déviation min en [°C]/mW
o Description : élévation de température estimée par mW dissipé à -15°C. o Formule : ΔT/Pmin = valeur constructeur ou calculée.
o Limites : vérifier que l’élévation reste négligeable (<0.1°C).
- Déviation max en [°C]/mW
o Description : élévation de température estimée par mW dissipé à +40°C. o Formule : ΔT/Pmax = valeur constructeur ou calculée.
o Limites : vérifier que l’élévation reste négligeable (<0.1°C).
