LeoMendesEsEtml/2510_RegulationChauffage/doc/2.Document Annexe/PV/PV_28_08_2025_2510_RegulationChauffage_Mendes.pdf

PV de séance | diplôme

Ecole supérieure, école des métiers Lausanne
Rue de Sébeillon 12
CH-1004 Lausanne | www.etml.ch
PV_28_08_2025_2510_RegulationChauffage_Mendes.docx
| 1 / 2 |

## Procès-verbal du 28.08.2025

Léo Mendes
2510 - Régulation Chauffage

Présents

- M. Philippe Bovey
- M. Antonin Graf
- M. Léo Mendes

État des lieux

- Revue de correction de schéma (etages 24V-3V3, Testpoint, mesure ADC)
- Suivit projet
- Revue rapide du premier PCB fille

Problèmes rencontrés

Dernière revue du schéma :
- Le datasheet de l’ADC signale une perte de précision lors de l’utilisation du PGA (amplification du bruit). Vérifier que cette perte reste inférieure à l’exigence de 0.5 °C par bit.
- L’utilisation d’un connecteur 8 canaux peut accroître le risque d’erreur de branchement par les opérateurs.
- Positionner les canaux négatifs et positifs des sondes ainsi que ceux de la chaudière à proximité pour limiter la longueur de dénudage des câbles.
- Préparer une BOM pour 1 pièce et pour 100 pièces.

Conseils de routage PCB :
- La sérigraphie des connecteurs doit être placée à proximité immédiate pour faciliter la lecture.
- Prévoir le cheminement des câbles.
- Les résistances du réseau sur les cartes filles peuvent avoir des empreintes THT et SMD superposées, car un seul type de composant sera monté.
- Vérifier la stabilité mécanique des connecteurs verticaux du PCB.

Rapport :
- Décrire le fonctionnement des sondes.

Solutions proposées

- Utiliser des connecteurs Wago en 4 canaux afin de regrouper sonde +/− et chaudière +/− à proximité.
- Pour les connecteurs, vérifier l’ergonomie et la facilité de câblage pour limiter les erreurs d’installation.

ETML⁻ES

PV_28_08_2025_2510_RegulationChauffage_Mendes.docx | 02.09.2025 - page 2 / 2

Décisions prises.

- Effectuer la commande des composants.
- Envoyer les schémas et la BOM à Monsieur Graf.
- Avancer au maximum sur la rédaction du rapport.

Suite du projet / objectifs

- Finalisation du PCB pour mardi matin 02.09.2025
- Revue layout le mercredi 3.09.2025.

Prochaine réunion :

03.08.2025, 15 : 30, Présentiel – Revue PCB.

Destinataires de ce PV

- M. Philippe Bovey
- M. Antonin Graf
- M. Grégoire Rossier
- Mme Alice Ansermet

Lausanne le 31.08.2025

Léo Mendes
