LeoMendesEsEtml/2510_RegulationChauffage/doc/6.Graphique, Schéma/3.Doxygen/latex/config__loader_8py.tex

\doxysection{Référence du fichier C\+:/\+Users/thebi/\+Documents/2510\+\_\+\+Regulation\+Chauffage/doc/9.Soft\+Ware/\+Doxygen/src/app/config\+\_\+loader.py}
\hypertarget{config__loader_8py}{}\label{config__loader_8py}\index{C:/Users/thebi/Documents/2510\_RegulationChauffage/doc/9.SoftWare/Doxygen/src/app/config\_loader.py@{C:/Users/thebi/Documents/2510\_RegulationChauffage/doc/9.SoftWare/Doxygen/src/app/config\_loader.py}}

Chargeur de configuration JSON pour le système de mesure.  

\doxysubsubsection*{Espaces de nommage}
\begin{DoxyCompactItemize}
\item 
namespace \mbox{\hyperlink{namespaceapp}{app}}
\item 
namespace \mbox{\hyperlink{namespaceapp_1_1config__loader}{app.\+config\+\_\+loader}}
\end{DoxyCompactItemize}
\doxysubsubsection*{Fonctions}
\begin{DoxyCompactItemize}
\item 
\mbox{\hyperlink{namespaceapp_1_1config__loader_ae642fb808edb3680f9bed49a9b3dfe65}{app.\+config\+\_\+loader.\+load\+\_\+config}} (path)
\end{DoxyCompactItemize}

\doxysubsection{Description détaillée}
Chargeur de configuration JSON pour le système de mesure. 

Ce module fournit une fonction simple pour charger et parser un fichier de configuration JSON contenant les paramètres des capteurs, timeouts et autres paramètres système. \begin{DoxyAuthor}{Auteur}
Léo Mendes @project 2510\+\_\+\+Regulations\+Chauffage @\+Mandant Oblo\+\_\+solution 
\end{DoxyAuthor}
\begin{DoxyDate}{Date}
2025-\/09-\/18 
\end{DoxyDate}
\begin{DoxyVersion}{Version}
1.\+0.\+0 
\end{DoxyVersion}
\begin{DoxyCopyright}{Copyright}
Copyright (c) 2025 
\end{DoxyCopyright}
