LeoMendesEsEtml/2510_RegulationChauffage/doc/6.Graphique, Schéma/3.Doxygen/latex/examples.tex

\doxysection{Exemples}
Liste de tous les exemples \+:\begin{DoxyCompactItemize}
\item 
\mbox{\hyperlink{_c_1_2_users_2thebi_2_documents_22510__regulation_chauffage_2doc_29_8_soft_ware_2_doxygen_2src_2app_2config_loader_8py-example}{C\+:/\+Users/thebi/\+Documents/2510\+\_\+\+Regulation\+Chauffage/doc/9.\+Soft\+Ware/\+Doxygen/src/app/config\+\_\+loader.\+py}}\end{DoxyCompactItemize}
