LeoMendesEsEtml/2510_RegulationChauffage/doc/6.Graphique, Schéma/3.Doxygen/latex/hw__mux__adg731_8py.tex

\doxysection{Référence du fichier C\+:/\+Users/thebi/\+Documents/2510\+\_\+\+Regulation\+Chauffage/doc/9.Soft\+Ware/\+Doxygen/src/app/hw\+\_\+mux\+\_\+adg731.py}
\hypertarget{hw__mux__adg731_8py}{}\label{hw__mux__adg731_8py}\index{C:/Users/thebi/Documents/2510\_RegulationChauffage/doc/9.SoftWare/Doxygen/src/app/hw\_mux\_adg731.py@{C:/Users/thebi/Documents/2510\_RegulationChauffage/doc/9.SoftWare/Doxygen/src/app/hw\_mux\_adg731.py}}

Pilote pour multiplexeur ADG731 via interface SPI.  

\doxysubsubsection*{Classes}
\begin{DoxyCompactItemize}
\item 
class \mbox{\hyperlink{classapp_1_1hw__mux__adg731_1_1_adg731_mux_spi}{app.\+hw\+\_\+mux\+\_\+adg731.\+Adg731\+Mux\+Spi}}
\begin{DoxyCompactList}\small\item\em Pilote SPI pour multiplexeurs ADG731. \end{DoxyCompactList}\end{DoxyCompactItemize}
\doxysubsubsection*{Espaces de nommage}
\begin{DoxyCompactItemize}
\item 
namespace \mbox{\hyperlink{namespaceapp}{app}}
\item 
namespace \mbox{\hyperlink{namespaceapp_1_1hw__mux__adg731}{app.\+hw\+\_\+mux\+\_\+adg731}}
\end{DoxyCompactItemize}
\doxysubsubsection*{Fonctions}
\begin{DoxyCompactItemize}
\item 
\mbox{\hyperlink{namespaceapp_1_1hw__mux__adg731_a191556bfaa023e4d6e1f2099dca9db46}{app.\+hw\+\_\+mux\+\_\+adg731.\+adg731\+\_\+ctrl\+\_\+byte}} (address, enable=True)
\begin{DoxyCompactList}\small\item\em Génère le byte de contrôle pour l\textquotesingle{}ADG731. \end{DoxyCompactList}\end{DoxyCompactItemize}

\doxysubsection{Description détaillée}
Pilote pour multiplexeur ADG731 via interface SPI. 

Ce module fournit un pilote pour contrôler les multiplexeurs ADG731 via l\textquotesingle{}interface SPI0. Supporte jusqu\textquotesingle{}à 4 cartes avec 32 canaux chacune. Gère la configuration SPI et l\textquotesingle{}envoi des commandes de contrôle pour la sélection des canaux. \begin{DoxyAuthor}{Auteur}
Léo Mendes @project 2510\+\_\+\+Regulations\+Chauffage @\+Mandant Oblo\+\_\+solution 
\end{DoxyAuthor}
\begin{DoxyDate}{Date}
2025-\/09-\/18 
\end{DoxyDate}
\begin{DoxyVersion}{Version}
1.\+0.\+0 
\end{DoxyVersion}
\begin{DoxyCopyright}{Copyright}
Copyright (c) 2025 
\end{DoxyCopyright}
