LeoMendesEsEtml/2510_RegulationChauffage/doc/6.Graphique, Schéma/3.Doxygen/latex/hw__tmux1204_8py.tex

\doxysection{Référence du fichier C\+:/\+Users/thebi/\+Documents/2510\+\_\+\+Regulation\+Chauffage/doc/9.Soft\+Ware/\+Doxygen/src/app/hw\+\_\+tmux1204.py}
\hypertarget{hw__tmux1204_8py}{}\label{hw__tmux1204_8py}\index{C:/Users/thebi/Documents/2510\_RegulationChauffage/doc/9.SoftWare/Doxygen/src/app/hw\_tmux1204.py@{C:/Users/thebi/Documents/2510\_RegulationChauffage/doc/9.SoftWare/Doxygen/src/app/hw\_tmux1204.py}}

Pilote pour multiplexeur TMUX1204 de sélection de résistance de référence.  

\doxysubsubsection*{Classes}
\begin{DoxyCompactItemize}
\item 
class \mbox{\hyperlink{classapp_1_1hw__tmux1204_1_1_tmux1204}{app.\+hw\+\_\+tmux1204.\+Tmux1204}}
\begin{DoxyCompactList}\small\item\em Pilote pour le multiplexeur TMUX1204. \end{DoxyCompactList}\end{DoxyCompactItemize}
\doxysubsubsection*{Espaces de nommage}
\begin{DoxyCompactItemize}
\item 
namespace \mbox{\hyperlink{namespaceapp}{app}}
\item 
namespace \mbox{\hyperlink{namespaceapp_1_1hw__tmux1204}{app.\+hw\+\_\+tmux1204}}
\end{DoxyCompactItemize}

\doxysubsection{Description détaillée}
Pilote pour multiplexeur TMUX1204 de sélection de résistance de référence. 

Ce module fournit un pilote pour contrôler le multiplexeur TMUX1204 via les signaux de contrôle ADC\+\_\+\+A1 et ADC\+\_\+\+A0. Permet la sélection de quatre valeurs de résistance de référence (2.\+2k, 2.\+7k, 10k, 100k) selon une table de vérité définie. \begin{DoxyAuthor}{Auteur}
Léo Mendes @project 2510\+\_\+\+Regulations\+Chauffage @\+Mandant Oblo\+\_\+solution 
\end{DoxyAuthor}
\begin{DoxyDate}{Date}
2025-\/09-\/18 
\end{DoxyDate}
\begin{DoxyVersion}{Version}
1.\+0.\+0 
\end{DoxyVersion}
\begin{DoxyCopyright}{Copyright}
Copyright (c) 2025 
\end{DoxyCopyright}
