LeoMendesEsEtml/2510_RegulationChauffage/doc/6.Graphique, Schéma/3.Doxygen/rtf/api__client_8py.rtf

begin bodyRÃ©fÃ©rence du fichier C:/Users/thebi/Documents/2510_RegulationChauffage/doc/9.SoftWare/Doxygen/src/app/api_client.py
AAAAAAAAAFAAAAAAAAAF
Client API pour les services oblosolutions.ch.
Classes
class app.api_client.ApiErrorException pour les erreurs d'API.
class app.api_client.ApiClientClient pour interroger les APIs oblosolutions.ch.
Espaces de nommage
namespace app
namespace app.api_client
Fonctions
Dict[str, Any] app.api_client.get_simulation_data (str mac_address)
RÃ©cupÃ¨re les donnÃ©es de simulation depuis les APIs.

bool app.api_client.send_temperature_measurement (str mac_address, float temperature, int channel=None)
Envoie une mesure de tempÃ©rature vers l'API.

Variables
int app.api_client.REQUEST_TIMEOUT = 10
int app.api_client.MAX_RETRIES = 3
int app.api_client.RETRY_DELAY = 1
str app.api_client.test_mac = "0030DEABCDEF"
Dict[str, Any] app.api_client.data = get_simulation_data(test_mac)

Description dÃ©taillÃ©e
Client API pour les services oblosolutions.ch.
Ce module fournit un client HTTP pour interroger les APIs td25_param et td25_forecast. Il gÃ¨re les timeouts, les retries automatiques et les erreurs de rÃ©seau. Inclut des fonctions utilitaires pour rÃ©cupÃ©rer les donnÃ©es de simulation et envoyer les mesures de tempÃ©rature.
Auteur
LÃ©o Mendes @project 2510_RegulationsChauffage @Mandant Oblo_solution
Date
2025-09-18
Version
1.0.0
Copyright
Copyright (c) 2025
