LeoMendesEsEtml/2510_RegulationChauffage/doc/6.Graphique, Schéma/3.Doxygen/rtf/classapp_1_1api__client_1_1_api_client.rtf

begin bodyRÃ©fÃ©rence de la classe app.api_client.ApiClient
AAAAAAAADAAAAAAAAADA
Client pour interroger les APIs oblosolutions.ch.
Graphe de collaboration de app.api_client.ApiClient:
IMAGE

Fonctions membres publiques
__init__ (self, str mac_address)
Initialise le client API.

Dict[str, Any] get_parameters (self)
RÃ©cupÃ¨re les paramÃ¨tres depuis l'API td25_param.

Dict[str, Any] get_forecast (self)
RÃ©cupÃ¨re la tempÃ©rature prÃ©vue depuis l'API td25_forecast.

bool post_measured_temperature (self, float temperature, int channel=None)
Envoie la tempÃ©rature mesurÃ©e vers l'API td25_param.

Attributs publics
mac_address = mac_address
str base_url = "https://dev.oblosolutions.ch"
Attributs publics statiques
str API_PATH_PREFIX = ""

Description dÃ©taillÃ©e
Client pour interroger les APIs oblosolutions.ch.
Fournit des mÃ©thodes pour rÃ©cupÃ©rer les paramÃ¨tres de simulation, les prÃ©visions mÃ©tÃ©o et envoyer les mesures de tempÃ©rature. GÃ¨re automatiquement les retries et les timeouts.

AAAAAAAADBAAAAAAAADBDocumentation des constructeurs et destructeur
app.api_client.ApiClient.__init__ ( self, str mac_address)
AAAAAAAADCAAAAAAAADC
Initialise le client API.
Configure l'adresse MAC du dispositif et l'URL de base pour les communications avec les services oblosolutions.ch.
ParamÃ¨tres
mac_address | Adresse MAC du dispositif (ex: "0030DEABCDEF").

AAAAAAAADDAAAAAAAADDDocumentation des fonctions membres
Dict[str, Any] app.api_client.ApiClient.get_forecast ( self)
AAAAAAAADEAAAAAAAADE
RÃ©cupÃ¨re la tempÃ©rature prÃ©vue depuis l'API td25_forecast.
Effectue une requÃªte GET vers l'endpoint td25_forecast avec l'adresse MAC comme paramÃ¨tre. Parse la rÃ©ponse JSON et extrait la tempÃ©rature de prÃ©vision mÃ©tÃ©orologique. Inclut un systÃ¨me de retry automatique en cas d'Ã©chec.
Renvoie
Dictionnaire contenant la temperature prÃ©vue.
Exceptions
ApiError | En cas d'erreur de rÃ©cupÃ©ration des donnÃ©es.
Dict[str, Any] app.api_client.ApiClient.get_parameters ( self)
AAAAAAAADFAAAAAAAADF
RÃ©cupÃ¨re les paramÃ¨tres depuis l'API td25_param.
Effectue une requÃªte GET vers l'endpoint td25_param avec l'adresse MAC comme paramÃ¨tre. Parse la rÃ©ponse JSON et extrait les champs probe_type, n, k_m et temperature. Inclut un systÃ¨me de retry automatique en cas d'Ã©chec.
Renvoie
Dictionnaire contenant probe_type, n, k_m, temperature.
Exceptions
ApiError | En cas d'erreur de rÃ©cupÃ©ration des donnÃ©es.
bool app.api_client.ApiClient.post_measured_temperature ( self, float temperature, int channel = None)
AAAAAAAADGAAAAAAAADG
Envoie la tempÃ©rature mesurÃ©e vers l'API td25_param.
Effectue une requÃªte POST vers l'endpoint td25_param avec la tempÃ©rature mesurÃ©e et optionnellement le numÃ©ro de canal. Tous les paramÃ¨tres sont envoyÃ©s dans l'URL comme paramÃ¨tres de requÃªte. Inclut un systÃ¨me de retry automatique.
ParamÃ¨tres
temperature | TempÃ©rature mesurÃ©e en Â°C.
channel | Canal de mesure (optionnel).
Renvoie True si succÃ¨s, False sinon.

AAAAAAAADHAAAAAAAADHDocumentation des donnÃ©es membres
str app.api_client.ApiClient.API_PATH_PREFIX = ""[static]
AAAAAAAADIAAAAAAAADIstr app.api_client.ApiClient.base_url = "https://dev.oblosolutions.ch"
AAAAAAAADJAAAAAAAADJapp.api_client.ApiClient.mac_address = mac_address
AAAAAAAADKAAAAAAAADK
La documentation de cette classe a Ã©tÃ© gÃ©nÃ©rÃ©e Ã partir du fichier suivant :
C:/Users/thebi/Documents/2510_RegulationChauffage/doc/9.SoftWare/Doxygen/src/app/api_client.py
