LeoMendesEsEtml/2510_RegulationChauffage/doc/6.Graphique, Schéma/3.Doxygen/rtf/classapp_1_1api__client_1_1_api_error.rtf

begin bodyRÃ©fÃ©rence de la classe app.api_client.ApiError
AAAAAAAADLAAAAAAAADL
Exception pour les erreurs d'API.
Graphe d'hÃ©ritage de app.api_client.ApiError:
IMAGE

Graphe de collaboration de app.api_client.ApiError:
IMAGE

Description dÃ©taillÃ©e
Exception pour les erreurs d'API.
Exception personnalisÃ©e levÃ©e en cas d'erreur lors des communications avec les APIs oblosolutions.ch.

La documentation de cette classe a Ã©tÃ© gÃ©nÃ©rÃ©e Ã partir du fichier suivant :
C:/Users/thebi/Documents/2510_RegulationChauffage/doc/9.SoftWare/Doxygen/src/app/api_client.py
