LeoMendesEsEtml/2510_RegulationChauffage/doc/6.Graphique, Schéma/3.Doxygen/rtf/classapp_1_1hw__tmux1204_1_1_tmux1204.rtf

begin bodyRÃ©fÃ©rence de la classe app.hw_tmux1204.Tmux1204
AAAAAAAAELAAAAAAAAEL
Pilote pour le multiplexeur TMUX1204.
Graphe de collaboration de app.hw_tmux1204.Tmux1204:
IMAGE

Fonctions membres publiques
__init__ (self)
Initialise le pilote TMUX1204.

close (self)
Ferme les interfaces GPIO.

set_bits (self, bit_a1, bit_a0)
DÃ©finit les bits de contrÃ´le A1 et A0.

select_rref_ohm (self, rref_ohm)
SÃ©lectionne la rÃ©sistance de rÃ©fÃ©rence Rref.

Attributs publics
gpio_a1 = GPIO(GPIO_CHIP_PATH, ADC_A1, "out")
gpio_a0 = GPIO(GPIO_CHIP_PATH, ADC_A0, "out")

Description dÃ©taillÃ©e
Pilote pour le multiplexeur TMUX1204.
Classe pour gÃ©rer la sÃ©lection de rÃ©sistance de rÃ©fÃ©rence via le multiplexeur TMUX1204. Utilise deux signaux de contrÃ´le (A1, A0) pour sÃ©lectionner parmi quatre valeurs de Rref selon la table de vÃ©ritÃ© :
• 1=0, A0=0 : 2.2k ohms
• 1=0, A0=1 : 2.7k ohms
• 1=1, A0=0 : 10k ohms
• 1=1, A0=1 : 100k ohms

AAAAAAAAEMAAAAAAAAEMDocumentation des constructeurs et destructeur
app.hw_tmux1204.Tmux1204.__init__ ( self)
AAAAAAAAENAAAAAAAAEN
Initialise le pilote TMUX1204.
Configure les GPIO pour les signaux de contrÃ´le A1 et A0 en mode sortie. Utilise les constantes matÃ©rielles dÃ©finies dans le module pins_cm5.

AAAAAAAAEOAAAAAAAAEODocumentation des fonctions membres
app.hw_tmux1204.Tmux1204.close ( self)
AAAAAAAAEPAAAAAAAAEP
Ferme les interfaces GPIO.
Ferme proprement les GPIO A1 et A0 pour libÃ©rer les ressources systÃ¨me. GÃ¨re les erreurs de fermeture pour Ã©viter les exceptions lors du nettoyage.
Voici le graphe d'appel pour cette fonction :
IMAGE
Voici le graphe des appelants de cette fonction :
IMAGE
app.hw_tmux1204.Tmux1204.select_rref_ohm ( self, rref_ohm)
AAAAAAAAEQAAAAAAAAEQ
SÃ©lectionne la rÃ©sistance de rÃ©fÃ©rence Rref.
Configure les signaux de contrÃ´le selon la table de vÃ©ritÃ© pour sÃ©lectionner la rÃ©sistance de rÃ©fÃ©rence demandÃ©e. Supporte quatre valeurs fixes : 2200, 2700, 10000, 100000 ohms.
ParamÃ¨tres
rref_ohm | Valeur de rÃ©sistance de rÃ©fÃ©rence en ohms.
Exceptions ValueError | Si la valeur de Rref n'est pas supportÃ©e.
Note Table de vÃ©ritÃ© TMUX1204 :
▪ 200 ohms : A1=0, A0=0
▪ 700 ohms : A1=0, A0=1
▪ 0000 ohms : A1=1, A0=0
▪ 00000 ohms: A1=1, A0=1
Voici le graphe d'appel pour cette fonction :
IMAGE
app.hw_tmux1204.Tmux1204.set_bits ( self, bit_a1, bit_a0)
AAAAAAAAERAAAAAAAAER
DÃ©finit les bits de contrÃ´le A1 et A0.
Applique les niveaux logiques sur les signaux de contrÃ´le du multiplexeur. Convertit les valeurs numÃ©riques (0/1) en niveaux logiques GPIO (False/True).
ParamÃ¨tres
bit_a1 | Valeur du bit A1 (0 ou 1).
bit_a0 | Valeur du bit A0 (0 ou 1).
Voici le graphe des appelants de cette fonction :
IMAGE

AAAAAAAAESAAAAAAAAESDocumentation des donnÃ©es membres
app.hw_tmux1204.Tmux1204.gpio_a0 = GPIO(GPIO_CHIP_PATH, ADC_A0, "out")
AAAAAAAAETAAAAAAAAETapp.hw_tmux1204.Tmux1204.gpio_a1 = GPIO(GPIO_CHIP_PATH, ADC_A1, "out")
AAAAAAAAEUAAAAAAAAEU
La documentation de cette classe a Ã©tÃ© gÃ©nÃ©rÃ©e Ã partir du fichier suivant :
C:/Users/thebi/Documents/2510_RegulationChauffage/doc/9.SoftWare/Doxygen/src/app/hw_tmux1204.py
