LeoMendesEsEtml/2510_RegulationChauffage/doc/6.Graphique, Schéma/3.Doxygen/rtf/dir_1b06078b4d982c1b64abd34436c8aa54.rtf

begin bodyRÃ©pertoire de rÃ©fÃ©rence de C:/Users/thebi/Documents/2510_RegulationChauffage
AAAAAAAAKNAAAAAAAAKNGraphe des dÃ©pendances de rÃ©pertoires pour 2510_RegulationChauffage:
IMAGE
RÃ©pertoires
rÃ©pertoire doc
