LeoMendesEsEtml/2510_RegulationChauffage/doc/6.Graphique, Schéma/3.Doxygen/rtf/dir_62261ce8f5512dd0af63408535a215d7.rtf

begin bodyRÃ©pertoire de rÃ©fÃ©rence de C:/Users/thebi/Documents/2510_RegulationChauffage/doc/9.SoftWare
AAAAAAAAKOAAAAAAAAKOGraphe des dÃ©pendances de rÃ©pertoires pour 9.SoftWare:
IMAGE
RÃ©pertoires
rÃ©pertoire Doxygen
