LeoMendesEsEtml/2510_RegulationChauffage/doc/6.Graphique, Schéma/3.Doxygen/rtf/dir_66b2cbd9a818255da9ff447d4313ad04.rtf

begin bodyRÃ©pertoire de rÃ©fÃ©rence de C:/Users/thebi/Documents/2510_RegulationChauffage/doc/9.SoftWare/Doxygen/src/webui
AAAAAAAAKVAAAAAAAAKVGraphe des dÃ©pendances de rÃ©pertoires pour webui:
IMAGE
Fichiers
fichier __init__.py
fichier webui_server.py
Serveur web pour interface utilisateur de configuration.
