LeoMendesEsEtml/2510_RegulationChauffage/doc/6.Graphique, Schéma/3.Doxygen/rtf/dir_9ce5bac9cd81f23a20cf451fc30b31c2.rtf

begin bodyRÃ©pertoire de rÃ©fÃ©rence de C:/Users/thebi/Documents/2510_RegulationChauffage/doc
AAAAAAAAKRAAAAAAAAKRGraphe des dÃ©pendances de rÃ©pertoires pour doc:
IMAGE
RÃ©pertoires
rÃ©pertoire 9.SoftWare
