LeoMendesEsEtml/2510_RegulationChauffage/doc/6.Graphique, Schéma/3.Doxygen/rtf/dir_a30191f5867566fd376dca42effbb4e4.rtf

begin bodyRÃ©pertoire de rÃ©fÃ©rence de C:/Users/thebi/Documents/2510_RegulationChauffage/doc/9.SoftWare/Doxygen/src
AAAAAAAAKUAAAAAAAAKUGraphe des dÃ©pendances de rÃ©pertoires pour src:
IMAGE
RÃ©pertoires
rÃ©pertoire apprÃ©pertoire config_modulerÃ©pertoire webui
