LeoMendesEsEtml/2510_RegulationChauffage/doc/6.Graphique, Schéma/3.Doxygen/rtf/dir_ce690f3e856880fba2f242fa91d49dc9.rtf

begin bodyRÃ©pertoire de rÃ©fÃ©rence de C:/Users/thebi/Documents/2510_RegulationChauffage/doc/9.SoftWare/Doxygen
AAAAAAAAKTAAAAAAAAKTGraphe des dÃ©pendances de rÃ©pertoires pour Doxygen:
IMAGE
RÃ©pertoires
rÃ©pertoire src
