LeoMendesEsEtml/2510_RegulationChauffage/doc/6.Graphique, Schéma/3.Doxygen/rtf/dir_f396504afdc959660871b003fa10164d.rtf

begin bodyRÃ©pertoire de rÃ©fÃ©rence de C:/Users/thebi/Documents
AAAAAAAAKSAAAAAAAAKSRÃ©pertoires
rÃ©pertoire 2510_RegulationChauffage
