LeoMendesEsEtml/2510_RegulationChauffage/doc/6.Graphique, Schéma/3.Doxygen/rtf/hw__tmux1204_8py.rtf

begin bodyRÃ©fÃ©rence du fichier C:/Users/thebi/Documents/2510_RegulationChauffage/doc/9.SoftWare/Doxygen/src/app/hw_tmux1204.py
AAAAAAAAAJAAAAAAAAAJ
Pilote pour multiplexeur TMUX1204 de sÃ©lection de rÃ©sistance de rÃ©fÃ©rence.
Classes
class app.hw_tmux1204.Tmux1204Pilote pour le multiplexeur TMUX1204.
Espaces de nommage
namespace app
namespace app.hw_tmux1204

Description dÃ©taillÃ©e
Pilote pour multiplexeur TMUX1204 de sÃ©lection de rÃ©sistance de rÃ©fÃ©rence.
Ce module fournit un pilote pour contrÃ´ler le multiplexeur TMUX1204 via les signaux de contrÃ´le ADC_A1 et ADC_A0. Permet la sÃ©lection de quatre valeurs de rÃ©sistance de rÃ©fÃ©rence (2.2k, 2.7k, 10k, 100k) selon une table de vÃ©ritÃ© dÃ©finie.
Auteur
LÃ©o Mendes @project 2510_RegulationsChauffage @Mandant Oblo_solution
Date
2025-09-18
Version
1.0.0
Copyright
Copyright (c) 2025
