LeoMendesEsEtml/2510_RegulationChauffage/doc/6.Graphique, Schéma/3.Doxygen/rtf/namespaceapp_1_1adc__ads124s08.rtf

begin bodyRÃ©fÃ©rence de l'espace de nommage app.adc_ads124s08
AAAAAAAAAXAAAAAAAAAXClasses
class Ads124s08Driver pour l'ADC ADS124S08 avec interface SPI.
Fonctions
encode_gain (pga_gain)
Encode le gain PGA en code binaire pour le registre.

encode_idac_uA (idac_uA)
Encode la magnitude IDAC en code binaire pour le registre.

sign_extend_24 (b0, b1, b2)
Ã‰tend le signe d'un code ADC 24 bits vers 32 bits.

Variables
int REG_ID = 0x00
int REG_STATUS = 0x01
int REG_INPMUX = 0x02
int REG_PGA = 0x03
int REG_DATARATE = 0x04
int REG_REF = 0x05
int REG_IDACMUX = 0x07
int REG_SYS = 0x09
int REG_IDACMAG = 0x06
int CMD_RESET = 0x06
int CMD_START = 0x08
int CMD_STOP = 0x0A
int CMD_RDATA = 0x12
tuple FS = (1 << 23) - 1
dict CHANNELS

AAAAAAAAAYAAAAAAAAAYDocumentation des fonctions
app.adc_ads124s08.encode_gain ( pga_gain)
AAAAAAAAAZAAAAAAAAAZ
Encode le gain PGA en code binaire pour le registre.
Convertit une valeur de gain dÃ©cimale en code binaire 3 bits pour la configuration du registre PGA de l'ADS124S08.
ParamÃ¨tres
pga_gain | Valeur du gain PGA (1, 2, 4, 8, 16, 32, 64, 128).
Renvoie Code binaire 3 bits correspondant au gain.
Exceptions
ValueError | si le gain fourni n'est pas supportÃ©.
Voir Ã©galement configure_channel
Voici le graphe des appelants de cette fonction :
IMAGE
app.adc_ads124s08.encode_idac_uA ( idac_uA)
AAAAAAAABAAAAAAAAABA
Encode la magnitude IDAC en code binaire pour le registre.
Convertit une valeur de courant IDAC en microampÃ¨res en code binaire 4 bits pour la configuration du registre IDACMAG.
ParamÃ¨tres
idac_uA | Courant IDAC en microampÃ¨res (10, 50, 100, 250, 500, 1000, 1500, 2000).
Renvoie Code binaire 4 bits correspondant au courant.
Exceptions
ValueError | si le courant fourni n'est pas supportÃ©.
Voir Ã©galement configure_channel
Voici le graphe des appelants de cette fonction :
IMAGE
app.adc_ads124s08.sign_extend_24 ( b0, b1, b2)
AAAAAAAABBAAAAAAAABB
Ã‰tend le signe d'un code ADC 24 bits vers 32 bits.
Convertit un code ADC 24 bits signÃ© en entier Python 32 bits en prÃ©servant le signe selon la reprÃ©sentation en complÃ©ment Ã 2.
ParamÃ¨tres
b0 | Octet de poids fort (MSB) du code 24 bits.
b1 | Octet du milieu du code 24 bits.
b2 | Octet de poids faible (LSB) du code 24 bits.
Renvoie Valeur entiÃ¨re signÃ©e 32 bits correspondante.
Note
NÃ©cessaire car Python gÃ¨re automatiquement les entiers de taille variable.
Voir Ã©galement
read_code24
Voici le graphe des appelants de cette fonction :
IMAGE

AAAAAAAABCAAAAAAAABCDocumentation des variables
dict app.adc_ads124s08.CHANNELS
AAAAAAAABDAAAAAAAABDValeur initiale :
1 = {
2 # Canal 1: entrÃ©e positive AIN1, nÃ©gative AIN2
3 1: {"ainp_idx": 1, "ainn_idx": 2},
4 # Canal 2: entrÃ©e positive AIN4, nÃ©gative AIN5
5 2: {"ainp_idx": 4, "ainn_idx": 5},
6 # Canal 3: entrÃ©e positive AIN7, nÃ©gative AIN8
7 3: {"ainp_idx": 7, "ainn_idx": 8},
8 # Canal 4: entrÃ©e positive AIN10, nÃ©gative AIN11
9 4: {"ainp_idx": 10, "ainn_idx": 11}
10 }
int app.adc_ads124s08.CMD_RDATA = 0x12
AAAAAAAABEAAAAAAAABEint app.adc_ads124s08.CMD_RESET = 0x06
AAAAAAAABFAAAAAAAABFint app.adc_ads124s08.CMD_START = 0x08
AAAAAAAABGAAAAAAAABGint app.adc_ads124s08.CMD_STOP = 0x0A
AAAAAAAABHAAAAAAAABHtuple app.adc_ads124s08.FS = (1 << 23) - 1
AAAAAAAABIAAAAAAAABIint app.adc_ads124s08.REG_DATARATE = 0x04
AAAAAAAABJAAAAAAAABJint app.adc_ads124s08.REG_ID = 0x00
AAAAAAAABKAAAAAAAABKint app.adc_ads124s08.REG_IDACMAG = 0x06
AAAAAAAABLAAAAAAAABLint app.adc_ads124s08.REG_IDACMUX = 0x07
AAAAAAAABMAAAAAAAABMint app.adc_ads124s08.REG_INPMUX = 0x02
AAAAAAAABNAAAAAAAABNint app.adc_ads124s08.REG_PGA = 0x03
AAAAAAAABOAAAAAAAABOint app.adc_ads124s08.REG_REF = 0x05
AAAAAAAABPAAAAAAAABPint app.adc_ads124s08.REG_STATUS = 0x01
AAAAAAAABQAAAAAAAABQint app.adc_ads124s08.REG_SYS = 0x09
AAAAAAAABRAAAAAAAABR
