LeoMendesEsEtml/2510_RegulationChauffage/doc/6.Graphique, Schéma/3.Doxygen/rtf/namespaceapp_1_1api__client.rtf

begin bodyRÃ©fÃ©rence de l'espace de nommage app.api_client
AAAAAAAACQAAAAAAAACQClasses
class ApiClientClient pour interroger les APIs oblosolutions.ch.
class ApiErrorException pour les erreurs d'API.
Fonctions
Dict[str, Any] get_simulation_data (str mac_address)
RÃ©cupÃ¨re les donnÃ©es de simulation depuis les APIs.

bool send_temperature_measurement (str mac_address, float temperature, int channel=None)
Envoie une mesure de tempÃ©rature vers l'API.

Variables
int REQUEST_TIMEOUT = 10
int MAX_RETRIES = 3
int RETRY_DELAY = 1
str test_mac = "0030DEABCDEF"
Dict[str, Any] data = get_simulation_data(test_mac)

AAAAAAAACRAAAAAAAACRDocumentation des fonctions
Dict[str, Any] app.api_client.get_simulation_data (str mac_address)
AAAAAAAACSAAAAAAAACS
RÃ©cupÃ¨re les donnÃ©es de simulation depuis les APIs.
Combine les appels vers td25_param et td25_forecast pour rÃ©cupÃ©rer tous les paramÃ¨tres nÃ©cessaires Ã la simulation de tempÃ©rature. Utilise le client ApiClient pour gÃ©rer les retries et les erreurs automatiquement.
ParamÃ¨tres
mac_address | Adresse MAC du dispositif.
Renvoie Dictionnaire avec toutes les donnÃ©es nÃ©cessaires pour la simulation.
Exceptions
ApiError | Si aucune donnÃ©e valide n'est obtenue.
bool app.api_client.send_temperature_measurement (str mac_address, float temperature, int channel = None)
AAAAAAAACTAAAAAAAACT
Envoie une mesure de tempÃ©rature vers l'API.
Fonction utilitaire qui crÃ©e un client ApiClient et utilise la mÃ©thode post_measured_temperature pour envoyer la tempÃ©rature mesurÃ©e. GÃ¨re les exceptions et retourne un boolÃ©en simple.
ParamÃ¨tres
mac_address | Adresse MAC du dispositif.
temperature | TempÃ©rature mesurÃ©e en Â°C.
channel | Canal de mesure (optionnel).
Renvoie True si succÃ¨s, False sinon.

AAAAAAAACUAAAAAAAACUDocumentation des variables
Dict[str, Any] app.api_client.data = get_simulation_data(test_mac)
AAAAAAAACVAAAAAAAACVint app.api_client.MAX_RETRIES = 3
AAAAAAAACWAAAAAAAACWint app.api_client.REQUEST_TIMEOUT = 10
AAAAAAAACXAAAAAAAACXint app.api_client.RETRY_DELAY = 1
AAAAAAAACYAAAAAAAACYstr app.api_client.test_mac = "0030DEABCDEF"
AAAAAAAACZAAAAAAAACZ
