LeoMendesEsEtml/2510_RegulationChauffage/doc/6.Graphique, Schéma/3.Doxygen/rtf/namespaceapp_1_1hw__mux__adg731.rtf

begin bodyRÃ©fÃ©rence de l'espace de nommage app.hw_mux_adg731
AAAAAAAADWAAAAAAAADWClasses
class Adg731MuxSpiPilote SPI pour multiplexeurs ADG731.
Fonctions
adg731_ctrl_byte (address, enable=True)
GÃ©nÃ¨re le byte de contrÃ´le pour l'ADG731.

AAAAAAAADXAAAAAAAADXDocumentation des fonctions
app.hw_mux_adg731.adg731_ctrl_byte ( address, enable = True)
AAAAAAAADYAAAAAAAADY
GÃ©nÃ¨re le byte de contrÃ´le pour l'ADG731.
Construit l'octet de commande selon le protocole ADG731 avec le bit d'activation (EN) en MSB et l'adresse sur 5 bits. L'activation se fait avec EN=0 (logique inversÃ©e).
ParamÃ¨tres
address | Adresse du canal (0-31).
enable | Ã‰tat d'activation du canal (True=activÃ©).
Renvoie Octet de contrÃ´le formatÃ© selon le protocole ADG731.
Exceptions
ValueError | Si l'adresse est hors de la plage valide.
Voici le graphe des appelants de cette fonction :
IMAGE
