LeoMendesEsEtml/2510_RegulationChauffage/doc/6.Graphique, Schéma/3.Doxygen/rtf/namespaceapp_1_1mesure__24v__dry__contact.rtf

begin bodyRÃ©fÃ©rence de l'espace de nommage app.mesure_24v_dry_contact
AAAAAAAAFMAAAAAAAAFMFonctions
test_24v_dry_contact ()
Test des contacts secs I/O 24V.

get_dry_contact_status ()
Retourne l'Ã©tat actuel des contacts secs.

Variables
int CM_24V_OUT_1 = 13
int CM_24V_SENSE_1 = 14
int CM_24V_OUT_2 = 15
int CM_24V_SENSE_2 = 16
int io_24v_ch1_ok = 0
int io_24v_ch2_ok = 0

AAAAAAAAFNAAAAAAAAFNDocumentation des fonctions
app.mesure_24v_dry_contact.get_dry_contact_status ()
AAAAAAAAFOAAAAAAAAFO
Retourne l'Ã©tat actuel des contacts secs.
Fonction utilitaire qui retourne les derniers Ã©tats mesurÃ©s des contacts secs sans effectuer de nouveau test. Utilise les variables globales mises Ã jour par test_24v_dry_contact().
Renvoie
Dictionnaire contenant l'Ã©tat des deux canaux. Format {"ch1": 0|1, "ch2": 0|1} Valeurs 0=ouvert, 1=fermÃ©.
app.mesure_24v_dry_contact.test_24v_dry_contact ()
AAAAAAAAFPAAAAAAAAFP
Test des contacts secs I/O 24V.
Effectue un test complet des deux canaux de contacts secs 24V. Active sÃ©quentiellement chaque sortie et lit l'Ã©tat du capteur correspondant pour dÃ©terminer si le contact est fermÃ© ou ouvert. Met Ã jour les variables globales d'Ã©tat et affiche les rÃ©sultats.
Renvoie
Tuple contenant l'Ã©tat des deux canaux (ch1_state, ch2_state). Valeurs 0=ouvert, 1=fermÃ©.
Note
Utilise des temporisations pour la stabilisation des signaux.

AAAAAAAAFQAAAAAAAAFQDocumentation des variables
int app.mesure_24v_dry_contact.CM_24V_OUT_1 = 13
AAAAAAAAFRAAAAAAAAFRint app.mesure_24v_dry_contact.CM_24V_OUT_2 = 15
AAAAAAAAFSAAAAAAAAFSint app.mesure_24v_dry_contact.CM_24V_SENSE_1 = 14
AAAAAAAAFTAAAAAAAAFTint app.mesure_24v_dry_contact.CM_24V_SENSE_2 = 16
AAAAAAAAFUAAAAAAAAFUint app.mesure_24v_dry_contact.io_24v_ch1_ok = 0
AAAAAAAAFVAAAAAAAAFVint app.mesure_24v_dry_contact.io_24v_ch2_ok = 0
AAAAAAAAFWAAAAAAAAFW
