LeoMendesEsEtml/2510_RegulationChauffage/doc/6.Graphique, Schéma/3.Doxygen/rtf/namespaceapp_1_1temperature__simulation.rtf

begin bodyRÃ©fÃ©rence de l'espace de nommage app.temperature_simulation
AAAAAAAAIRAAAAAAAAIRFonctions
Optional[float] calculate_simulated_temperature (float t_mes, float t_prev, float n, float k_m)
Calcule la tempÃ©rature simulÃ©e selon la formule prÃ©dictive.

bool validate_simulation_parameters (str probe_type, float n, float k_m, float t_mes, float t_prev)
Valide tous les paramÃ¨tres de simulation avant exÃ©cution.

Optional[float] run_temperature_simulation (dict simulation_data)
ExÃ©cute une simulation complÃ¨te de tempÃ©rature avec dictionnaire.

AAAAAAAAISAAAAAAAAISDocumentation des fonctions
Optional[float] app.temperature_simulation.calculate_simulated_temperature (float t_mes, float t_prev, float n, float k_m)
AAAAAAAAITAAAAAAAAIT
Calcule la tempÃ©rature simulÃ©e selon la formule prÃ©dictive.
ImplÃ©mente la formule T_sim = T_mes + ((T_prev - T_mes) * n * exp(k_m)) avec validation complÃ¨te des paramÃ¨tres et gestion des erreurs numÃ©riques (overflow, underflow, valeurs infinies).
ParamÃ¨tres
t_mes | TempÃ©rature mesurÃ©e [Â°C].
t_prev | TempÃ©rature prÃ©vue [Â°C].
n | ParamÃ¨tre de pondÃ©ration [-âˆž, +âˆž].
k_m | ParamÃ¨tre exposant pour fonction exponentielle [-âˆž, +âˆž].
Renvoie TempÃ©rature simulÃ©e [Â°C] ou None en cas d'erreur.
Exceptions
OverflowError | si exp(k_m) dÃ©passe les limites numÃ©riques.
Avertissement Limitation automatique des paramÃ¨tres extrÃªmes.
Voici le graphe des appelants de cette fonction :
IMAGE
Optional[float] app.temperature_simulation.run_temperature_simulation (dict simulation_data)
AAAAAAAAIUAAAAAAAAIU
ExÃ©cute une simulation complÃ¨te de tempÃ©rature avec dictionnaire.
Fonction principale d'orchestration qui extrait les paramÃ¨tres d'un dictionnaire, valide tous les paramÃ¨tres et execute la simulation complÃ¨te avec gestion d'erreur robuste.
ParamÃ¨tres
Dictionnaire contenant tous les paramÃ¨tres requis: ◦ robe_type: Type de sonde (str)
◦ : ParamÃ¨tre de pondÃ©ration (float)
◦ _m: ParamÃ¨tre exposant (float)
◦ emperature: TempÃ©rature mesurÃ©e (float)
◦ orecast_temperature: TempÃ©rature prÃ©vue (float)
simulation_data
Renvoie
TempÃ©rature simulÃ©e [Â°C] ou None si erreur.
Avertissement
Retourne None pour toute erreur de validation ou calcul.
Voici le graphe d'appel pour cette fonction :
IMAGE
bool app.temperature_simulation.validate_simulation_parameters (str probe_type, float n, float k_m, float t_mes, float t_prev)
AAAAAAAAIVAAAAAAAAIV
Valide tous les paramÃ¨tres de simulation avant exÃ©cution.
Fonction de validation complÃ¨te qui vÃ©rifie la cohÃ©rence et les plages de tous les paramÃ¨tres d'entrÃ©e. Inclut la vÃ©rification interactive pour les Ã©carts importants.
ParamÃ¨tres
probe_type | Type de sonde Ã utiliser pour la simulation.
n | ParamÃ¨tre de pondÃ©ration de la simulation.
k_m | ParamÃ¨tre exposant de la fonction exponentielle.
t_mes | TempÃ©rature mesurÃ©e Ã valider [Â°C].
t_prev | TempÃ©rature prÃ©vue Ã valider [Â°C].
Renvoie True si tous les paramÃ¨tres sont valides.
Avertissement
Demande confirmation utilisateur pour Ã©carts importants.
Voici le graphe des appelants de cette fonction :
IMAGE
