LeoMendesEsEtml/2510_RegulationChauffage/doc/6.Graphique, Schéma/3.Doxygen/rtf/namespaceconfig__module.rtf

begin bodyRÃ©fÃ©rence de l'espace de nommage config_module
AAAAAAAAJRAAAAAAAAJREspaces de nommage
namespace cm5_config
