LeoMendesEsEtml/2510_RegulationChauffage/doc/6.Graphique, Schéma/3.Doxygen/rtf/namespacewebui.rtf

begin bodyRÃ©fÃ©rence de l'espace de nommage webui
AAAAAAAAJXAAAAAAAAJXEspaces de nommage
namespace webui_server
