LeoMendesEsEtml/2510_RegulationChauffage/doc/6.Graphique, Schéma/3.Doxygen/rtf/namespacewebui_1_1webui__server.rtf

begin bodyRÃ©fÃ©rence de l'espace de nommage webui.webui_server
AAAAAAAAJYAAAAAAAAJYFonctions
serve_index ()
Sert la page principale de l'interface web.

get_config ()
RÃ©cupÃ¨re la configuration actuelle des capteurs.

put_config ()
Sauvegarde une nouvelle configuration des capteurs.

get_last ()
RÃ©cupÃ¨re le dernier Ã©tat du systÃ¨me de mesure.

force_reload ()
Force le rechargement de la configuration au prochain cycle.

Variables
BASE_DIR = os.path.abspath(os.path.join(os.path.dirname(__file__), ".."))
CONFIG_PATH = os.path.join(BASE_DIR, "config_module", "sensors.json")
STATE_PATH = os.path.join(BASE_DIR, "state", "last_state.json")
WEBUI_DIR = os.path.dirname(__file__)
app = Flask(__name__, static_folder=WEBUI_DIR, static_url_path='/static')
host
port

AAAAAAAAJZAAAAAAAAJZDocumentation des fonctions
webui.webui_server.force_reload ()
AAAAAAAAKAAAAAAAAAKA
Force le rechargement de la configuration au prochain cycle.
CrÃ©e un fichier flag force_reload.flag avec horodatage pour dÃ©clencher le rechargement de configuration par le processus principal lors du prochain cycle de mesure.
Renvoie
Confirmation de demande ou message d'erreur avec code HTTP.
webui.webui_server.get_config ()
AAAAAAAAKBAAAAAAAAKB
RÃ©cupÃ¨re la configuration actuelle des capteurs.
Lecture du fichier sensors.json et retour des donnÃ©es de configuration en format JSON. GÃ¨re les erreurs de lecture et affiche des informations de dÃ©bogage.
Renvoie
Configuration JSON ou message d'erreur avec code HTTP.
webui.webui_server.get_last ()
AAAAAAAAKCAAAAAAAAKC
RÃ©cupÃ¨re le dernier Ã©tat du systÃ¨me de mesure.
Lecture du fichier last_state.json contenant les derniÃ¨res mesures, tempÃ©ratures et statuts. GÃ¨re le cas oÃ¹ le fichier n'existe pas encore et retourne un Ã©tat par dÃ©faut.
Renvoie
Ã‰tat JSON du systÃ¨me ou structure par dÃ©faut si fichier absent.
webui.webui_server.put_config ()
AAAAAAAAKDAAAAAAAAKD
Sauvegarde une nouvelle configuration des capteurs.
ReÃ§oit des donnÃ©es JSON, valide le contenu et sauvegarde dans sensors.json avec sauvegarde atomique via fichier temporaire. Affiche un rÃ©sumÃ© des changements principaux.
Renvoie
Statut de sauvegarde ou message d'erreur avec code HTTP.
webui.webui_server.serve_index ()
AAAAAAAAKEAAAAAAAAKE
Sert la page principale de l'interface web.
Route racine qui retourne le fichier index.html depuis le rÃ©pertoire webui pour affichage de l'interface utilisateur.
Renvoie
Fichier HTML de l'interface principale.

AAAAAAAAKFAAAAAAAAKFDocumentation des variables
webui.webui_server.app = Flask(__name__, static_folder=WEBUI_DIR, static_url_path='/static')
AAAAAAAAKGAAAAAAAAKGwebui.webui_server.BASE_DIR = os.path.abspath(os.path.join(os.path.dirname(__file__), ".."))
AAAAAAAAKHAAAAAAAAKHwebui.webui_server.CONFIG_PATH = os.path.join(BASE_DIR, "config_module", "sensors.json")
AAAAAAAAKIAAAAAAAAKIwebui.webui_server.host
AAAAAAAAKJAAAAAAAAKJwebui.webui_server.port
AAAAAAAAKKAAAAAAAAKKwebui.webui_server.STATE_PATH = os.path.join(BASE_DIR, "state", "last_state.json")
AAAAAAAAKLAAAAAAAAKLwebui.webui_server.WEBUI_DIR = os.path.dirname(__file__)
AAAAAAAAKMAAAAAAAAKM
