LeoMendesEsEtml/2510_RegulationChauffage/mec/Composant 3d/ACDC.pdf

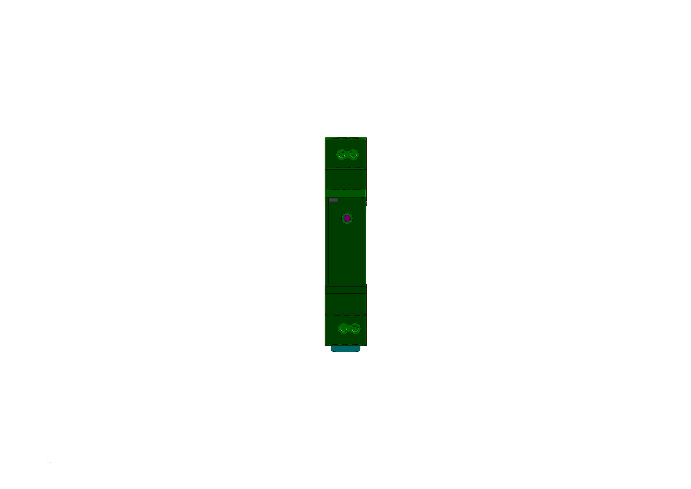
[picture p73: page 1]
