LeoMendesEsEtml/2510_RegulationChauffage/doc/5.Ressource/Carte LED.jpg

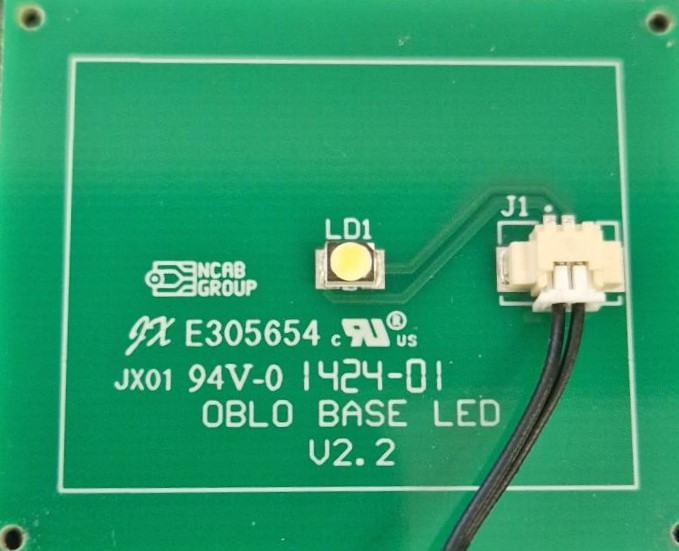
doc/5.Ressource/Carte LED.jpg
