LeoMendesEsEtml/2510_RegulationChauffage/doc/5.Ressource/oblo_vignette-removebg-preview.png

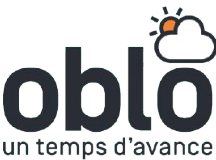
doc/5.Ressource/oblo_vignette-removebg-preview.png
