LeoMendesEsEtml/2510_RegulationChauffage/doc/9.SoftWare/FindIP/Capture d’écran 2025-09-02 192237.png

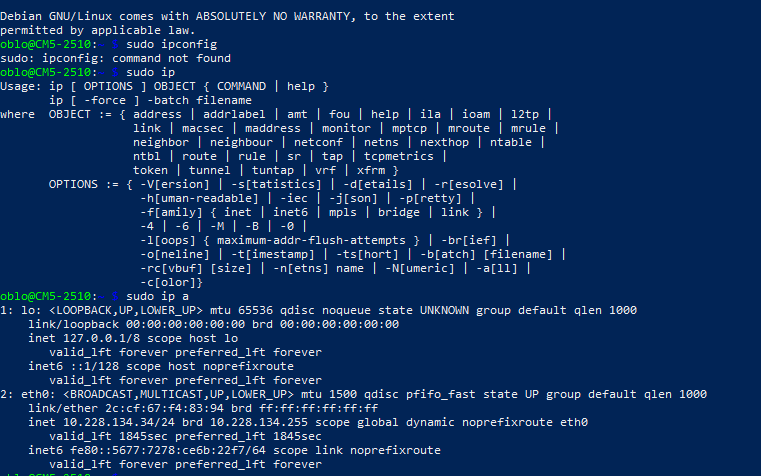
doc/9.SoftWare/FindIP/Capture d’écran 2025-09-02 192237.png
