LeoMendesEsEtml/2510_RegulationChauffage/doc/11.Mesure/LDO 3V3/LDO_3V_No_Charge.png

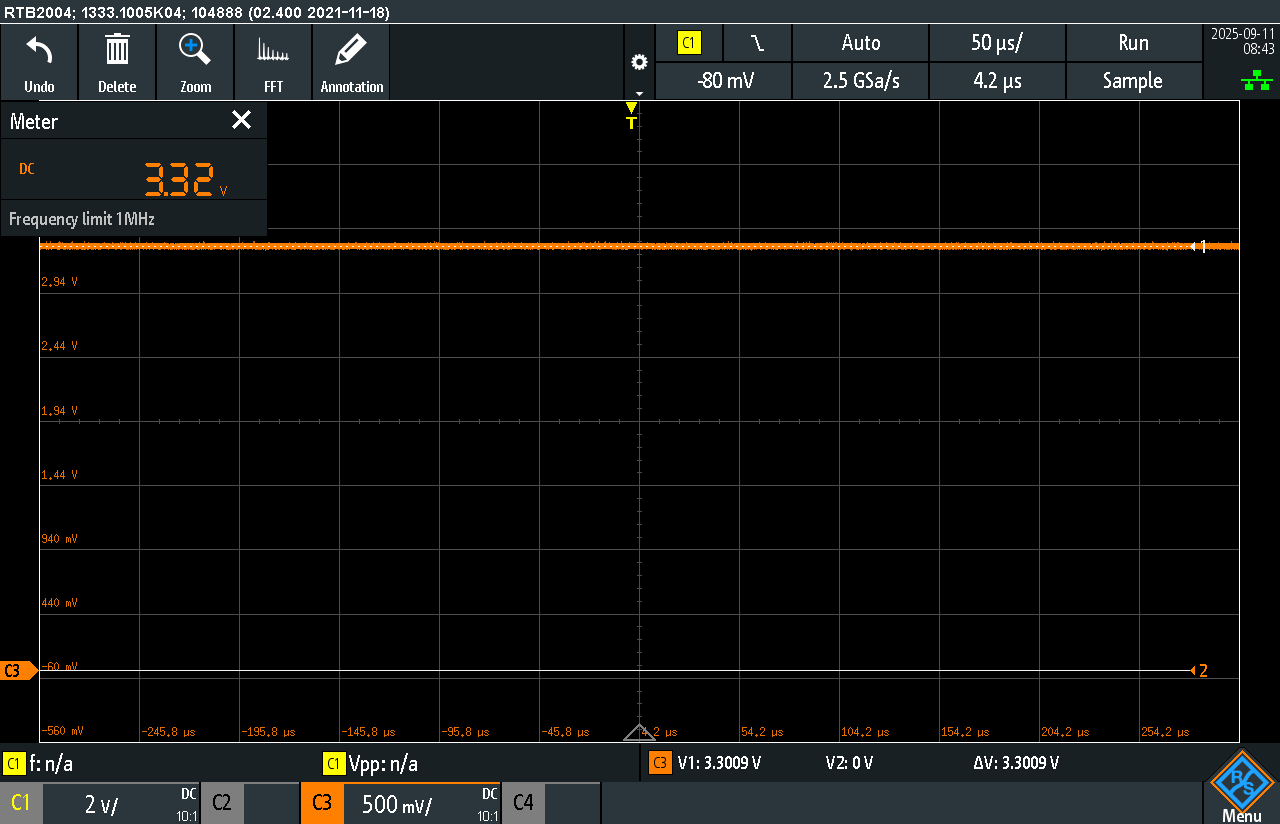
doc/11.Mesure/LDO 3V3/LDO_3V_No_Charge.png
