LeoMendesEsEtml/2510_RegulationChauffage/soft/src/webui/ETMLES.png

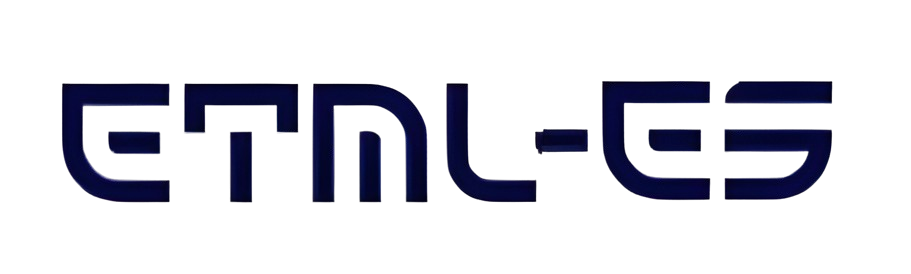
soft/src/webui/ETMLES.png
