LeoMendesEsEtml/2510_RegulationChauffage/doc/10.EnvoisFichier/Revue_Layout_02_09_2025/2510_RegulationChauffage_Motherboard_Drawing.pdf

F

E

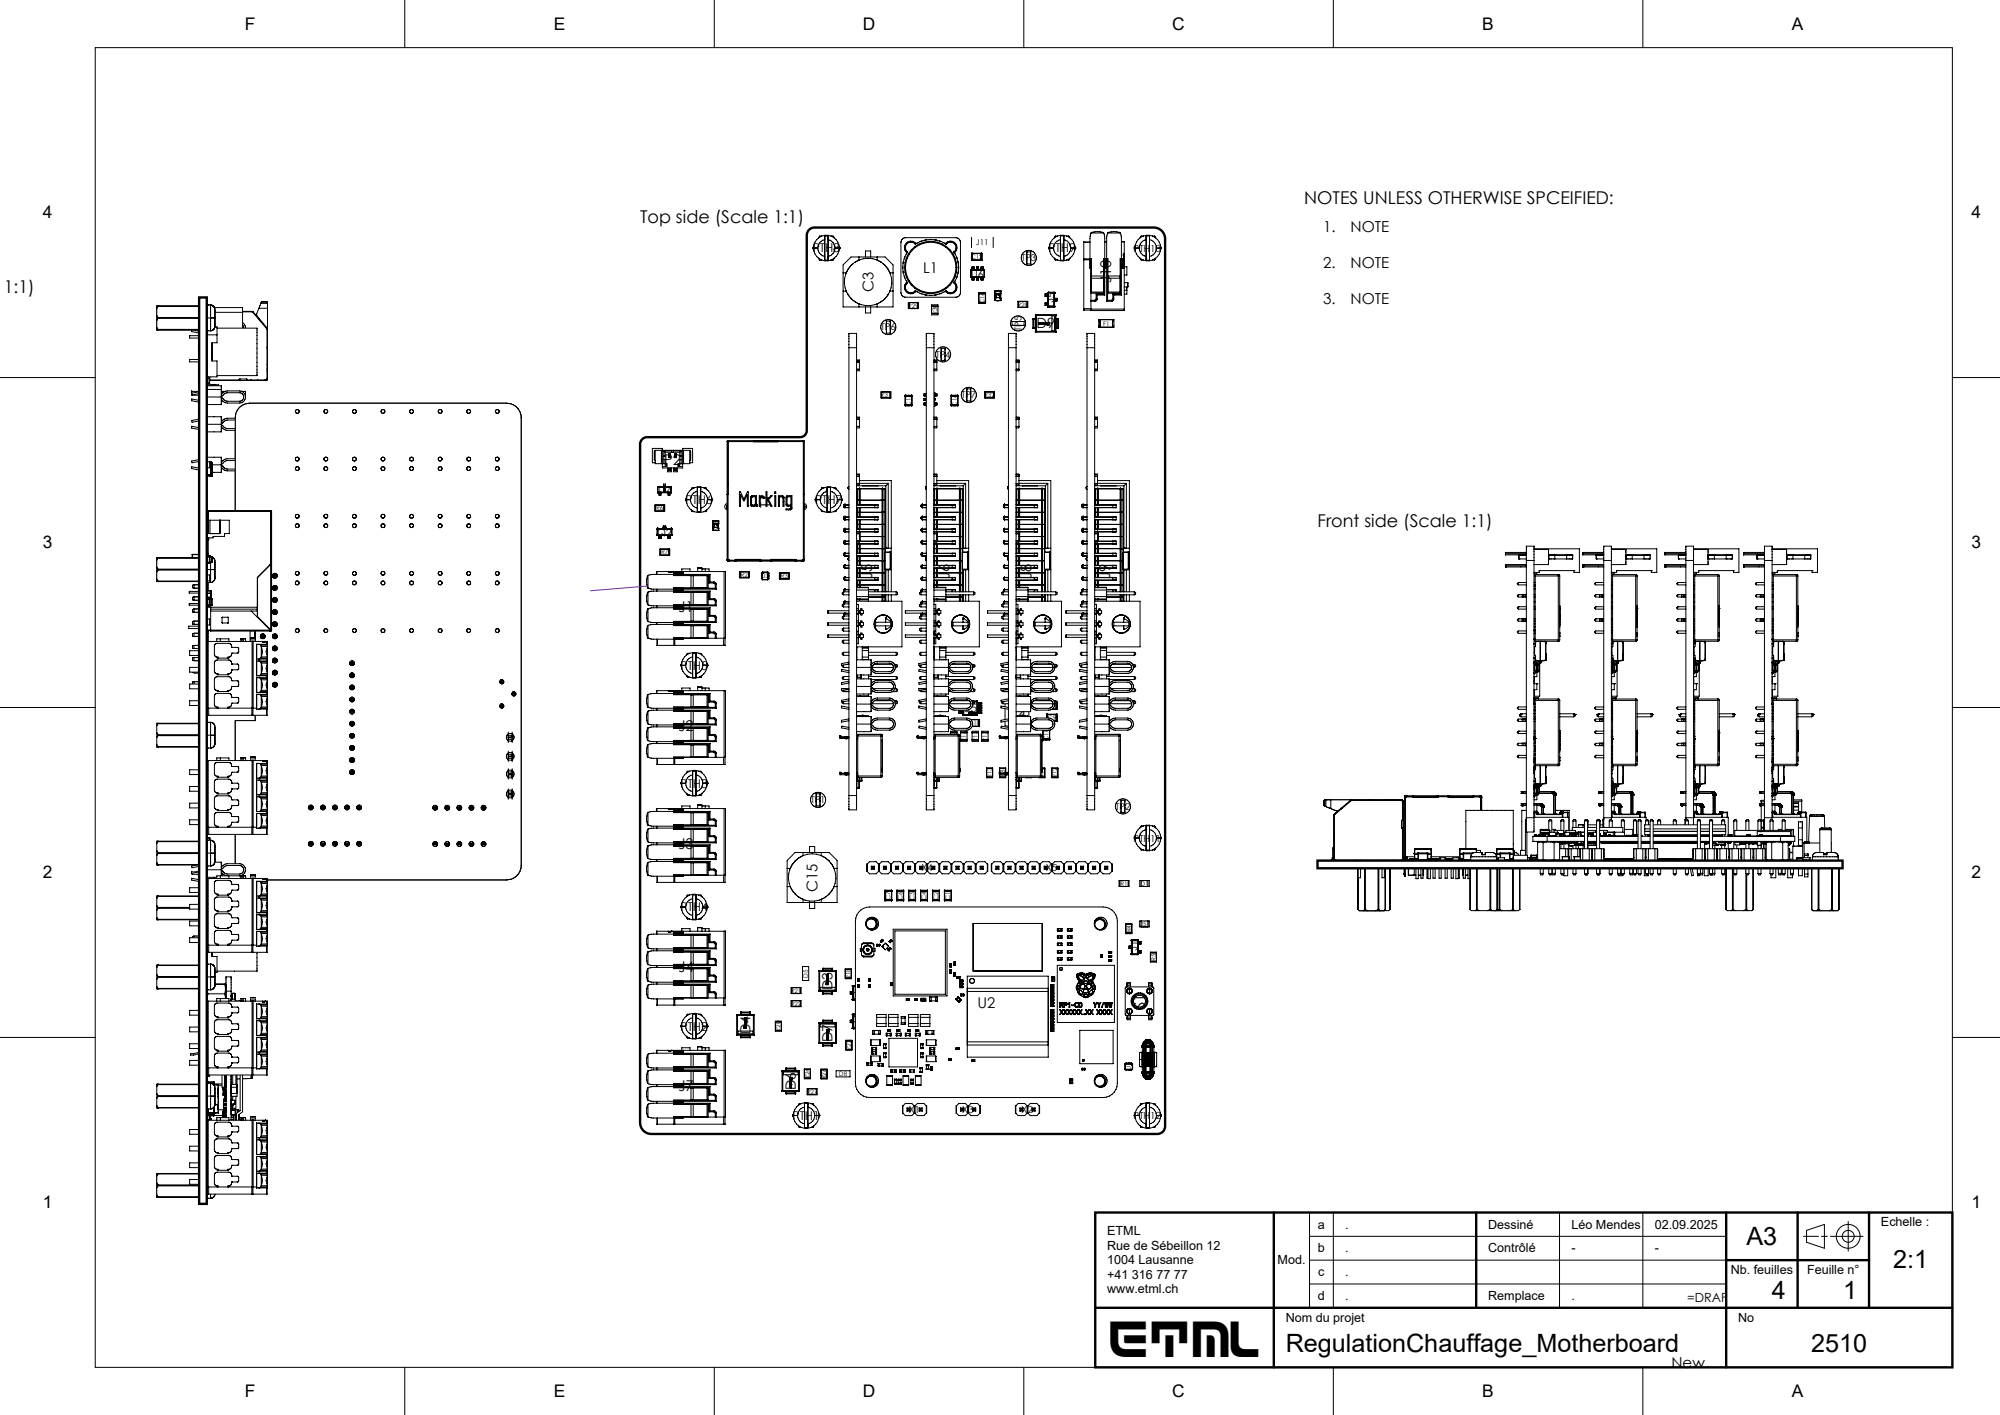
[picture p114: page 1]

NOTES UNLESS OTHERWISE SPCEIFIED:
1. NOTE

b | . | Contrôlé | - | -

4 | 4

## Bottom side (Scale 1:1)

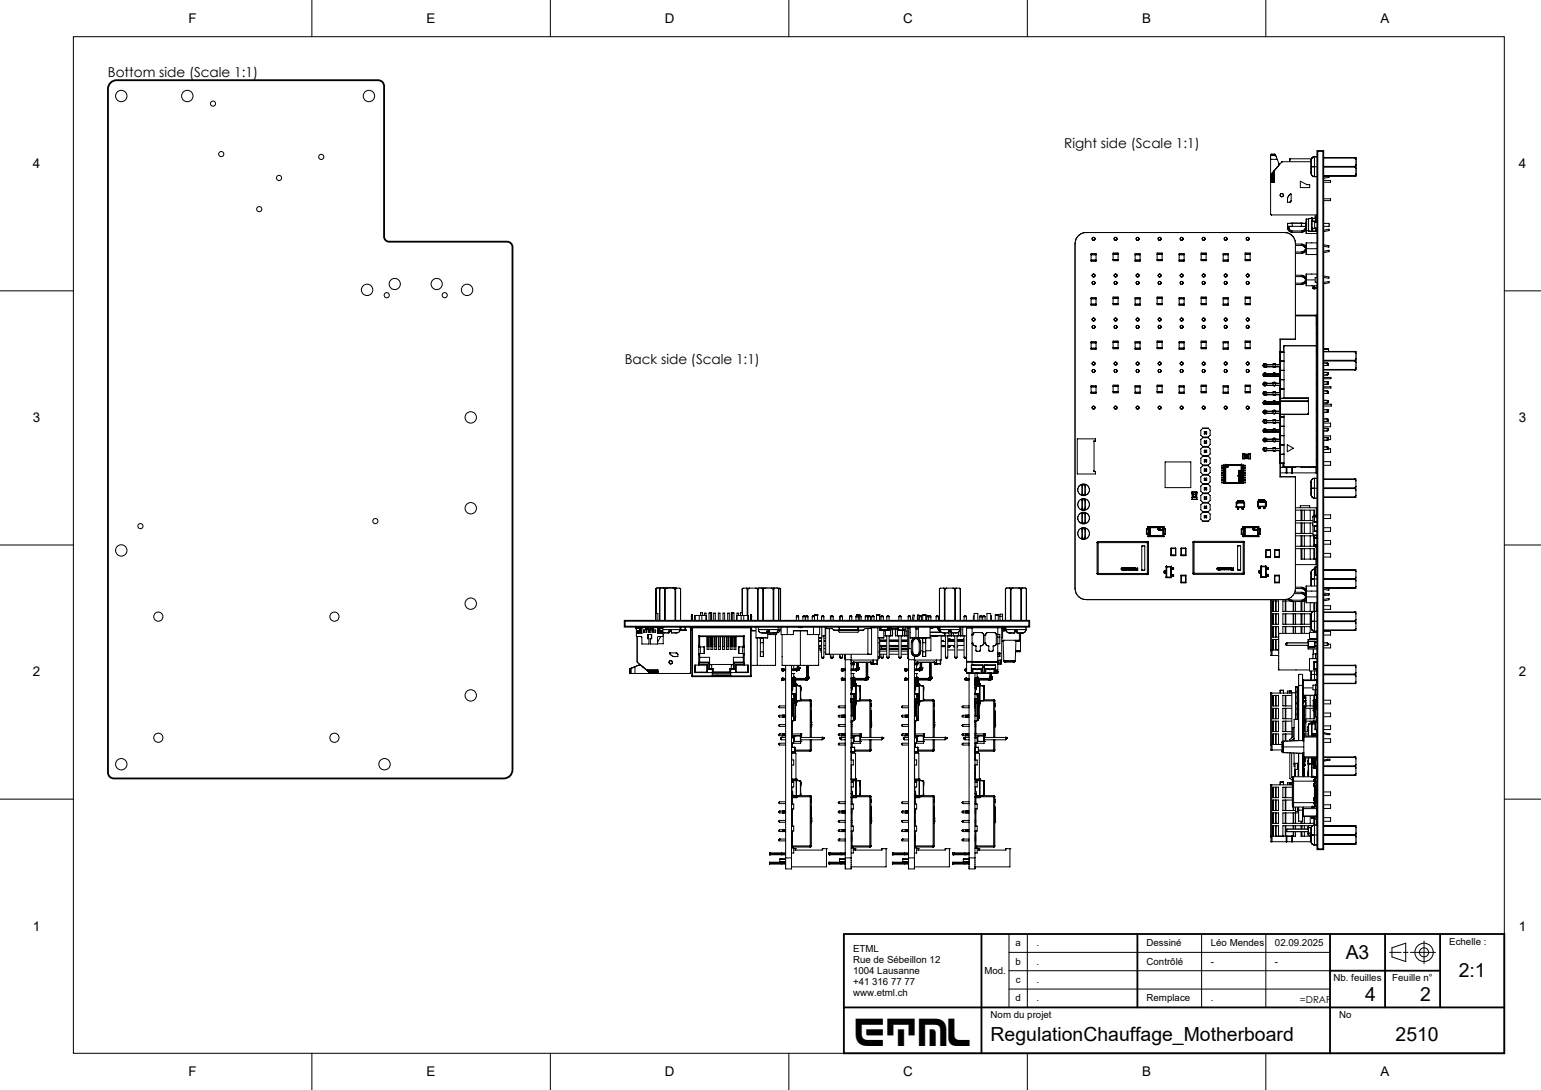
[picture p115: page 2]
=DRAF; Echelle :; Nb. feuilles; Feuille n°; Léo Mendes; Dessiné; Mod.

Right side (Scale 1:1)

Back side (Scale 1:1)

ETML
Rue de Sébeillon 12
1004 Lausanne
www.etml.ch

b | . | Contrôlé | - | -

4 | 4
Top Layer (Scale 1:1) | Bottom Layer (Scale 1:1)

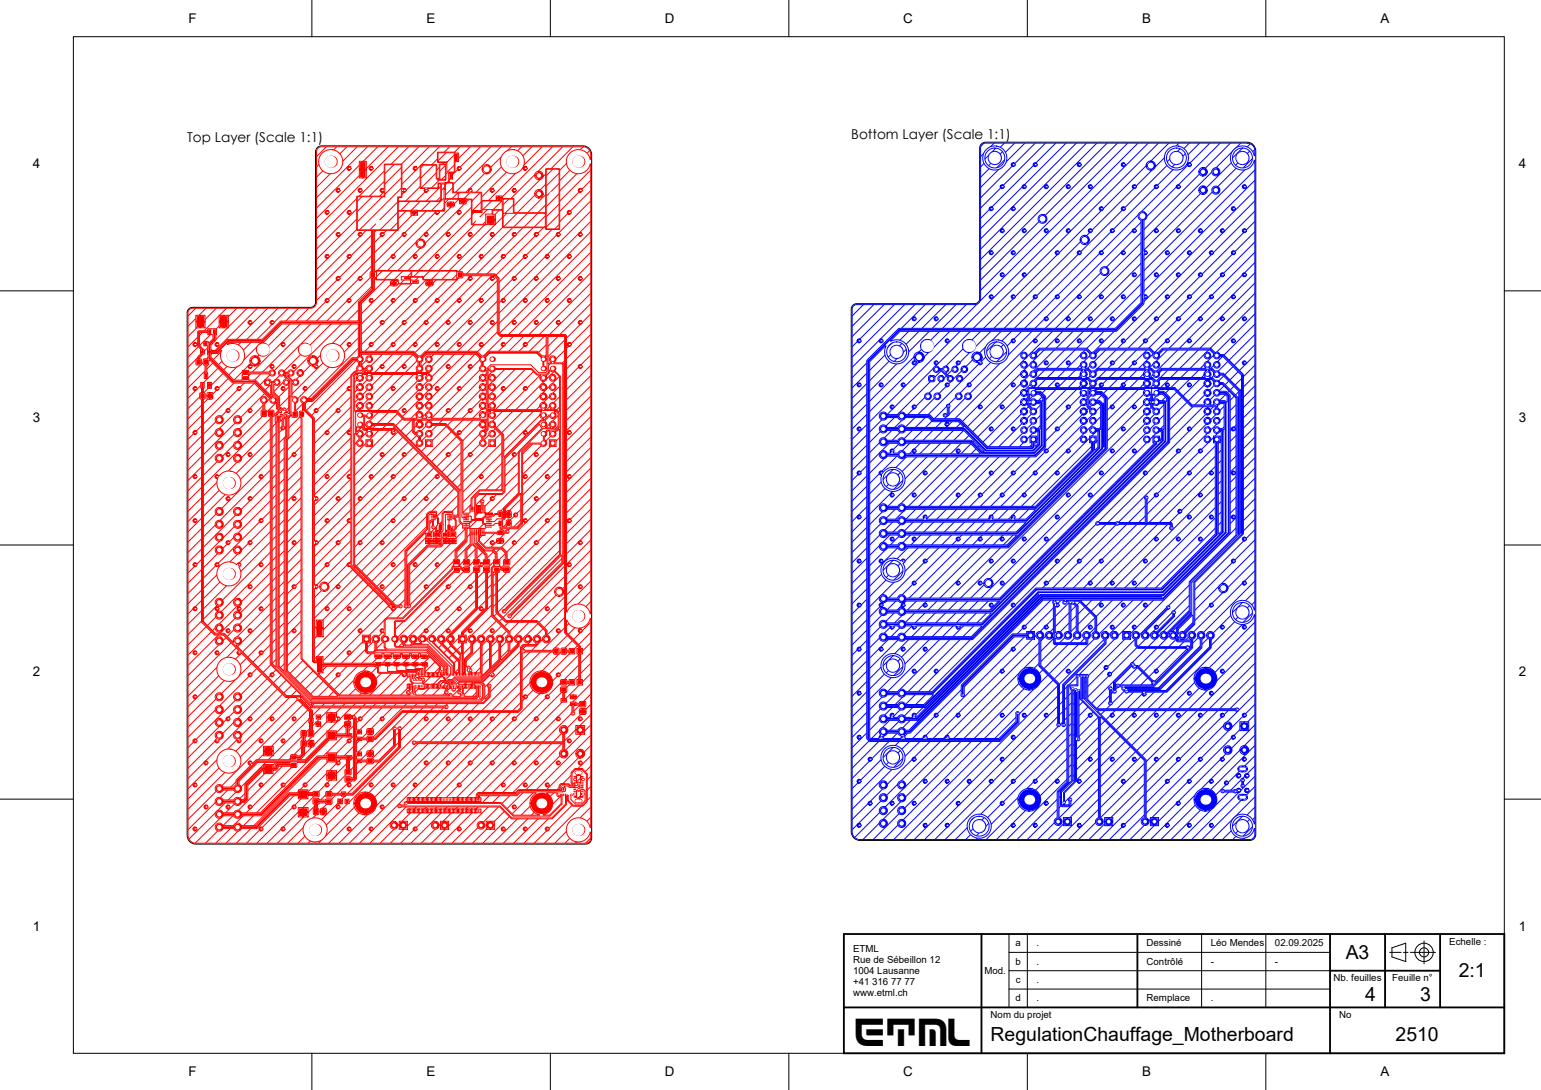
[picture p116: page 3]
Echelle :; Nb. feuilles; Feuille n°; Léo Mendes; Dessiné; Mod.

ETML
Rue de Sébeillon 12
1004 Lausanne
www.etml.ch

b | . | Contrôlé | - | -

4 | 4

## Realistic View

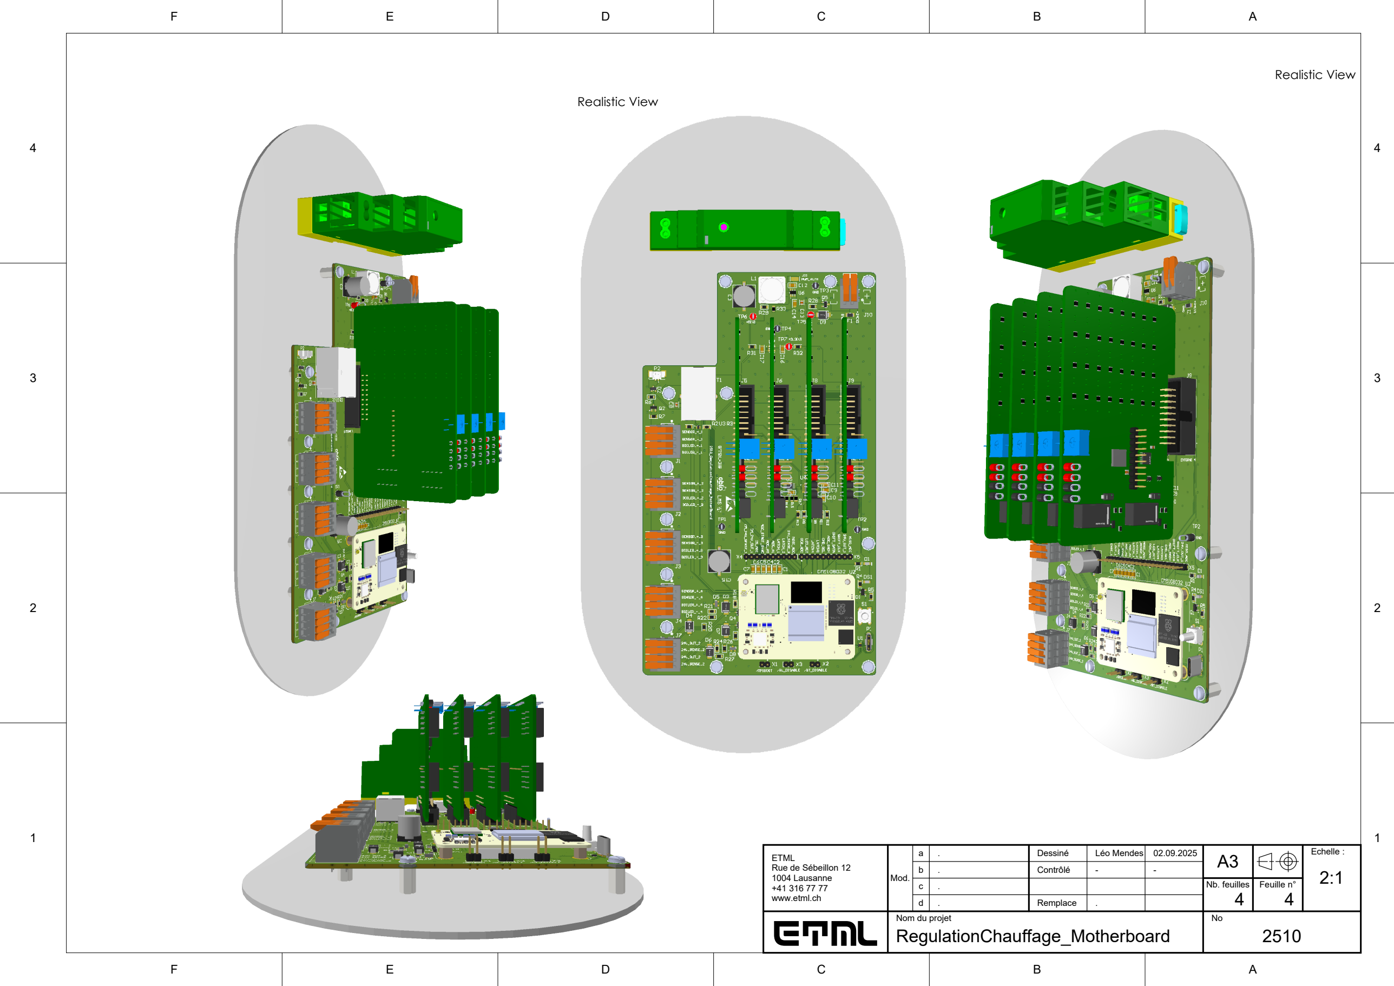
[picture p117: page 4]

3 | 3
2 | 2
1 | 1

2:1

b | . | Contrôlé | - | -
c | .

02.09.2025

Echelle :

4 | 4
Nb. feuilles | Feuille n°

A3

Léo Mendes

Dessiné

Mod.

ETML
Rue de Sébeillon 12
1004 Lausanne
+41 316 77 77
www.etml.ch

a

## Realistic View
